ryusui-hiro/document-svg/plugins/document-svg/skills/document-svg/SKILL.md

---
name: document-svg
description: Convert supported PDF, Office/OpenDocument, web/text, diagram, CAD/CAM/3D, CAE, raster, chart, table, and math inputs into per-page SVG, transform SVG pages (minify, format, scale, remove metadata), or package SVG pages into supported Office, CAD/CAM/3D, diagram, data, HTML viewer, and UI-code outputs with docsvg. Use for document previews and batch conversions; disclose known limits and warnings, and do not claim reverse Office packaging reconstructs document semantics.
---

# Document SVG

Use this skill when the requested output is a directory of self-contained SVG pages. The converter selects the parser from the input file and writes `page-NNNN.svg` plus `conversion.json`.

## Convert

DICOM Part 10 images (`.dcm`, `.dicom`) render one PNG-backed SVG page per frame. DICOM Structured Reports (`.sr.dcm`, `.dicom-sr` or SR SOP Class) render bounded Content Sequence tables. Supported compressed transfer syntaxes include JPEG and JPEG 2000 Part 1 lossless/general (`.90`/`.91`) plus RLE Lossless; JPEG 2000 dimensions/components/precision are checked before decoding. DICOMDIR (`DICOMDIR`, `.dicomdir`) follows image-record offsets and resolves File IDs under the DICOMDIR directory. Image previews omit patient/study attributes, but burned-in pixel text remains and is not anonymized; SR previews carry a separate PHI warning.
DICOM Encapsulated PDF Storage is rendered only when its SOP Class and `application/pdf` MIME type agree. The embedded PDF is limited to 64 MiB and uses the bounded PDF engine; DICOM attributes are omitted, but information already inside the PDF remains.

1. Resolve the input to a local supported file. Common families include PDF/FDF/XFDF form data (`.fdf`, `.xfdf`), legacy Word Binary (`.doc`, CFB `.dot` templates), text-only legacy PowerPoint Binary (`.ppt`), Excel workbooks (`.xls`, `.xlsb`), OOXML Transitional/Strict Office (including Visio `.vsdx`/`.vsdm`/`.vstx`/`.vstm` and legacy Visio XML `.vdx`), Microsoft Project XML schedules, iCalendar (`.ics`) and legacy vCalendar (`.vcs`), vCard contacts (`.vcf`, `.vcard`), MIME e-mail (`.eml`), Apple Mail messages (`.emlx`), Outlook message (`.msg`), MBOX mailbox archives (`.mbox`), MHTML web archives (`.mht`, `.mhtml`), FictionBook 2 XML e-books (`.fb2`, `.fb2.zip`), DocBook 4/5 XML (`.dbk`, `.docbook`), TEI P5 scholarly XML (`.tei`, `.tei.xml`), ALTO OCR/layout XML (`.alto`, `.alto.xml`), METS archive XML (`.mets`, `.mets.xml`), MARCXML (`.marcxml`, `.marc.xml`), MARC21 ISO 2709 (`.marc`, `.iso2709`), PREMIS XML (`.premis`, `.premis.xml`), IIIF Presentation JSON (`.iiif.json`, `.manifest.json`), EAD finding-aid XML (`.ead`, `.ead.xml`), EAC-CPF authority XML (`.eac-cpf`, `.eac`), Dublin Core XML (`.dc.xml`, `.dublin.xml`), ISO 19115/19139 XML metadata (`.iso19115`, `.iso19139`, `.gmd.xml`), OASIS UBL 2.x business XML (`.ubl`, `.ubl.xml`), S1000D Data Module XML (`.s1000d`, `.dmodule`), MODS XML (`.mods`, `.mods.xml`), DITA topics/maps (`.dita`, `.ditamap`), PDB coordinate models (`.pdb`, `.ent`), HWPX (`.hwpx`), COLLADA (`.dae`), X3D (`.x3d`), XMind (`.xmind`), NIfTI (`.nii`, `.nii.gz`), FITS (`.fits`, `.fit`, `.fts`, `.fits.gz`), MRC (`.mrc`, `.map`, `.mrc.gz`), PalmDOC/MOBI e-books (`.mobi`, `.prc`, `.azw`), RTF, XPS/OpenXPS (`.xps`, `.oxps`), standalone JPEG 2000 (`.jp2`, `.j2k`, `.j2c`, `.jpc`, `.jpx`), multi-page TIFF/BigTIFF (`.tif`, `.tiff`), CBZ comic archives (`.cbz`), SubRip/WebVTT subtitles (`.srt`, `.vtt`), TTML/DFXP subtitles (`.ttml`, `.dfxp`), XLIFF localization files (`.xlf`, `.xliff`), Jupyter notebooks (`.ipynb`), Quarto/R Markdown (`.qmd`, `.Rmd`, `.rmarkdown`), V2000/core V3000 MOL/SDF chemical structures (`.mol`, `.sdf`, `.sd`) and V2000 RXN reactions (`.rxn`), Abaqus (`.inp`), LS-DYNA Keyword (`.k`, `.key`), MEDIT ASCII/binary meshes (`.mesh`, `.medit`, `.meshb`), OFF polygon meshes (`.off`), IFC4 BIM (`.ifc`, `.ifcxml`, `.ifczip`), Nastran Bulk Data (`.bdf`, `.nas`, `.nastran`), KiCad PCB boards (`.kicad_pcb`), and UNV/UFF (`.unv`) mesh decks, SU2 CFD meshes (`.su2`), OpenFOAM polyMesh cases (`.foam`), EnSight Gold ASCII cases (`.case`, `.geo`), PLOT3D ASCII grids (`.p3d`, `.plot3d`, `.p3`), VRML97 text meshes (`.wrl`, `.vrml`), ASCII XYZ point rows (`.xyz`), PCL point clouds (`.pcd`), ASTM E57 (`.e57`), Leica PTS unstructured (`.pts`) and PTX structured (`.ptx`) point clouds, ASPRS LAS/LAZ (`.las`, `.laz`), and legacy Excel workbooks (`.xls`, `.xlt`, `.xla`), SYLK spreadsheets (`.slk`), DIF tables (`.dif`), FASTA/FASTQ sequences (`.fa`, `.fasta`, `.fq`, `.fastq`), GFF3/GTF annotations (`.gff`, `.gff3`, `.gtf`), BED/BEDGraph intervals (`.bed`, `.bedgraph`, `.bg`), VCF variants (`.vcf`), SAM alignments (`.sam`), WIG/Wiggle signals (`.wig`, `.wiggle`), MAF multiple alignments (`.maf`), Newick phylogenetic trees (`.nwk`, `.newick`, `.tree`), Stockholm alignments (`.sto`, `.stockholm`), CLUSTAL alignments (`.aln`, `.clustal`, `.clustalw`), NEXUS trees (`.nex`, `.nexus`), GenBank flat files (`.gb`, `.gbk`, `.genbank`), EMBL-Bank flat files (`.embl`, `.emb`), UniProtKB/Swiss-Prot protein flat files (`.dat`, `.uniprot`, `.swissprot`), RIS bibliography (`.ris`), SPICE/ngspice netlists (`.cir`, `.sp`, `.spice`, `.ckt`, `.net`), KiCad legacy Eeschema schematics (`.sch`), KiCad 6+ S-expression schematics (`.kicad_sch`), LTspice schematics (`.asc` Version signature), Autodesk EAGLE XML schematics (`.sch` eagle signature), plus Excel Binary Workbook (`.xlsb`); OpenDocument Text/spreadsheets/presentations/drawings (`.odt`, `.ott`, `.fodt`, `.ods`, `.ots`, `.fods`, `.odp`, `.otp`, `.fodp`, `.odg`, `.otg`, `.fodg`); HTML/EPUB/Markdown/plain text/AsciiDoc (including bounded local `image::target[attrs]` PNG/JPEG block macros)/reStructuredText (`.rst`, `.rest`)/Org-mode (`.org`)/GNU gettext catalogs (`.po`, `.pot`)/BibTeX (`.bib`, `.bibtex`); draw.io, BPMN 2.0 (`.bpmn`, `.bpmn2`), CMMN 1.1 (`.cmmn`), DMN 1.1–1.5 (`.dmn`), ReqIF (`.reqif`), XMI (`.xmi`), DOT, Mermaid, PlantUML, D2, Excalidraw; ARFF (`.arff`), JSON-LD 1.1 (`.jsonld`, `.json-ld`), NetCDF classic (`.nc`, `.nc3`, `.cdf`), GraphML (`.graphml`), GEXF (`.gexf`), XGMML (`.xgmml`), Graph Modeling Language (`.gml`), CSV/TSV, TOML (`.toml`), YAML 1.2 (`.yaml`, `.yml`), Java Properties (`.properties`), generic XML (`.xml` fallback), and JSON (`.json`), RFC 7464 JSON Text Sequences (`.jsons`, `.jsonseq`, `.jsonl`), dBASE III/III+ tables (`.dbf`), GeoPackage (`.gpkg`), RFC 8142 GeoJSON Text Sequences (`.geojsons`, `.geojsonseq`) and newline-delimited `.geojsonl`, TopoJSON (`.topojson`), GeoJSON/GeoRSS/GML/GPX/KML/KMZ, ESRI Shapefile (`.shp`) and WKT/EWKT map geometries (`.gpkg`, `.geojsons`, `.geojsonl`, `.topojson`, `.geojson`, `.rss`, `.atom`, `.georss`, `.gml`, `.gpx`, `.kml`, `.kmz`, `.shp`, `.wkt`, `.ewkt`), charts, LaTeX formulas and bounded complete-document previews (including local PNG/JPEG \includegraphics), QR, raster/SVG/SVGZ; and CAD/CAM/CAE such as ASAM OpenDRIVE `.xodr`, ASAM OpenSCENARIO `.xosc`, ASCII/Binary DXF, Gerber, HP-GL, G-code, Excellon, STL/3MF/glTF/GLB/STEP/IGES/OBJ/PLY, Gmsh, and VTK (`.vtk`, `.vtu`, `.vtp`, `.vti`, `.vtr`, `.vts`). Read `docs/SUPPORT.md` for exact format coverage and limitations.
2. Choose a dedicated output directory. If the user did not name one, use `<input-stem>-svg` beside the input. Never reuse a non-empty directory unless the user explicitly asks to mix or replace its contents.
3. Run the bundled wrapper using its absolute path from this skill directory:

   ```bash
   scripts/convert-document.sh <input> <output> [docsvg options]
   ```

   Use `--jobs N` only to parallelize PDF pages. Keep the default limits unless the user explicitly needs different bounds.
   Use `--outline-embedded-pdf-text` only when the user explicitly prioritizes PDF visual fidelity over editable SVG text. Report every resulting font-rights warning and do not describe outlined text as editable.
4. Read `<output>/conversion.json`. Report the page count, source format, output directory, and every top-level or page warning. Treat a non-empty `warnings` array or a positive page `warning_count` as requiring review; do not describe that result as a perfect reproduction.
5. When visual fidelity matters, render or inspect representative SVG pages with the available image/browser tooling.
   For Codex/app previews, prefer a deterministic PNG companion because Markdown, Quick Look,
   and embedded browser SVG support can differ. Run:

   ```bash
   scripts/render-preview.sh <svg-file-or-directory> <new-preview-directory> [width]
   ```

   Display the generated absolute `.png` path in Codex and link the original `.svg` separately.
   Read `preview.json` for page ordering. The preview runner rejects active SVG content and refuses
   non-empty output directories.

## Transform SVG

1. Resolve the input to an `.svg` file.
2. Choose an output file path (e.g. `<input-stem>.transformed.svg`).
3. Run:

   ```bash
   scripts/transform-document.sh <input.svg> <output.svg> [options]
   ```

   Supported transform options:
   - `--minify`: Strip unnecessary whitespace, comments, and redundant tokens to reduce file size.
   - `--responsive`: Remove fixed width/height and ensure viewBox is set for responsive web scaling.
   - `--monochrome <color>`: Unify all fill and stroke colors to a single monochrome color (e.g. `#000000`).
   - `--precision <digits>`: Clamp coordinate precision to N decimal digits.
   - `--remove-metadata`: Strip `<metadata>`, `<desc>`, and `data-*` attributes.

## Reverse to OOXML, PDF, CAD, CAM, or draw.io

1. Resolve the input to one `.svg` file or a directory containing SVG pages. Directory pages are ordered lexicographically, so prefer `page-NNNN.svg` names.
2. Choose a new output file ending in a supported extension, such as `.pptx`, `.docx`, `.xlsx`, `.pdf`, `.drawio`, CAD/CAM/3D (`.dxf`, `.gcode`, `.gbr`, `.plt`, `.drl`, `.stl`, `.3mf`, `.obj`, `.ply`, `.step`, `.iges`), simulation (`.msh`, `.vtk`), diagrams (`.dot`, `.mmd`), data/math (`.md`, `.csv`, `.tex`), PNG, WebP, standalone HTML viewer (`.html`), React/Vue/Svelte code, SVG path data, or `.datauri`.
3. Run:

   ```bash
   scripts/reverse-document.sh <input.svg-or-directory> <output>
   ```

4. Report the output format and page count, and always disclose that Office outputs embed SVGs as vector images with PNG compatibility fallbacks (PPTX uses one SVG per slide, DOCX one SVG per page, and XLSX one SVG per sheet). CAD/CAM/CAE outputs (`.dxf`, `.gcode`, `.gbr`, `.plt`, `.drl`, `.stl`, `.obj`, `.step`, `.msh`, `.vtk`) generate native vector geometry, 3D meshes, boundary curves, toolpaths, or simulation grids.
5. Do not describe reverse conversion as a lossless restoration of the original Office document. Paragraphs, tables, spreadsheet cells and formulas, charts, comments, masters, and other semantics are not reconstructed.
6. A `.drawio` output is the exception: an SVG that still carries its diagram source is restored as editable shapes. That applies to draw.io's own exports made with "Include a copy of my diagram" and to SVGs this converter wrote with `--embed-drawio-source`. The report says how many pages were restored that way; report that number instead of assuming, because the rest are pictures inside a diagram.

## CLI availability

The repository installer normally places `docsvg` on `PATH`. If it is unavailable, the wrapper can run the checked-out Rust repository when either the current directory is that repository or `DOCUMENT_SVG_REPO` points to it. Otherwise, ask the user to run `./scripts/install-codex-plugin.sh` from the repository root.

## Constraints

- The converter intentionally rejects encrypted PDFs and does not bypass access controls.
- Legacy PowerPoint Binary `.ppt` presentations follow the live `CurrentUserAtom`/`UserEditAtom`/persist-directory chain, then extract UTF-16 or low-byte Unicode text from slide OfficeArt textboxes and outline references into A4 flow pages. Slide geometry, visual styles, images, charts, tables, media, notes, and embedded objects are omitted; encrypted decks are rejected. See `docs/SUPPORT.md` for limits.
- Legacy Word Binary `.doc` documents and CFB `.dot` templates (`.dot` is content-sniffed to preserve Graphviz) extract the main-story text from the bounded FIB/CLX piece table or simple text range. UTF-16 and common compressed code pages are supported. Text is flowed to A4 pages; tables are flattened, and original formatting, pagination, images, headers/footnotes and embedded objects are omitted. Encrypted files are rejected; macros are never executed. See `docs/SUPPORT.md` for limits.
- KiCad PCB `.kicad_pcb` files are parsed as bounded S-expressions. The 2D preview renders common tracks, vias, pads, Edge.Cuts, board/footprint artwork, and cached zone fills; it never evaluates DRC, refills zones, opens 3D/image paths, or loads external libraries. Unsupported custom pads/curves and non-unit affine-scaled footprints are warned and omitted.
- PDF JPXDecode grayscale/RGB/CalGray/CalRGB images with 1–16-bit unsigned, full-resolution components are dimension-checked and decoded to PNG within fixed limits. One embedded alpha channel is preserved when `SMaskInData=1`; DeviceGray/DeviceRGB/CalGray/CalRGB preblended mode 2 is unblended using a valid `/Matte`, and bounded DeviceGray external `/SMask` images are applied when no matte or nested mask is present. Default/0 ignores embedded alpha. Explicit `/Mask`, unsupported matte or soft-mask color spaces, unsupported JPX color spaces, and subsampling remain as JPEG 2000 data with a warning; PDF-level masks may be lost from the SVG fallback. `BitsPerComponent` is taken from the codestream as required by PDF.
- OpenDocument Text previews preserve headings, paragraphs, lists, and tables, and embed bounded package-linked PNG/JPEG images as centered flow blocks. Legacy OpenOffice XML packages (`.sxw`, `.stw`, `.sxg`) are routed through the same bounded ODT engine after validating their `application/vnd.sun.xml.*` mimetype. Styles and exact pagination are not reconstructed; image anchors and wrapping are approximated, and external or inline-binary images are reported and omitted.
- EPUB previews follow the OPF spine and embed bounded package-linked PNG/JPEG XHTML `img` resources. Remote references, CSS backgrounds, SVG and other image sources are not fetched or reconstructed.
- DocBook 4/5 `.dbk`/`.docbook` previews render bounded titles, sections, paragraphs, lists, source blocks, simple tables, and validated local PNG/JPEG `imagedata`/`graphic` resources. DTDs, XInclude, external links, MathML, scripts, and publisher extensions remain inert.
- Standalone HTML previews embed bounded relative PNG/JPEG `img src` files only when canonical paths remain inside the input directory tree. Image placement, CSS sizing and wrapping are approximated; external and escaping paths are not fetched.
- Markdown previews embed bounded local PNG/JPEG resources from standalone or paragraph `![alt](path)` references when resolved paths remain inside the input directory tree; images render as flow blocks, while heading/list/quote/table/code images stay as alt text.
- OpenDocument Spreadsheet previews preserve cached cell values and embed bounded package-linked PNG/JPEG images after each sheet table; legacy OpenOffice XML packages (`.sxc`, `.stc`) use the same safe package checks. Cell anchoring, chart/vector drawings, styles, and formula recalculation are not reproduced.
- OpenDocument Presentation/Drawing previews preserve page order, size, common vector shapes, editable text, and bounded PNG/JPEG images linked from the ODF package. Legacy OpenOffice XML presentations/drawings (`.sxi`, `.sti`, `.sxd`, `.std`) are accepted through the same engines. External and inline binary images plus charts, tables, OLE, and advanced effects are omitted or approximated with warnings; see `docs/SUPPORT.md` for limits.
- Visio Open XML (`.vsdx`/`.vsdm`/`.vstx`/`.vstm`) and legacy VDX XML use bounded page/ShapeSheet rendering; legacy Visio CFB (`.vsd`/`.vss`/`.vst`/`.vsw`) is summarized as inert stream metadata without decoding opaque drawing payloads.
- ZIP-backed Apple iWork Pages/Numbers/Keynote packages (`.pages`/`.numbers`/`.key`) expose bounded package marker metadata only; IWA protobuf, formulas, media, previews, scripts and external links remain inert. `.key` is distinguished from LS-DYNA by ZIP signature.
- Autodesk DWG (`.dwg`) reads only the six-byte AC10xx version header and file size; compressed sections, entities, macros, embedded objects and external references remain inert.
- Nastran Output2 (`.op2`) performs bounded record-framing and table-label preflight only; model/result payloads, external paths and solver operations remain inert.
- IPC-2581 (`.ipc2581`/`.ipc-2581`/`.cvg`) summarizes PCB Content/BOM/ECAD/AVL structure and manufacturing counts without rendering coordinates, toolpaths, attachments or executing operations.
- Siemens JT (`.jt`) reads only the fixed Version header and byte-order marker; TOC/LSG, tessellation, Parasolid geometry, PMI and external resources remain inert.
- Rhino/OpenNURBS 3DM (`.3dm`) reads only the stable start marker and bounded header bytes; NURBS/mesh chunks, plug-ins, textures and external resources remain inert.
- Microsoft Access ACE/Jet (`.accdb`/`.accde`/`.mdb`/`.mde` and related extensions) reads only the first-page engine marker and bounded metadata; database objects, VBA/data macros, attachments, encryption and linked paths remain inert.
- Dassault 3DXML (`.3dxml`) validates the local Manifest→Root relationship and bounded product-structure XML; binary 3DRep tessellation, external files, textures and viewer automation remain inert.
- HDF5 scientific containers (`.h5`/`.hdf5`/`.hdf`/`.h5part`) and CGNS/HDF5 CFD files (`.cgns`) are preflighted from their signature and superblock without loading datasets, links, filters, or solver payloads.
- RTF previews preserve supported ANSI codepages, Unicode escapes, paragraphs, explicit `\page` breaks, bounded embedded PNG/JPEG pictures, and declared picture goal dimensions. Anchors/cropping/wrapping are approximated; EMF/WMF pictures, objects, and unsupported media are omitted with warnings.
- XPS/OpenXPS (`.xps`/`.oxps`) and Autodesk DWFx (`.dwfx`) follow internal fixed-document relationships and render basic Path/Glyphs content plus embedded PNG/JPEG ImageBrushes clipped to Path bounds. Embedded fonts, exact glyph advances, gradients/cropping and resource dictionaries are warned or approximated; classic DWF payloads and external resources are never fetched.
- TIFF/BigTIFF (`.tif`/`.tiff`) emits one SVG per image directory and embeds a decoded PNG. Unsigned-integer grayscale (including packed 1/2/4-bit samples), RGB/RGBA, and CMYK are supported; WhiteIsZero/BlackIsZero is honored and channels above 8-bit are reduced to 8-bit. Palette, signed/floating-point samples, and ICC profiles are not interpreted. Per-page and total pixel/data limits and `max_pages` apply.
- DICOM Part 10 (`.dcm`, `.dicom`) emits one SVG per image frame and applies available Modality/VOI transformations. Patient/study metadata is omitted, but burned-in annotations remain; the preview is not de-identification. Only grayscale/RGB 8/16-bit pixels and supported transfer syntaxes are decoded; JPEG 2000 Part 1 `.90`/`.91` frame dimensions, component count, precision, signedness and subsampling are checked against DICOM attributes before decode. JPEG-LS, JPEG 2000 YBR_RCT/YBR_ICT color conversion, Part 2, HTJ2K, orientation and physical pixel spacing are not handled.
- DICOMDIR (`DICOMDIR`, `.dicomdir`) follows root/next/lower-level Directory Record offsets and renders referenced `IMAGE` records in hierarchy order. File IDs are validated and canonicalized inside the DICOMDIR folder, and duplicate/missing/unsupported references are skipped with warnings.
- DICOM Encapsulated PDF Storage (`1.2.840.10008.5.1.4.1.1.104.1`) accepts only `application/pdf`, checks the optional declared length and padding, and renders the bounded embedded stream with the PDF engine. DICOM attributes are not copied, but PDF content can still identify a patient, so the preview is not de-identification.
- FDF form data (`.fdf`; content sniffing) uses the PDF object/xref grammar to render fully-qualified field hierarchy, types, safe values, password masking, choice options and action/attachment counts. JavaScript, submit/launch actions, file specifications, embedded files and external URLs remain inert or redacted; no form submission or PDF page rendering runs. Limits are 64 MiB input, 500,000 objects, depth 64, 100,000 fields, 2 MiB/value and 32 MiB total values. Source: [Adobe FDF reference](https://opensource.adobe.com/dc-acrobat-sdk-docs/pdfstandards/pdfreference1.2.pdf).
- XFDF XML form data (`.xfdf`, `.xfdf.xml`; content sniffing) renders bounded fully-qualified field/value hierarchy, sensitive-field masking, rich-text and annotation counts, and PDF target/ID counts. PDF references, actions, JavaScript, rich-text payloads, appearance data and external URLs remain inert or redacted; no form submission, annotation import or PDF rendering runs. Limits are 64 MiB input, 1,000,000 XML events, 500,000 nodes, depth 96, 100,000 fields and 100,000 rows. Source: [ISO 19444-1 XFDF](https://www.iso.org/standard/74272.html).
- DICOM Structured Reports (SR) render Basic Text, Enhanced, Comprehensive, Comprehensive 3D, Extensible, CAD, dose, agent and related SOP Classes as bounded Content Sequence rows for TEXT/NUM/CODE/CONTAINER items, concepts, units and relationships. Referenced images/audio/waveforms, UIDs and patient/study attributes are omitted; SR content may contain PHI and is not de-identification. Limits are 128 MiB input, 1,000,000 structural tokens, 100,000 elements, depth 64 and 200,000 rows. Source: [DICOM PS3.3 Structured Report IODs](https://dicom.nema.org/medical/dicom/current/output/chtml/part03/sect_A.35.html).
- Microsoft Project XML (`.xml` with the Microsoft Project namespace, or `.mspdi`) renders bounded task Gantt pages with supplied dates, progress, milestones, and simple predecessor arrows. It rejects DTDs, does not fetch links or external entities, and does not recalculate work calendars or schedules; see `docs/SUPPORT.md` for limits.
- PCL PCD (`.pcd`) accepts ASCII, little-endian binary, and LZF-compressed point clouds. Bounded XYZ point marks preserve packed or separate RGB colors, quantized only above 512 color groups. Other fields and non-default VIEWPOINT poses are not applied.
- XYZ ASCII (`.xyz`) accepts common named coordinate/intensity/RGB/normal columns or homogeneous 3/4/6/7/9/10-field layouts with whitespace/comma separators. Intensity is scaled across the observed range; units, CRS and sensor pose are not inferred. Black RGB is retained and normals are omitted.
- ASTM E57 (`.e57`) reads CRC-protected XML and point-data pages, applies per-scan poses, converts spherical coordinates, and preserves normalized RGB or intensity. It caps decoding at 20 million points and previews at 200,000 points. Scan images, CRS reprojection, and non-coordinate attributes are omitted.
- Leica PTS (`.pts`) reads bounded unstructured XYZ/intensity or XYZ/intensity/RGB records; legacy signed integer and normalized decimal intensity are mapped to grayscale, and Leica's reserved no-color RGB uses a blue fallback. The origin is valid; one deterministically sampled page is capped at 200,000 points.
- Leica PTX (`.ptx`) reads structured multi-scan grids, applies the per-scan registration transform and preserves RGB, or displays intensity-only scans in grayscale. Missing XYZ cells and sensor/grid metadata are omitted; deterministic sampling is capped at 200,000 points total.
- Legacy Excel (`.xls`, `.xlt`, `.xla`) renders cached cell values in bounded worksheet pages after validating BIFF dimensions, cell coordinates, and shared-string expansion. Hidden sheets are included with a warning. Formula recalculation, styling, merged-cell geometry, charts, and drawings are omitted; macros are never executed.
- SYLK `.slk` parses bounded `ID`/`B`/`C`/`F`/`E` records into paginated inert tables. Cell coordinates and cached values are retained; formulas, formatting, and other metadata are never evaluated.
- DIF `.dif` parses bounded TABLE/VECTORS/TUPLES/DATA headers and BOT/EOD tuples into inert paginated tables. Numeric, string, boolean, NA and ERROR values are displayed without formula evaluation.
- FASTA/FASTQ sequence files render bounded identifier, length, GC/ambiguity and sequence/quality summaries. FASTQ sequence and quality lengths are checked; no alignment or Phred conversion is performed.
- GFF3/GTF `.gff`/`.gff3`/`.gtf` renders validated nine-column feature annotations and attributes. Directives and embedded FASTA tails are omitted; no hierarchy or sequence analysis executes.
- BED `.bed` and bedGraph `.bedgraph`/`.bg` validate zero-based half-open intervals, optional BED12 blocks and finite signal values as inert tables. Track/browser directives and remote lookups are never loaded.
- VCF `.vcf` renders validated fixed variant columns plus inert FORMAT/sample fields. Metadata/reference URLs and embedded FASTA are omitted; vCard `.vcf` is selected when the VCF signature is absent.
- SAM `.sam` renders validated 11-field alignments and optional tags as inert tables. Header metadata and reference URLs are ignored; no CIGAR projection, genotype analysis, or external resource access occurs.
- WIG/Wiggle `.wig`/`.wiggle` expands fixedStep and variableStep signal declarations into bounded one-based closed interval tables. Track/browser and remote references are ignored.
- MAF `.maf` renders bounded `a`/`s` multiple-alignment blocks with coordinate and ungapped-size validation. Optional metadata, reference lookup and coordinate liftover remain inert.
- Newick `.nwk`/`.newick`/`.tree` renders the first bounded semicolon-terminated phylogenetic tree as a directed graph. Quoted labels, finite branch lengths and nested comments are validated; extra trees, taxonomy/sequence lookup, rooting and distance calculations remain inert.
- Stockholm `.sto`/`.stockholm` renders bounded Stockholm 1.0 alignment blocks, including split sequence rows. `#=GF`/`#=GS`/`#=GC`/`#=GR` annotations remain inert and external profile/sequence lookups are never performed.
- CLUSTAL `.aln`/`.clustal`/`.clustalw` renders bounded block alignments; sequence fragments are concatenated, residue counts and consensus rows remain inert, and external lookup or alignment execution is never performed.
- NEXUS `.nex`/`.nexus` extracts the first bounded `TREE`/`UTREE` statement from `BEGIN TREES` and renders it through the Newick graph path. TAXA/TRANSLATE metadata and additional blocks remain inert.
- GenBank `.gb`/`.gbk`/`.genbank` renders bounded LOCUS metadata, feature counts, and ORIGIN sequence previews as inert tables. Accessions, feature locations, and external sequence resources are never resolved.
- EMBL-Bank `.embl`/`.emb` renders bounded ID/AC/DE/FT/SQ records and sequence previews as inert tables. Database cross-references, feature locations, and external sequence resources are never resolved.
- UniProtKB/Swiss-Prot `.dat`/`.uniprot`/`.swissprot` renders bounded ID/AC/DE/GN/OS/FT/SQ protein records. Reviewed status, accessions, metadata, feature counts and sequence previews are inert; REST, taxonomy and cross-reference lookups never run.
- RIS `.ris` renders bounded `TY`/`ER` citation records with authors, title, date, journal, pages, DOI, URL, keywords and abstract previews. Six-space continuations are supported; DOI/URL and external citation lookups remain inert.
- SPICE/ngspice `.cir`/`.sp`/`.spice`/`.ckt`/`.net` renders bounded element cards, nodes and values as inert tables. Dot commands, `.include`/`.lib` paths, models and simulation controls are never executed or opened.
- KiCad legacy Eeschema `.sch` renders bounded `$Comp`, wires, labels, notes, and junctions as a deterministic mil-coordinate approximation. Cache libraries, external symbols, images, models, and DRC/ERC are never loaded.
- KiCad 6+ `.kicad_sch` renders bounded S-expression symbol instances, wire/bus segments, labels, text, and junctions. Embedded library definitions, pin connectivity, hierarchy, images, models, and ERC/DRC remain inert.
- LTspice `.asc` with a `Version` header renders bounded WIRE/FLAG/SYMBOL/SYMATTR/TEXT and basic graphics, including BOM-marked UTF-16. `.asy` libraries, external models, includes, and simulation commands are never opened or executed; ESRI ASCII Grid signatures remain separate.
- Autodesk EAGLE XML `.sch` with an `<eagle>` root renders bounded parts, instances, wires, labels, and text. Library package geometry, scripts, external files, pin connectivity, and DRC/ERC remain inert; KiCad legacy `.sch` is selected by its own signature.
- Excel Binary Workbook (`.xlsb`) streams cached worksheet values into bounded pages after checking ZIP entries, BIFF12 record lengths, used ranges, and shared-string expansion. Hidden worksheets are included with a warning. Formulas are not recalculated, styles and charts are omitted, macros are never executed, and macro-sheet workbooks are unsupported.
- ASPRS LAS/LAZ (`.las`, `.laz`) supports LAS 1.0–1.4 with optional RGB and deterministic point samples capped at 200,000. Uncompressed LAS uses seeks; LAZ decoding is capped at 20 million source points. CRS transforms and other point attributes are omitted.
- V2000/core V3000 MOL/SDF (`.mol`, `.sdf`, `.sd`) draws bounded atom/bond connection tables one molecule per page. Supplied coordinates, common bond orders, formal charges/isotopes, and up/down single-bond wedges and hash marks are shown; SDF data fields are omitted and never evaluated. Core V3000 atom/bond tables are supported; Sgroups, advanced stereochemistry, query chemistry and chemical calculations are unsupported.
- V2000 RXN (`.rxn`) renders a single reaction page with up to two reactants and two products. It reuses the MOL depiction in separate panels with plus signs and a reaction arrow; V3000 RXN containers, conditions, agents, and chemical validation are omitted.
- ESRI Shapefile (`.shp`) renders point, line, polygon and multipoint records, validates an optional SHX index, and accepts recognized degree-based WGS 84 geographic PRJ metadata. Missing PRJ is explicitly treated as an assumption; projected, non-degree or unknown CRS is rejected because reprojection is not applied. DBF fields and Z/M values are omitted; MultiPatch is unsupported.
- ESRI ASCII Grid (`.asc`) reads NCOLS/NROWS, a matching lower-left corner or center origin, CELLSIZE, optional NODATA_VALUE (default -9999), and row-major cell values. It produces a PNG-backed SVG heatmap with transparent NoData cells and a value legend; an all-NoData grid stays transparent without a numeric scale. CRS reprojection and thematic class breaks are not applied. Input, dimensions, cell count, line length, and encoded PNG size are bounded.
- dBASE III/III+ (`.dbf`) reads bounded classic 32-byte-descriptor tables and paginates 100 rows × 32 columns. Character, numeric, float, logical and date fields render; deleted rows are skipped; memo/unsupported fields are placeholders. Common `.cpg` aliases are decoded; unsupported versions/code pages fail clearly. `docs/SUPPORT.md` lists file, row, cell and record-width limits.
- TOML (`.toml`) renders nested configuration values as inert key paths. Input, line length/count, recursion, values, strings, paths and rendered text are bounded; values are never evaluated. Float spellings may be normalized.
- YAML 1.2 (`.yaml`, `.yml`) renders multi-document configuration as inert key paths. Aliases are not expanded, tags are not applied, complex mapping keys are rejected, and parser events, nesting, document count, scalars, paths and rendered text are bounded.
- OpenAPI/Swagger (`.openapi.json`, `.swagger.json`, `.openapi.yaml`, `.swagger.yaml`) renders title/version, servers, component counts, and endpoint/operation/summary/response rows. `$ref`, externalDocs, server URLs, callbacks, links, examples, and security schemes remain inert; no reference resolution, network access, or API execution occurs.
- WSDL 1.1/2.0 (`.wsdl`, `.wsdl.xml`; content sniffing) renders bounded service, port, binding, portType/interface, operation, message, import/include and embedded-schema metadata. Endpoint addresses, schema/import URLs, documentation, credentials and payloads remain inert; no SOAP/HTTP request or code generation runs. Limits are 64 MiB input, 1,000,000 XML events, 500,000 nodes, depth 96 and 200,000 rows. Source: [W3C WSDL](https://www.w3.org/TR/wsdl.html).
- OPML 1.0/2.0 (`.opml`, `.opml.xml`; content sniffing) renders version/title/date metadata and bounded hierarchical outline rows with type, depth and feed-outline counts. Feed URLs, HTML links, owner email, descriptions and extension values remain inert; linked feeds, enclosures, images and scripts are never fetched or executed. Limits are 32 MiB input, 500,000 XML events, 300,000 nodes, depth 96 and 200,000 rows. Source: [OPML 2.0 specification](https://opml.org/spec2.opml).
- RSS 2.0 / Atom 1.0 (`.rss`, `.atom`, `.georss`; no GeoRSS geometry or content sniffing) renders channel/feed and item/entry title/date plus bounded link/author/content/enclosure counts. Links, descriptions, summaries, content payloads, author addresses, enclosures and external resources remain inert; no feed refresh, script or network operation runs. Limits are 32 MiB input, 500,000 XML events, 300,000 nodes, depth 96 and 100,000 rows. Sources: [RSS 2.0 Specification](https://www.rssboard.org/rss-specification), [RFC 4287 Atom](https://www.rfc-editor.org/info/rfc4287/).
- Apple Property List (`.plist`, `.plist.xml`; content sniffing) renders XML key paths, dictionary/array structure, scalar types and data-byte counts, while binary `bplist00` renders validated trailer/offset/object-marker metadata. URL and secret-like values, data payloads and external resources remain inert or redacted; no application data is executed. Limits are 64 MiB input, 1,000,000 XML events, 500,000 XML nodes/objects, depth 96 and 200,000 rows. Source: [Apple PropertyListSerialization](https://developer.apple.com/documentation/foundation/propertylistserialization).
- TEI P5 scholarly XML (`.tei`, `.tei.xml`; content sniffing) renders bounded `teiHeader` title/author/date metadata and `text/body` divisions, headings, paragraphs, notes, lists, figures and table-cell counts. Targets, URLs, facsimiles, identifiers, external images, scripts and entities remain inert; no linked resource or document code runs. Limits are 64 MiB input, 1,000,000 XML events, 500,000 nodes, depth 128 and 200,000 rows. Source: [TEI P5 Guidelines](https://www.tei-c.org/release/doc/tei-p5-doc/en/html/).
- ALTO OCR/layout XML (`.alto`, `.alto.xml`; content sniffing) renders bounded `Layout/Page/TextLine/String` rows with OCR `WC` confidence values. Source-image filenames, URLs, styles, alternatives and processing details remain inert; images, scripts and external resources are never opened. Limits are 64 MiB input, 1,000,000 XML events, 500,000 nodes, depth 96 and 200,000 rows. Source: [Library of Congress ALTO](https://www.loc.gov/standards/alto/).
- METS archive XML (`.mets`, `.mets.xml`; content sniffing) renders bounded `fileSec`/`fileGrp`/`file` MIME and size metadata plus `structMap` division hierarchies and `fptr`/`mptr` counts. FLocat/MDRef URLs, embedded payloads, ALTO/image files, scripts and external resources remain inert; no linked file is opened. Limits are 64 MiB input, 1,000,000 XML events, 500,000 nodes, depth 96 and 200,000 rows. Source: [Library of Congress METS](https://www.loc.gov/standards/mets/).
- MARCXML (`.marcxml`, `.marc.xml`; content sniffing) renders bounded MARC 21 record/leader/controlfield/datafield/subfield rows with field counts. 856 and other URL values, identifiers and extension payloads remain inert; no catalog, schema or network operation runs. Limits are 64 MiB input, 1,000,000 XML events, 500,000 nodes, depth 96 and 200,000 rows. Source: [Library of Congress MARCXML](https://www.loc.gov/marc/marcxml.html).
- MODS 3.x XML (`.mods`, `.mods.xml`; content sniffing) renders bounded title/subtitle, personal/corporate name, publisher/date, genre, subject, identifier and location metadata. Authority/value/location URLs, notes, arbitrary extension values and external resources remain inert or redacted; no catalog, schema or network operation runs. Limits are 64 MiB input, 1,000,000 XML events, 500,000 nodes, depth 96 and 200,000 rows. Source: [Library of Congress MODS](https://www.loc.gov/standards/mods/).
- MARC21 ISO 2709 (`.marc`, `.iso2709`; content sniffing) validates leader, directory, field boundaries and terminators, then renders bounded control/data/subfield rows. 856/URL values and unrecognized payloads remain inert or redacted; `.mrc` remains reserved for MRC/CCP4 volumes. Limits are 64 MiB input, 100,000 records, 500,000 fields, 1,000,000 subfields and 200,000 rows. Source: [MARC 21 record structure](https://www.loc.gov/marc/specifications/specrecstruc.html).
- PREMIS 2.x/3.0 preservation XML (`.premis`, `.premis.xml`; content sniffing) renders bounded Object, Event, Agent and Rights entity types, safe dates/names and relationship counts. Checksums, URIs, rights text, detailed payloads and preservation actions remain inert or redacted; no application or network operation runs. Limits are 64 MiB input, 1,000,000 XML events, 500,000 nodes, depth 96 and 200,000 rows. Source: [Library of Congress PREMIS](https://www.loc.gov/standards/premis/).
- IIIF Presentation 2.1/3.0 JSON (`.iiif.json`, `.iiif-manifest.json`, `.manifest.json`; content sniffing) renders bounded Manifest/Collection labels, Canvas order/labels/dimensions, painted image counts, annotation counts, ranges and metadata-entry counts. Manifest IDs, image/service URLs, thumbnails and annotation bodies remain inert; no manifest or image service is fetched. Limits are 64 MiB input, depth 100, 300,000 JSON values, 100,000 Canvases, 300,000 annotations and 200,000 rows. Source: [IIIF Presentation API 3.0](https://iiif.io/api/presentation/3.0/).
- EAD2/EAD3 finding-aid XML (`.ead`, `.ead.xml`; content sniffing) renders bounded repository/title metadata and nested archival component (`c`/`c01`–`c12`) levels, titles, dates and counts. Digital-object URLs, identifiers, scope text, external images, scripts and entities remain inert; no archival resource is opened. Limits are 64 MiB input, 1,000,000 XML events, 500,000 nodes, depth 128 and 200,000 rows. Source: [Library of Congress EAD](https://www.loc.gov/ead/).
- EAC-CPF authority XML (`.eac-cpf`, `.eac-cpf.xml`, `.eac`; content sniffing) renders bounded entity type, identity name entries, existence-date/description counts and CPF/resource/function relation counts. Authority IDs, URIs, biographies, relation targets and external resources remain inert or redacted; no authority lookup or network operation runs. Limits are 64 MiB input, 1,000,000 XML events, 500,000 nodes, depth 96 and 200,000 rows. Source: [EAC-CPF Tag Library](https://eac.staatsbibliothek-berlin.de/schema/v3/EAC-CPF3-TL-eng.html).
- Dublin Core XML (`.dc.xml`, `.dublin.xml`, `.dublin-core.xml`; content sniffing) renders bounded DCMI title, creator, subject, publisher, date, type, format and language values with field counts. Identifier/relation/rights/description payloads and URLs remain inert or redacted; no OAI-PMH, catalog, schema or network operation runs. Limits are 32 MiB input, 500,000 XML events, 300,000 nodes, depth 80 and 100,000 rows. Sources: [DCMI XML guidelines](https://www.dublincore.org/specifications/dublin-core/dc-xml-guidelines/), [DCMES 1.1](https://www.dublincore.org/specifications/dublin-core/dces/2003-06-02/).
- ISO 19115/19139 geographic metadata XML (`.iso19115`, `.iso19115.xml`, `.iso19139`, `.gmd.xml`; content sniffing) renders bounded identification title/date/topic, hierarchy/language, CRS codes, geographic bounding boxes and quality/distribution/link/contact counts. Abstract/lineage text, identifiers, contact payloads and online-resource URLs remain inert or redacted; no network retrieval or CRS transformation runs. Limits are 64 MiB input, 1,000,000 XML events, 500,000 nodes, depth 96 and 200,000 rows. Sources: [ISO 19115-1](https://www.iso.org/standard/53798.html), [ISO 19115-3 XML implementation](https://www.iso.org/standard/80874.html).
- S1000D Data Module XML (`.s1000d`, `.dmodule`, `.dmodule.xml`; content sniffing) renders bounded DMC code attributes, title, issue/security metadata and description/procedure/step/note/list/table text. DM/ICN references, URLs, graphics, XInclude, scripts and external resources remain inert; no publication assembly runs. Limits are 64 MiB input, 1,000,000 XML events, 500,000 nodes, depth 128 and 200,000 rows. Source: [S1000D](https://s1000d.org/).
- AsyncAPI (`.asyncapi.json`, `.asyncapi.yaml`, `.asyncapi.yml`) renders title/version, servers, component counts, and channel/action/operation/summary/message rows. `$ref`, externalDocs, server URLs, examples, protocol bindings, and security schemes remain inert; no reference resolution, network access, or message/API execution occurs.
- JSON Schema (`.schema.json`, `.jsonschema`, `.schema.yaml`, `.schema.yml`) renders dialect/ID metadata and bounded schema-path/type/detail/constraint rows. `$ref`, URI values, patterns, examples, and format annotations remain inert; no reference resolution, network access, regex evaluation, or validation occurs.
- HAR (`.har`) renders bounded HTTP request/response method, URL, status, MIME, byte-size and timing rows. Secret-like query values are masked; headers, cookies, request/response bodies are omitted, and URLs are never fetched or replayed.
- WARC (`.warc`, `.warc.gz`) renders bounded record type, target URI, embedded HTTP status/MIME, date and Content-Length rows. It validates record framing, skips payload bytes, bounds gzip expansion, masks secret-like query values, and never opens archived URLs or resources.
- WACZ (`.wacz`) reads only the bounded ZIP manifest and `pages/pages.jsonl` metadata. It lists page IDs, URLs, titles, status/MIME and timestamps, masks secret-like URL queries, and never opens archive WARC payloads, CDXJ indexes or replay resources.
- Postman Collection v2.1 (`.postman_collection.json`) renders folder/request method, URL, response and auth/script metadata. Secret-like URL query values are masked; credentials, variables, headers, cookies, bodies and scripts are omitted, and no request or collection runner executes.
- GraphQL SDL (`.graphql`, `.graphqls`, `.gql`) renders bounded type/interface/input/enum/scalar/union field and signature rows. Descriptions, directives, defaults and URLs remain inert; no resolver, introspection, query, mutation or subscription executes.
- Protocol Buffers (`.proto`) renders bounded proto2/proto3 syntax/package, message field, enum value, oneof and service RPC rows. Imports, options, annotations, code generation, external files and RPC execution remain inert.
- Kubernetes manifests (`.k8s.yaml`, `.k8s.yml`, `.kubernetes.yaml`, `.kube.yaml`) render bounded resource identity and spec/status shape rows across YAML documents and JSON Lists. Secret values, templates, kubectl, Helm, cluster calls and external references remain inert.
- Docker Compose (`compose.yaml`, `compose.yml`, `docker-compose.yaml`, `docker-compose.yml`, `.compose.yaml`, `.compose.yml`) renders a bounded service inventory with image/build, ports, dependencies, volume/network/secret counts and command presence. Docker daemon access, image pull/build, command/healthcheck execution, interpolation/include/merge resolution, environment values and secret values remain inert; JSON/YAML content sniffing is supported.
- GitHub Actions workflows (`.github/workflows/*.yaml`, `.github/workflows/*.yml`) render a bounded job plan with runner, needs, step, action/run and matrix metadata. `run`/`uses` commands, expressions, environment/secret values, permissions, reusable workflows, artifacts, triggers and runner/network operations remain inert.
- JUnit-compatible XML (`junit.xml`, `test-results.xml`, `test-report.xml`, `TEST-*.xml`, `.junit.xml`, `.junit-report.xml`, `.test-results.xml`) renders bounded suite totals and pass/fail/error/skip/time counts. Failure/error logs, stdout/stderr, properties and attachments are omitted; tests, external DTDs and resources remain inert.
- SARIF 2.1.0 (`.sarif`, `.sarif.json`) renders bounded tool/rule severity groups and result counts. Messages, source locations, artifact URIs, snippets, fingerprints, fixes and invocation details remain omitted; uploads, URL fetches and code execution are never performed.
- Terraform JSON plans (`tfplan.json`, `.tfplan.json`, `terraform-plan.json`, `.terraform-plan.json`) render bounded resource address/type/action/reason rows and aggregate change counts. Before/after values, sensitive values, state, configuration and provider data remain omitted; plan/apply/refresh and provider/network operations are never performed.
- CycloneDX BOM JSON/XML (`bom.json`, `bom.xml`, `*.cdx.json`, `*.cdx.xml`) render bounded component type/name/version/scope rows and vulnerability/dependency/service counts. Serial numbers, refs, hashes, licenses, PURLs, properties, vulnerability details and external references remain omitted; no registry or URL is contacted.
- SPDX 2.x JSON/tag:value (`spdx.json`, `sbom.spdx.json`, `*.spdx.json`, `.spdx`, `.spdx.txt`) renders bounded package/file identity rows and relationship/annotation/snippet/external-document counts. Checksums, licenses, suppliers, PURLs, download locations, comments and external URIs remain omitted.
- JaCoCo/Cobertura coverage XML (`jacoco.xml`, `cobertura.xml`, `coverage.xml`, `.jacoco.xml`, `.cobertura.xml`, `.coverage.xml`) renders bounded package class and line/branch/method covered/missed summaries. Source paths, internals, sessions, logs, attachments and quality-gate evaluation remain omitted.
- LCOV tracefiles (`.info`, `lcov.info`, `coverage.info`, `.lcov.info`) render bounded file basenames and line/function/branch covered/missed summaries. Absolute paths, function names, execution records and source content remain omitted.
- ASAM OpenDRIVE (`.xodr`, `.opendrive`, `.opendrive.xml`, `.open-drive.xml`; content sniffing) renders bounded road reference-line `<line>` and constant-curvature `<arc>` plan-view geometry as a planar map. Local metre coordinates are normalized; spiral/poly3/paramPoly3, lanes, profiles, signals, objects, links and simulator behavior remain inert. Limits are 64 MiB input, 1,000,000 XML events, 500,000 nodes, depth 96, 100,000 roads, 200,000 geometries and 500,000 positions. Source: [ASAM OpenDRIVE](https://www.asam.net/standards/detail/opendrive/).
- ASAM OpenCRG (`.crg`, `.opencrg`; content sniffing) renders bounded clear-text section names and line counts. ASCII/binary road-surface payloads and `$ROAD_CRG_FILE` references are omitted; no tire, vehicle or surface evaluation runs. Limits are 64 MiB input, 1,000,000 lines, 1 MiB/line and 100,000 sections. Source: [ASAM OpenCRG](https://www.asam.net/standards/detail/opencrg/).
- ASAM OpenSCENARIO XML (`.xosc`, `.openscenario`, `.openscenario.xml`, `.open-scenario.xml`; content sniffing) renders bounded FileHeader, ScenarioObject, Story/Act/Maneuver/Event/Action, parameter/catalog-reference and RoadNetwork metadata. Catalogs, road files, controllers, expressions, triggers and simulator behavior remain inert. Limits are 64 MiB input, 1,000,000 XML events, 500,000 nodes, depth 96 and 200,000 rows. Source: [ASAM OpenSCENARIO XML](https://www.asam.net/standards/detail/openscenario-xml/).
- ASAM OpenLABEL 1.0 JSON (`.openlabel.json`, `.openlabel`, `.open-label.json`; content sniffing) renders bounded collection counts for objects, actions, events, contexts, relations, frames, streams, tags, ontologies, resources and coordinate systems, plus schema and nested object-data counts. Sensor payloads, coordinates, annotation values, ontology URLs and external resources remain inert. Limits are 64 MiB input, depth 100, 300,000 JSON values, 100,000 entries and 2 MiB strings. Source: [ASAM OpenLABEL](https://www.asam.net/standards/detail/openlabel/).
- OGC CityGML 2.0/3.0 (`.citygml`, `.citygml.xml`, `.citygml.gml`; content sniffing) renders bounded thematic object and LoD counts with Envelope, CRS and XLink metadata. Geometry, textures, attributes and external resources remain inert. Limits are 64 MiB input, 1,000,000 XML events, 500,000 nodes, depth 96 and 200,000 rows. Source: [OGC CityGML](https://www.ogc.org/standards/citygml/).
- OGC CityJSON 1.x/2.0 (`.cityjson`, `.city.json`, `.cityjson.json`; content sniffing) renders bounded CityObject type/geometry/LoD, vertex and boundary-index counts plus transform/metadata presence. Coordinates, semantics, materials, textures, attributes, extensions and external resources remain inert. Limits are 64 MiB input, depth 100, 300,000 JSON values, 100,000 objects, 500,000 vertices, 200,000 geometries/rows and 2 MiB strings. Source: [OGC CityJSON](https://www.ogc.org/standards/cityjson/).
- OASIS STIX 2.1 JSON (`.stix.json`, `.stix-json`, `.stix`; content sniffing) renders bounded object type/id, created/modified timestamps, label counts and relationship/reference counts. Descriptions, indicator patterns, hashes, URLs, marking content and custom properties are omitted; no TAXII/API/network operation runs. Limits are 64 MiB input, depth 100, 300,000 JSON values, 100,000 objects, 200,000 rows and 2 MiB strings. Source: [OASIS STIX 2.1](https://docs.oasis-open.org/cti/stix/v2.1/os/stix-v2.1-os.html).
- OASIS TAXII 2.1 JSON (`.taxii.json`, `.taxii-json`, `.taxii`; content sniffing) renders bounded envelope, manifest, collection, discovery, status and error IDs/counts. STIX payloads, URLs, descriptions, authorization data and TAXII endpoints are omitted; no HTTP/TAXII client runs. Limits are 64 MiB input, depth 100, 300,000 JSON values, 100,000 entries, 200,000 rows and 2 MiB strings. Source: [OASIS TAXII 2.1](https://docs.oasis-open.org/cti/taxii/v2.1/os/taxii-v2.1-os.html).
- OpenFOAM field files (`.foamfield`, `.foam-field`, or content-sniffed) render bounded class/object/location, uniform/nonuniform count, scalar/vector-magnitude min/max and boundary patch metadata. Value lists, dimensions, patch dictionaries, paths and solver operations remain inert.
- RFC 6902 JSON Patch (`.jsonpatch`, `.json-patch`, `.patch.json`) renders ordered add/remove/replace/move/copy/test operation rows with paths, from paths and value types. Values are omitted and patches are never applied.
- RFC 7396 JSON Merge Patch (`.mergepatch`, `.json-merge-patch`, `.merge-patch.json`) renders set/delete/merge path rows with value types and depth. Values are omitted and merge patches are never applied.
- CloudEvents JSON 1.0 (`.cloudevent.json`, `.cloud-event.json`, `.cloudevents.json`, `.ce.json`, `.cloudevent`, `.cloudevents`; content sniffing) renders single events and JSON batches as bounded type, id, source-host, time, subject and data type/size metadata. URI query values are masked; data/data_base64 payloads, dataschema and extension values are omitted, and no URI, broker, handler or network resource is resolved. Limits are 64 MiB input, depth 100, 300,000 JSON values, 100,000 events and 2 MiB strings. Source: [CloudEvents JSON Event Format](https://github.com/cloudevents/spec/blob/main/cloudevents/formats/json-format.md).
- HL7 FHIR R4 JSON (`.fhir.json`, `.fhirjson`, `.fhir`, `.bundle.fhir.json`, `.fhir-bundle.json`; content sniffing) renders resource objects and Bundle entries as bounded resourceType, id, status/type, profile and structural metadata. Clinical values, Narrative XHTML, names, identifiers, coded displays, extension values and references remain omitted; no terminology lookup, validation, URL fetch or clinical operation runs. Limits are 64 MiB input, depth 100, 300,000 JSON values, 100,000 resources and 2 MiB strings. Source: [FHIR R4 JSON representation](https://hl7.org/fhir/R4/json.html).
- Apache Avro JSON schema/protocol (`.avsc`, `.avpr`, `.avro.json`, `.avro-schema.json`; content sniffing) renders bounded record, field, union, enum, fixed, array, map and protocol message paths with type summaries. Defaults, docs, aliases, logical types, imports, field values, code generation and RPC execution remain inert; named references are not resolved. Limits are 64 MiB input, depth 100, 300,000 JSON values, 200,000 rows and 2 MiB strings. Source: [Apache Avro Specification](https://avro.apache.org/docs/1.12.0/specification/).
- OpenTelemetry OTLP JSON (`.otlp.json`, `.otlp-json`, `.otel.json`, `.otlp.trace.json`, `.otlp.metrics.json`, `.otlp.logs.json`; content sniffing) renders bounded trace, metric, log and profile signal/resource/scope counts, service names and event/link/data-point summaries. Attribute values, log bodies, IDs, exemplars, links, schema URLs and endpoints are omitted; no collector, exporter or network operation runs. Limits are 64 MiB input, depth 100, 300,000 JSON values, 200,000 rows and 2 MiB strings. Source: [OpenTelemetry OTLP specification](https://opentelemetry.io/docs/specs/otlp/).
- OCEL 2.0 JSON (`.jsonocel`, `.ocel.json`, `.ocel-json`; content sniffing) renders bounded event/object type definitions, event and object IDs/types/times, attribute counts and event/object relationship counts. Attribute values, qualifiers, URLs and external resources are omitted; no process discovery or filtering runs. Limits are 64 MiB input, depth 100, 300,000 JSON values, 100,000 nodes, 200,000 rows and 2 MiB strings. Source: [OCEL 2.0 JSON format](https://www.ocel-standard.org/specification/formats/json/).
- JSON:API 1.1 (`.jsonapi`, `.json-api.json`, `.jsonapi.json`; content sniffing) renders bounded primary/included resource type/id, status metadata, attribute-key counts and relationship counts. Attribute values, linkage payloads, meta/error details and link URLs are omitted; no endpoint or API operation runs. Limits are 64 MiB input, depth 100, 300,000 JSON values, 100,000 resources, 200,000 rows and 2 MiB strings. Source: [JSON:API 1.1 specification](https://jsonapi.org/format/).
- Generic XML (`.xml` fallback) displays namespace-qualified elements, attributes and text as inert rows. DTDs are rejected; external entities/resources are never loaded. Input, line, event, node, depth, path and rendered-text limits apply.
- Java Properties (`.properties`) uses ISO-8859-1 bytes, Java escapes and line continuations. Duplicate keys use the last value; variables and values are not evaluated.
- BPMN 2.0 (`.bpmn`, `.bpmn2`) draws supported process shapes and sequence flows from explicit Diagram Interchange geometry; models without DI geometry are rejected and process logic is never executed.
- DMN (`.dmn`) displays supported decision tables and local input/decision requirements; FEEL, hit-policy semantics and decision execution are not evaluated.
- CMMN 1.1 (`.cmmn`) draws case-plan items and CMMNDI connectors from explicit geometry; sentries, lifecycle rules and case execution are not evaluated.
- ReqIF (`.reqif`) renders bounded requirements, hierarchy and relations as inert tables; XHTML is flattened and external/tool-specific content is not processed.
- XMI (`.xmi`) renders bounded nested model-element tables with xmi:id/type and inert attributes; external links and model execution are not processed.
- CSV/TSV (`.csv`, `.tsv`) validates field quotes and escaped quotes, supports quoted newlines, and renders bounded 100-row × 32-column pages. Malformed quote placement fails; ragged rows, blank records, and overlong preview cells are reported. The raw source is embedded only for a single-page CSV of at most 8 MiB.
- GeoPackage (`.gpkg`) reads regular feature tables through a read-only SQLite connection and writes one map page per layer. EPSG:3857 PNG/JPEG tile layers are decoded and re-encoded as PNG images; bounded tiles from the highest usable zoom are displayed. Vector geometry supports core WKB types and EPSG:4326/4979/3857; other vector CRSs are rejected without reprojection. Attributes, feature/tile views, unsupported tile CRSs, and vector Z/M values are omitted. `docs/SUPPORT.md` lists SQLite, layer, row, tile and image safety limits.
- GeoJSON Text Sequences (`.geojsons`, `.geojsonseq`) follow RFC 8142 RS/LF framing and may contain heterogeneous GeoJSON records. `.geojsonl` is accepted as newline-delimited compatibility input. Records and coordinate totals are bounded; feature attributes and identifiers are omitted.
- JSON Text Sequences (`.jsons`, `.jsonseq`) follow RFC 7464 RS framing and render one heading per inert JSON value. `.jsonl` is accepted as newline-delimited compatibility input. Empty/malformed RS records are skipped with counted warnings, with record, input and rendered-block limits.
- TopoJSON (`.topojson`) reconstructs shared arcs, quantized/delta coordinates, and reversed arc references. It assumes WGS 84 longitude/latitude because no CRS metadata is present; other coordinate systems are not transformed. Feature properties and IDs are omitted.
- PNG/JPEG/BMP/GIF/WebP raster inputs are vectorized through grayscale thresholding and contour tracing, with limits of 20 million pixels, 100,000 pixels per side, and 500,000 vector spans. Animated GIF/WebP uses the first frame and reports a warning; partial first GIF frames are composited over transparency. CMYK JPEG is approximated without color profiles, and 16-bit lossless JPEG is reduced to 8-bit with a warning.
- CBZ (`.cbz`) emits one SVG per PNG/JPEG page image in natural filename order. ComicInfo metadata, non-PNG/JPEG image types, EXIF orientation, and color profiles are not applied; archive entry, image, total byte, and page limits apply.
- Abaqus `.inp` renders supported mesh-only decks, including meshed part/instance assemblies. It applies instance translation before axis-angle rotation, omits midside nodes, projects 3D meshes onto XY, and does not render analysis loads, materials or results. Unsupported element types and external includes are reported; see `docs/SUPPORT.md` for the supported element subset.
- Nastran `.bdf`/`.nas` renders supported GRID and structural element cards from free/small/large-field Bulk Data. Continuation rows must be adjacent to their parent. It omits midside nodes, projects 3D coordinates onto XY, rejects nonzero GRID coordinate systems, and reports external includes or recognized unsupported elements; it does not render analysis loads, materials or results.
- ANSYS Mechanical APDL `.cdb` renders blocked `NBLOCK`/`EBLOCK` mesh sections and basic unblocked `N`/`EN` cards as a bounded XY-projected wireframe. It validates fixed-width fields, IDs, connectivity and `-1` terminators; APDL commands, includes, loads, materials and solver settings remain inert.
- LS-DYNA `.k`/`.key` renders standard or comma-separated Keyword mesh cards for `*NODE`, shell, solid and beam elements. It rejects long-format `+` rows, omits midside/orientation nodes, projects 3D coordinates onto XY, and reports external includes or unsupported element keywords; it does not render analysis loads, materials or results.
- Jupyter `.ipynb` displays nbformat 4 Markdown, code, stored text/HTML/JSON/errors, and PNG/JPEG output cells. It never runs code, skips active/interactive/SVG MIME outputs and attachment images, and applies strict cell/text/image limits.
- OFF `.off` renders ASCII polygon meshes with the shaded 3D renderer; optional colors/normals are ignored with a warning, and binary/4D variants are unsupported.
- SU2 `.su2` renders bounded ASCII/UTF-8 2D and 3D unstructured meshes, including common linear volume types and named boundary connectivity. 3D volume cells become XY-projected wireframe edges; marker edges are highlighted orange, while marker names and solver settings are reported but not rendered. High-order cells are omitted and no solver runs.
- OpenFOAM `.foam` reads ASCII `constant/polyMesh` files and bounded gzip-compressed ASCII `.gz` sidecars next to a case marker, confines canonicalized sidecars to the case root, and renders mesh face edges as an isometric wireframe while highlighting boundary patch edges. Binary mesh payloads, time folders, fields and solver settings are omitted; directives are not evaluated.
- Tecplot ASCII `.dat`/`.tec`/`.tecplot`/`.tp` renders bounded POINT/BLOCK finite-element zones (triangle, quad, tetrahedron, brick) and ordered I/J grids using the shared CAE mesh view. X/Y coordinates are required; an optional numeric variable is color-mapped inertly. Zone metadata and advanced features are omitted with warnings; no solver or macro is executed.
- EnSight Gold ASCII `.case`/`.geo` follows one case-local geometry sidecar after canonical path validation and renders bounded parts with coordinates and common linear element blocks. Binary cases, variable files, external paths, and unsupported `nsided`/`nfaced` blocks are rejected or warned; no solver runs.
- PLOT3D formatted ASCII `.p3d`/`.plot3d`/`.p3` renders bounded single- and multi-block structured X/Y(/Z) grids as quadrilateral cells. 3D emits boundary surfaces; unformatted Fortran records, IBLANK masks, solution `.q`, and solver metadata are omitted or warned.
- Netpbm `.pbm`/`.pgm`/`.ppm`/`.pnm`/`.pam` supports bounded ASCII/raw PBM/PGM/PPM and PAM grayscale/RGB/alpha samples through the raster contour path; dimensions and payloads are validated before allocation.
- VRML97 `.wrl`/`.vrml` extracts only Coordinate point arrays and IndexedFaceSet/IndexedLineSet indices into the shaded 3D renderer. Texture coordinates, transforms, appearances, scripts, routes, and external URLs are ignored; no active content executes.
- IFC-SPF `.ifc`, buildingSMART IFCXML `.ifcxml` and single-root-model IFCZIP `.ifczip` archives render supported IFC4 triangulated and planar polygon face sets plus extruded rectangle, circle and closed-2D-polyline area profiles. They apply product/local placements and reuse geometry through nested `IfcMappedItem`/`IfcRepresentationMap` references. Mapped geometry supports 3D Cartesian transforms with uniform positive scale, rotation, mirroring and translation; nonuniform/2D operators warn and are omitted. Circles use a 64-segment mesh approximation; concave profiles up to 256 vertices use bounded triangulation. IFCXML internal IDs/references are resolved inside the document; DTDs and external URIs are never loaded. B-rep/CSG, tapered/hollow/rounded and other unsupported swept profiles, grid placements, self-intersecting/non-planar faces, polygon holes, materials, properties, units and georeferencing remain omitted; unsupported geometry is reported. IFCZIP sidecar files are not extracted or loaded.
- Flat OPC `.flatopc`/`.fopc`/`.flatopc.xml` validates the Office XML package namespace and part names, reconstructs XML/base64 parts into an in-memory package, and delegates to the existing DOCX/XLSX/PPTX renderers. Macros, external relationships, URLs, active content and filesystem extraction remain inert. Bounds are 128 MiB input, 128 MiB cumulative expanded parts, 100,000 parts, 16 MiB/part and 500,000 XML events.
- AASX `.aasx` follows the bounded OPC root/origin relationship chain to AAS XML/JSON specification parts, then renders shell/submodel/concept/element and supplementary-file/thumbnail counts. CAD/manual payloads, identifiers, values, URLs, signatures and encryption material remain inert. Bounds are 128 MiB input and cumulative expanded metadata, 100,000 entries, 16 MiB/part, 500,000 XML events, 300,000 XML nodes and JSON depth/value limits.
- OpenSCAD `.scad` is scanned as inert CAD source. Module/function definitions, primitive solids, transforms, booleans, assignments and import/use/include/surface references are counted; geometry, expressions, loops, libraries and external paths never execute. Bounds are 128 MiB input, 2,000,000 lines, 1 MiB/line and 100,000 rows.
- AMF `.amf` parses bounded ISO/ASTM 52915 object/mesh vertices and volume triangles into the existing shaded OBJ renderer. Units remain metadata; materials, textures, color, lattice, slices, metadata payloads and external references remain inert. Bounds are 128 MiB input, 500,000 XML events, 300,000 nodes, 2,000,000 vertices and 200,000 triangles.
- PLMXML `.plmxml`/`.plm.xml` summarizes bounded Siemens product definitions, parts, assembly structures, instances, representations, construction geometry and external-reference counts. Referenced XT/Parasolid geometry, IDs, URLs and external files remain inert. Bounds are 128 MiB input, 1,000,000 XML events, 500,000 nodes, depth 128 and 200,000 rows.
- STEP-XML `.stepxml`/`.stpx`/`.step.xml` recognizes ISO 10303-28/AP242 XML roots and summarizes product, assembly, representation, geometry and property counts. EXPRESS/schema evaluation, external CAD geometry, IDs and URLs remain inert. Bounds are 128 MiB input, 1,000,000 XML events, 500,000 nodes, depth 128 and 200,000 rows.
- QIF `.qif`/`.qif.xml` summarizes bounded Quality Information Framework product, inspection-plan/result, feature, characteristic, datum, traceability and external-file-reference counts. Measured values, tolerances, IDs, URLs and external CAD/inspection files remain inert; no schema or resource is fetched. Bounds are 128 MiB input, 1,000,000 XML events, 500,000 nodes, depth 128 and 200,000 rows.
- B2MML `.b2mml`/`.b2mml.xml` summarizes ISA-95 manufacturing schedule/performance/request/response, product/material/equipment/personnel/process/capability/maintenance/transaction and external-reference counts. Operations, values, credentials, URLs and external resources remain inert; no production action runs. Bounds are 128 MiB input, 1,000,000 XML events, 500,000 nodes, depth 128 and 200,000 rows.
- JDF/JMF/XJDF `.jdf`/`.jdf.xml`/`.jmf`/`.xjdf` summarizes CIP4 job nodes, resources, processes, products, devices, media, layouts, run lists, audits and file/URL links. Device commands, workflow execution, credentials, URLs and linked files remain inert. Bounds are 128 MiB input, 1,000,000 XML events, 500,000 nodes, depth 128 and 200,000 rows.
- TMX `.tmx`/`.tmx.xml` summarizes Translation Memory eXchange version, translation units, variants, segments, notes, properties and language tags. Segment text, IDs, DTDs, skeleton files, URLs and external resources remain inert. Bounds are 128 MiB input, 1,000,000 XML events, 500,000 nodes, depth 128, 10,000 languages and 200,000 rows.
- TBX/MARTIF `.tbx`/`.tbx.xml` summarizes ISO 30042 terminology entries, terms, language sets, descriptions, administrative/transaction metadata, notes and references. Terms, definitions, IDs, URLs, DTD/XCS/Schematron resources and proprietary values remain inert. Bounds are 128 MiB input, 1,000,000 XML events, 500,000 nodes, depth 128, 10,000 languages and 200,000 rows.
- gbXML `.gbxml`/`.gbxml.xml` summarizes bounded Campus, Building, Space, Zone, Surface, Opening, Construction, Material, Schedule, system and occupant structure for BIM/energy-model review. Coordinates, geometry, schedules, formulas, IDs, URLs and weather/material resources remain inert. Bounds are 128 MiB input, 1,000,000 XML events, 500,000 nodes, depth 128 and 200,000 rows.
- FHIR XML `.fhir.xml`/`.fhirxml` summarizes HL7 resource types and Bundle entries, contained/narrative/extension counts. Clinical values, identifiers, narrative XHTML, references, profiles and terminology services remain inert. Bounds are 64 MiB input, 1,000,000 XML events, 500,000 nodes, depth 128, 100,000 resources and 100,000 rows.
- IDML `.idml` follows `designmap.xml` and bounded Stories, Spreads, MasterSpreads and Resources XML parts in memory, rendering package/layout/story/resource counts. IDs, story text, image/font payloads, hyperlinks and external resources remain inert. Bounds are 256 MiB input/expanded XML, 100,000 entries, 32 MiB/entry, 20,000 XML parts, 500,000 XML events, 300,000 nodes, depth 128 and 200,000 rows.
- XPDL `.xpdl`/`.xpdl.xml` summarizes workflow processes, activities, transitions, participants, applications, data fields, pools/lanes and external references. IDs, expressions, scripts, application parameters, URLs and external packages remain inert. Bounds are 128 MiB input, 1,000,000 XML events, 500,000 nodes, depth 128 and 200,000 rows.
- ONIX `.onix`/`.onix.xml`/`.onix3` summarizes ONIX for Books release, products, identifiers, descriptive/collateral detail, publishing status, supply, contributors, languages, subjects, measures, prices, text and resources. ISBNs, titles, prices, descriptions, URLs, codelists and commercial values remain inert. Bounds are 128 MiB input, 1,000,000 XML events, 500,000 nodes, depth 128 and 200,000 rows.
- OAI-PMH `.oaipmh`/`.oai-pmh`/`.oai.xml` summarizes response verbs, records, headers, metadata, sets, metadata formats, errors and resumption tokens. Identifiers, URLs, metadata values and token contents remain inert; HTTP harvesting and paging never run. Bounds are 128 MiB input, 1,000,000 XML events, 500,000 nodes, depth 128 and 200,000 rows.
- CDA `.cda`/`.cda.xml`/`.ccd.xml` summarizes HL7 ClinicalDocument sections, entries, observations, acts, encounters, procedures, organizers, authors, participants, narrative and template nodes. PHI, identifiers, narrative XHTML, coded values, references and external documents remain inert; this is not de-identification. Bounds are 128 MiB input, 1,000,000 XML events, 500,000 nodes, depth 128 and 200,000 rows.
- ISO 20022 `.iso20022.xml`/`.pain.xml`/`.pacs.xml`/`.camt.xml` summarizes financial message, payment, transaction, party, account, amount, date and remittance structure. Account numbers, amounts, names, identifiers, URLs and payment operations remain inert. Bounds are 128 MiB input, 1,000,000 XML events, 500,000 nodes, depth 128 and 200,000 rows.
- SBML `.sbml`/`.sbml.xml` summarizes level/version, model, compartment, species, reaction, parameter, rule, event, unit, function and annotation counts. Values, IDs, MathML equations, package resources and simulations remain inert. Bounds are 128 MiB input, 1,000,000 XML events, 500,000 nodes, depth 128 and 200,000 rows.
- CellML `.cellml`/`.cellml.xml` summarizes components, variables, units, connections/maps, imports, encapsulation, resets, MathML and annotations. Values, equations, IDs, imported models and simulations remain inert. Bounds are 128 MiB input, 1,000,000 XML events, 500,000 nodes, depth 128 and 200,000 rows.
- OCEL XML `.xmlocel`/`.ocel.xml` summarizes event-types, events, object-types, objects, attributes, relationships and attribute types. IDs, timestamps, values and process-mining operations remain inert. Bounds are 128 MiB input, 1,000,000 XML events, 500,000 nodes, depth 128 and 200,000 rows.
- EnergyPlus IDF `.idf`/`.energyplus.idf` parses bounded object records and renders object-type/object/field counts. Field values, schedules, formulas, paths, IDD lookups, macros, weather references and simulations remain inert. Bounds are 128 MiB input, 2,000,000 lines, 1 MiB/line, 200,000 objects, 2,000,000 fields and 200,000 rows.
- EnergyPlus EPW `.epw`/`.energyplus.epw` summarizes the eight header rows and hourly-column structure. Location, timestamps, temperatures, radiation, wind, station data, weather conversion and simulation remain inert. Bounds are 128 MiB input, 2,000,000 lines, 1 MiB/line, 100 columns, 2,000,000 hourly rows and 200,000 rows.
- RINEX `.rnx`/`.rinex`/`.obs`/`.nav`/`.gnav` validates bounded GNSS headers and counts observation types, epochs, satellite rows and navigation records. Station names, coordinates, timestamps, measurements and geodetic processing remain inert. Bounds are 256 MiB input, 5,000,000 lines, 1 MiB/line, 2,000,000 epochs, 20,000,000 satellite rows and 200,000 rows.
- ACIS SAT `.sat` counts bounded ASCII body/solid/lump/shell/face/loop/coedge/edge/vertex/surface/transform entities. NURBS geometry, topology, attributes, binary SAB, tessellation and Boolean operations remain inert. Bounds are 256 MiB input, 2,000,000 lines, 1 MiB/line, 500,000 entities and 200,000 rows.
- SED-ML `.sedml`/`.sedml.xml`/`.sed-ml.xml` summarizes models, simulations, tasks, data generators, outputs, changes, ranges, variables and algorithms. Model paths, algorithm URIs, MathML, XPath changes and output data remain inert; no simulation engine runs. Bounds are 128 MiB input, 1,000,000 XML events, 500,000 nodes, depth 128 and 200,000 rows.
- SBGN-ML `.sbgn`/`.sbgnml`/`.sbgn.xml` summarizes biological map glyphs, arcs, labels, ports, boxes, clone markers, states, terminals, callouts and submaps. Coordinates, IDs, semantics, layout engines and external resources remain inert. Bounds are 128 MiB input, 1,000,000 XML events, 500,000 nodes, depth 128 and 200,000 rows.
- COMBINE/OMEX `.omex`/`.omex.zip`/`.combine` requires a bounded manifest and summarizes archive contents and SBML/CellML/SED-ML/metadata formats. Members, URLs and model payloads remain inert; no extraction or simulation runs. Bounds are 256 MiB input/expanded metadata, 100,000 entries, 32 MiB/entry, 500,000 XML events, 300,000 nodes and 200,000 rows.
- XDMF `.xdmf`/`.xmf` summarizes XML domain/grid/topology/geometry/attribute/DataItem/time/reference/function structure. HDF5/Binary arrays, coordinates, expressions and external paths remain inert. Bounds are 128 MiB input, 1,000,000 XML events, 500,000 nodes, depth 128 and 200,000 rows.
- VTK PVD `.pvd` summarizes Collection/DataSet timestep/group/part/file structure. Referenced VTK sidecars and URLs remain inert. Bounds are 128 MiB input, 1,000,000 XML events, 500,000 nodes, depth 128 and 200,000 rows.
- FDS `.fds` scans Fire Dynamics Simulator namelist block types as inert text. CHID, paths, coordinates, devices, meshes, solver settings and CFD execution remain inert. Bounds are 128 MiB input, 2,000,000 lines, 1 MiB/line, 500,000 blocks and 200,000 rows.
- AbiWord AWML `.abw` summarizes bounded section/paragraph/character/table/image/bookmark/hyperlink/field/equation structure. Paragraph text, styles, links, fields, embedded objects and external resources remain inert. Bounds are 128 MiB input, 1,000,000 XML events, 500,000 nodes, depth 128 and 200,000 rows.
- NeuroML `.nml`/`.neuroml` summarizes neuroscience cells, morphologies, segments, networks, populations, projections, connections, synapses, inputs, channels and includes. Parameters, coordinates, equations, LEMS definitions and imported models remain inert. Bounds are 128 MiB input, 1,000,000 XML events, 500,000 nodes, depth 128 and 200,000 rows.
- BioPAX `.biopax`/`.biopax.xml` validates BioPAX RDF/XML and summarizes pathway, interaction, physical-entity, protein, small-molecule, complex, reaction, control, cross-reference and ontology-import counts. RDF IDs, links, OWL imports and inference remain inert. Bounds are 128 MiB input, 1,000,000 XML events, 500,000 nodes, depth 128 and 200,000 rows.
- XSD `.xsd`/`.xsd.xml`/`.schema.xsd` summarizes W3C XML Schema declarations, types, groups, compositors, derivations and include/import/redefine/override dependencies. Values, locations, dependencies and instance validation remain inert. Bounds are 128 MiB input, 1,000,000 XML events, 500,000 nodes, depth 128 and 200,000 rows.
- XSLT `.xsl`/`.xslt`/`.xsl.xml` summarizes stylesheet templates, apply/call-template, variables/params, loops, conditions, keys, imports/includes, outputs, scripts and functions. XPath, document access, extension functions and transformations remain inert. Bounds are 128 MiB input, 1,000,000 XML events, 500,000 nodes, depth 128 and 200,000 rows.
- XSL-FO `.fo`/`.xslfo`/`.fo.xml` summarizes layout masters, page sequences, flows, regions, blocks/inlines, tables, graphics, links, bookmarks, page numbers, lists and footnotes. Properties, coordinates, external graphics, links and FO/PDF formatting remain inert. Bounds are 128 MiB input, 1,000,000 XML events, 500,000 nodes, depth 128 and 200,000 rows.
- XProc `.xpl`/`.xproc`/`.xproc.xml` summarizes XML pipeline declarations, steps, ports, options, variables, pipes, control groups and file/HTTP operations. Pipeline execution, XPath, network calls and external imports remain inert. Bounds are 128 MiB input, 1,000,000 XML events, 500,000 nodes, depth 128 and 200,000 rows.
- WADL `.wadl`/`.wadl.xml` summarizes REST resources, methods, requests, responses, representations, parameters, grammars and links. Endpoint URLs, schemas, credentials and HTTP calls remain inert. Bounds are 128 MiB input, 1,000,000 XML events, 500,000 nodes, depth 128 and 200,000 rows.
- OpenSearch `.osdd`/`.opensearch` summarizes descriptor URLs, queries, languages, encodings, images and rights. URL templates, search requests and network resources remain inert. Bounds are 64 MiB input, 500,000 XML events, 300,000 nodes, depth 96 and 100,000 rows.
- SAML `.saml`/`.saml.xml` summarizes IdP/SP descriptors, endpoints, keys, certificates, attributes, organizations, contacts and signatures. Entity IDs, URLs, certificates and authentication remain inert. Bounds are 128 MiB input, 1,000,000 XML events, 500,000 nodes, depth 128 and 200,000 rows.
- XACML `.xacml`/`.xacml.xml` summarizes Policy/PolicySet rules, targets, conditions, matches, attributes, obligations, advice, references and functions. Decision evaluation, policy combining and external references remain inert. Bounds are 128 MiB input, 1,000,000 XML events, 500,000 nodes, depth 128 and 200,000 rows.
- BCFZIP `.bcfzip` renders buildingSMART BIM Collaboration Format package metadata from `bcf.version`, project information and `markup.bcf` topic title/status/priority plus comment, viewpoint, document-reference and component counts. Snapshot images, IFC/model payloads, document URLs, GUID payloads, extensions and collaboration actions remain inert; no ZIP extraction, URI dereference, network operation or issue mutation runs. The archive and markup XML reader is bounded (128 MiB compressed input, 128 MiB cumulative expanded metadata, 100,000 entries, 16 MiB/entry, 500,000 XML events, 300,000 nodes, depth 96, 100,000 rows).
- 3MF `.3mf` follows build-item selection and expands bounded component hierarchies with their transforms, applying build transforms and converting declared units to millimeters. Unsupported required extensions are rejected and recommended extensions are reported. It previews triangle surfaces without material colors or boolean union of overlapping solids; packages without a build section use a warned top-level-object compatibility fallback.
- Visio `.vsdx`/`.vsdm`/`.vstx`/`.vstm` and legacy XML `.vdx` render page order, direct shape geometry/styles, text, and straight connector endpoints. Master inheritance, groups, arrowheads, curved connector routing, and embedded foreign objects are omitted or approximated with warnings; external relationships are not fetched and macros are never run.
- EML `.eml` displays decoded common headers and the first safe HTML or plain-text body. Bounded PNG/JPEG Content-ID parts are embedded; exact Content-Location matches are accepted within the same or an enclosing `multipart/related` tree. CSS/layout is approximated, other attachments are omitted, and external resources are not fetched.
- Outlook `.msg` reads common subject, sender/recipient, and safe HTML or plain-text body properties from the bounded CFB container. Scripts, remote images, transport headers, and attachment payloads are omitted; attachments are not extracted.
- MBOX `.mbox` previews each RFC 4155 From_ separated message as sequential SVG pages, with the same text, attachment, and external-resource limits as EML.
- MHTML `.mht`/`.mhtml` honors the `multipart/related` `start` root (or its first part if omitted) and displays its HTML in the safe subset. Bounded PNG/JPEG parts referenced by Content-ID or URI-resolved Content-Location within the same or an enclosing related tree can be embedded. Relative URIs use HTML `<base href>`, MIME Content-Base/Content-Location, then the `thismessage:/` fallback; unmatched resources, CSS, scripts, and other attachments are omitted without external fetches.
- iCalendar `.ics` displays events, tasks, journal, and free/busy components sequentially. Recurrence rules are shown without expansion, time-zone rules are not applied, alarms and attachments are omitted, and URLs are never fetched.
- vCalendar `.vcs` reads version 1.0 VEVENT/VTODO records through the bounded calendar renderer. Legacy reminders and unknown properties are warned and omitted; alarms are not executed or external resources fetched.
- vCard `.vcf`/`.vcard` displays version 2.1/3.0/4.0 contact cards one per page; vCard 2.1 CHARSET and quoted-printable values are decoded. Photos, keys, sound, and other media are omitted, and URI resources are never fetched.
- Quarto `.qmd` and R Markdown `.Rmd`/`.rmarkdown` show Markdown and fenced code chunks as source without executing them. Only simple title/author/date front matter is shown; output generation, filters, cross-references, and includes are not processed.
- MEDIT `.mesh`/`.medit` renders ASCII versions 1–5; `.meshb` renders binary versions 1–4 in either byte order, with bounded versioned keyword offsets and record widths. Linear geometry is drawn, while high-order and solution sections are skipped with a warning; 3D is projected onto XY.
- VTK Legacy `.vtk` accepts ASCII and fixed-width big-endian binary UnstructuredGrid/PolyData. VTK XML `.vtu`/`.vtp`/`.vti`/`.vtr`/`.vts` accepts inline ASCII, base64 inline binary, base64 appended arrays, and raw appended binary arrays, including `vtkZLibDataCompressor`; structured extents, ImageData Origin/Spacing/Direction, rectilinear coordinates, and explicit StructuredGrid points are honored. Raw appended payloads are capped at 192 MiB. Other compressors and parallel `.pvtu`/`.pvtp`/`.pvti`/`.pvtr`/`.pvts` packages are rejected explicitly. Gmsh supports ASCII MSH 2.x/4.0/4.1 and both byte orders of binary MSH 2.2/4.0/4.1; 4.0's mixed node records and mandatory Entities section are parsed, while partitioned sections remain unsupported.
- Preserve source files. The runner refuses non-empty output directories to avoid mixing stale and new pages.
- Reverse conversion refuses to overwrite an existing output file.
- Do not expose internal PDF/OOXML parser modules for ordinary use; the `docsvg` CLI is the supported entrypoint.
