ryusui-hiro/document-svg/docs/FORMATS.ja.md

# 対応形式の詳細

`document-svg` が読み書きできる形式の、技術的な完全リストです。形式ごとの再現度の注意も載せています。
検索できて、ふつうの言葉で書いた一覧は、[プロジェクトサイトの対応形式ページ](https://ryusui-hiro.github.io/document-svg/ja/formats.html)を見てください。
同じ内容は [formats.json](https://ryusui-hiro.github.io/document-svg/assets/data/formats.json) としても公開しています。

## 変換特性マップ

本リポジトリでは、SVG を中心ハブとした変換を以下の 3 つの変換特性（再現性・忠実度モデル）に分類しています。

- **A. 決定論的に変換できる**: フォーマット仕様や数式に基づく 1:1 の幾何・構文変換、または埋め込みメタデータからの完全可逆復元。
- **B. 画像解析・ベクトレースが必要**: ラスター画像のピクセルから輪郭追跡（Marching Squares）によりベクターパスを抽出。
- **C. 意味を推定・再構成する必要がある**: メタデータを含まない生の幾何情報（線分・テキスト座標群）から、表の行・列やグラフの接続関係を空間配置ヒューリスティクスで逆再構成。

| 分類 | 拡張子 | 順方向 (To SVG) | 逆方向 (From SVG) | 動作仕様・再現性の補足 |
|---|---|:---:|:---:|---|
| **Office / 文書** | `.pdf` | **A** | **A** | PDFベクター描画とannotation appearanceを描画。appearanceの無いFreeText/Text/Choice Widgetはbounded text fallbackを生成し、checkbox/radio Widgetは簡易state markerを描画、password valueはmaskします。単純なgrayscale/RGB/CalGray/CalRGBのJPX imageはdimension/precisionを事前検査してPNGへdecodeし、`SMaskInData=1`のembedded alpha、`SMaskInData=2`のDeviceGray/DeviceRGB/CalGray/CalRGB対応Matte unblending、制限内の単純な外部grayscale soft maskを保持します。explicit mask、未対応のMatte/color spaceやJPX機能はwarning付きでJPEG 2000 dataを残すため、PDF mask effectが失われる場合があります（layoutは近似）。`--outline-embedded-pdf-text`で文字アウトライン化可能。<br>逆変換: SVGページを正確なMediaBox寸法の複数ページPDF文書としてパッケージング。 |
| | `.pptx`, `.docx`, `.xlsx` | **A** | **A** / **C** | Word/Excel/PowerPointのOffice Open XML TransitionalとISO/IEC 29500 Strict namespaceを読み込みます。順: スライド・ページ・シートの組版描画。<br>逆: SVGベクター画像（PNGフォールバック付）としてOOXML埋め込み(**A**)。編集可能図形への逆分解は**C**。 |
| | `.flatopc`, `.fopc`, `.flatopc.xml` または内容判定されたFlat OPC | **A** | - | Microsoft Flat OPCの単一XML Office packageを検証し、boundedなDOCX/XLSX/PPTX partへメモリ内で再構成して既存Office engineで描画します。XML/base64 partはmemory package内に閉じ、macro、外部relationship、URL、active content、filesystem extractionは不活性です。上限: 入力128 MiB、展開part合計128 MiB、part 100,000、part 16 MiB、XML event 500,000。出典: [Microsoft Flat OPC API](https://learn.microsoft.com/en-us/dotnet/api/documentformat.openxml.packaging.wordprocessingdocument.fromflatopcdocument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)。 |
| | `.aasx` または内容判定されたAASX | **A** | - | Asset Administration ShellのOPC package。boundedなroot/origin relationshipからAAS XML/JSON specification partを探し、shell/submodel/concept/element countとsupplementary file/thumbnail countを表示します。identifier、value、URL、CAD/manual payload、signature、encryption materialは不活性です。上限: 入力・展開metadata合計128 MiB、entry 100,000、part 16 MiB、XML event 500,000、node 300,000。出典: [IDTA AASX Part 5](https://industrialdigitaltwin.io/aas-specifications/IDTA-01005/v3.1/index.html)。 |
| | `.xml`（Microsoft Project namespace）、`.mspdi` | **A** | - | Microsoft Project XML interchangeから、task hierarchy、指定されたStart/Finish、進捗bar、milestone、簡易predecessor arrowをboundedなGantt previewへ変換。root namespaceが一致するXMLだけを自動判定し、`.mspdi`はalias。calendar/work time、dependency type/lag、resource、schedule再計算は未対応。上限: 64 MiB、1,000,000 XML event、100,000 task、500,000 predecessor link、1 pageあたり25 task。 |
| | `.doc`, `.dot` | **C** | - | Legacy Word Binary（Word 97–2007 subset）のmain story textをbounded A4 pageへflow組版。piece tableとsimple contiguous textを読み、UTF-16/common code pageをdecodeします。tableはcell separator付きtextへflatten。page layout、style、image、header、footnote、comment、OLE objectは復元せず、暗号化文書は拒否、macroは実行しません。`.dot`はCFB Word templateの場合だけWord扱いし、Graphviz text `.dot`との衝突を避けます。 |
| | `.ppt` | **C** | - | Legacy PowerPoint Binary（97–2003）のlive edit/persist directoryをたどり、スライド順にOfficeArt textboxとplaceholder textを抽出してA4へ組版します。スライドgeometry、style、image、背景、chart、table、mediaは省略。暗号化presentationは拒否し、macroや外部contentは開きません。 |
| | `.xls` | **A** | - | 旧形式BIFF Excel workbookのcached cell valueを上限付きsheet pageとして描画します。hidden/very-hidden sheetを含みます。式の再計算、cell style、結合geometry、chart、drawingは再現せず、macroは実行しません。 |
| | `.xlsb` | **A** | - | Excel Binary Workbookの値をZIP partとBIFF12 recordの検証後に上限付きworksheet pageとして描画します。hidden worksheetを含みます。cached valueを使い、式の再計算、macro実行、style・chart・drawingの再現はせず、macro sheet形式は未対応です。 |
| | `.slk` | **A** | - | SYLK（Symbolic Link）spreadsheet。cell座標とcached valueを上限付き表ページとして表示し、formulaは不活性annotationとして表示します。format/metadata recordは無視し、macroや式の評価はしません。 |
| | `.dif` | **A** | - | DIF（Data Interchange Format）spreadsheet。TABLE/VECTORS/TUPLES/DATA headerとBOT/EOD tuple、numeric/string/status cellを上限付き表として表示します。formula・metadata・外部実行は不活性で、宣言された行列数だけで無制限にallocationしません。 |
| | `.fa`, `.fasta`, `.fna`, `.faa` | **A** | - | FASTA sequence record。definition line、sequence長、GC比率、曖昧base数、上限付きsequence previewを不活性表として表示します。IDをpathとして解決せず、alignmentは実行しません。 |
| | `.fq`, `.fastq` | **A** | - | FASTQ sequenceとper-base quality。sequence/quality長とprintable quality byteを検証し、Phred encodingを推定せず品質ASCII範囲と上限付きpreviewを表示します。解析は実行しません。 |
| | `.gff`, `.gff3` | **A** | - | GFF3の9列genome feature annotation。seqid、source/type、1-based座標、score/strand/phase、attributeを不活性表で表示し、directiveと埋め込み`##FASTA`は省略します。 |
| | `.gtf` | **A** | - | GTFの9列gene/transcript annotationとquoted attribute。座標とattributeを不活性表で表示し、hierarchy、sequence解析、外部link、実行は行いません。 |
| | `.bed` | **A** | - | UCSC BED3–BED12 genomic interval。0-based half-open座標、score/strand/thick/itemRgb、BED12 block listを不活性表で表示し、track/browser directiveとreference genome lookupは省略します。 |
| | `.bedgraph`, `.bg` | **A** | - | UCSC bedGraphの4列continuous value。0-based half-open intervalとfinite data valueを上限付き表で表示し、track directiveとremote trackは読みません。 |
| | `.vcf` | **A** | - | Variant Call Format v4.x。8つの固定variant列、任意のFORMAT/sample列、metadata、symbolic alleleを不活性表で表示します。`##reference` URL、genotype解釈、phasing、埋め込みFASTAは解決・実行せず、vCard `.vcf`とは内容判定で区別します。 |
| | `.sam` | **A** | - | SAM text alignment。header、11 mandatory alignment column、CIGAR、SEQ/QUAL length、optional tagを不活性表で表示します。reference genome、CIGAR projection、genotype解釈、外部resourceは読みません。 |
| | `.wig`, `.wiggle` | **A** | - | UCSC Wiggle continuous signal。fixedStep/variableStep declarationを1-based fully-closed区間へ展開し、finite valueを上限付き表で表示します。track/browser directiveとremote trackは読みません。 |
| | `.maf` | **A** | - | UCSC Multiple Alignment Format。`a` blockと`s` sequence rowを座標、strand、size、score、上限付きsequence preview付きで表示し、`i/e/q`等のoptional metadataは不活性です。 |
| | `.nwk`, `.newick`, `.tree` | **A** | - | Newick系統樹。括弧/カンマのtopology、quoted label、branch length、bounded commentを有向graphとして表示します。最初のtreeだけをpreviewし、taxonomyやsequence lookupは行いません。 |
| | `.sto`, `.stockholm` | **A** | - | Stockholm 1.0 multiple-sequence alignment。分割されたsequence rowと`#=GF`/`#=GS`/`#=GC`/`#=GR` annotationを上限付き不活性表で表示し、profile/sequence databaseは読みません。 |
| | `.aln`, `.clustal`, `.clustalw` | **A** | - | CLUSTAL block alignment。sequence fragment、任意のresidue count、consensus rowを検証して不活性表で表示し、alignment計算や外部lookupは行いません。 |
| | `.nex`, `.nexus` | **A** | - | NEXUS系統樹block。最初の`TREE`/`UTREE`をbounded Newick graph parserで表示し、TAXAとTRANSLATE metadataは不活性です。 |
| | `.gb`, `.gbk`, `.genbank` | **A** | - | GenBank flat-file record。LOCUS、DEFINITION、ACCESSION、feature件数、上限付きORIGIN sequence previewを不活性表で表示し、accessionやfeature locationは解決しません。 |
| | `.embl`, `.emb` | **A** | - | EMBL-Bank flat-file record。ID、AC、DE、FT feature件数、SQ sequence previewを不活性表で表示し、cross-referenceやfeature locationは解決しません。 |
| | `.dat`, `.uniprot`, `.swissprot` | **A** | - | UniProtKB/Swiss-Prot protein flat file。entry/review status、accession、protein/gene/organism metadata、feature件数、SQ sequence previewを不活性表で表示し、cross-reference linkは追跡しません。 |
| | `.ris` | **A** | - | RIS citation record。`TY`/`ER`、title、author、date、journal、page、DOI、URL、keyword、abstractを不活性bibliography rowで表示し、DOI/URL linkは取得しません。 |
| | `.csl.json`, `.csl-json`, `.cite.json` または内容判定されたCSL-JSON | **A** | - | Citation Style Language JSONのbibliography itemをID、type、title、author/editor、出版年、DOI/URL有無として表示。style/locale、abstract、DOI/URL解決、外部resourceは不活性で、値は実行しません。出典: [CSL-JSON schema](https://github.com/citation-style-language/schema)。 |
| | `.cir`, `.sp`, `.spice`, `.ckt`, `.net` | **A** | - | SPICE/ngspice circuit netlist。element card、node name、value、source lineを不活性表で表示し、dot command、`.include` path、simulation controlは実行しません。 |
| | `.xlsm`, `.xltx`, `.xltm`<br>`.docm`, `.dotx`, `.dotm`<br>`.pptm`, `.potx`, `.potm`, `.ppsx` | **A** | **A** / **C** | マクロ有効・テンプレート・スライドショー等の拡張Office形式（それぞれのOOXMLエンジンへマッピング）。 |
| | `.rtf` | **A** | - | RTF Unicode escape・ANSI文字・段落・明示的ページ区切りと、上限付きの埋め込みPNG/JPEG画像に対応。指定されたgoal寸法は反映し、画像アンカー・crop・回り込みは近似。他形式・objectはwarning付きで省略。 |
| | `.eml` | **A** | - | RFC 5322/MIMEメール。代表headerと最初のsafe HTMLまたはplain-text本文を表示し、RFC 3676 `format=flowed`本文は段落へ結合します。Content-ID参照のPNG/JPEGを上限内で埋め込み、同じまたは外側の`multipart/related`内ではContent-Locationのexact matchも扱います。CSS/layoutは近似し、ほかのattachmentは省略、外部resourceは取得しません。 |
| | `.emlx` | **A** | - | Apple Mailの単独message wrapper。先頭のdecimal byte countでRFC 5322/MIME本文を限定して表示し、後置plist metadataは解析せずwarning付きで省略。 |
| | `.msg` | **A** | - | Outlook CFB message。Subject・sender/recipientとsafe HTMLまたはplain-text bodyを表示。script・remote image URL・transport header・attachment payloadは省略し、attachmentを展開しません。 |
| | `.mbox` | **A** | - | RFC 4155 mailbox。`From_` separatorで区切られたメールを順番にSVG pageへ変換し、`.eml`と同じheader/body処理・attachment制限を適用します。 |
| | `.ics` | **A** | - | RFC 5545 iCalendar。VEVENT/VTODO/VJOURNAL/VFREEBUSYごとにページを作成し、folded lineとtext escapeを復号。recurrence/timezone ruleは展開・変換しません。 |
| | `.vcs` | **A** | - | 旧vCalendar 1.0のVEVENT/VTODOをページ化。共通calendar rendererを再利用し、未対応alarm/propertyはwarningして省略。 |
| | `.vcf`, `.vcard` | **A** | - | vCard 2.1/3.0/4.0 contact card。名前・会社・電話・email・住所・note・URLをカードごとに組版。2.1のquoted-printableとCHARSET parameterをdecode。画像/鍵などのmediaは省略して外部resourceは取得しません。 |
| | `.mht`, `.mhtml` | **A** | - | `multipart/related`の`start` root（省略時は先頭part）のHTMLをsafe HTML subsetで組版。同じまたは外側のrelated構造内でContent-IDまたはURI解決したContent-Locationに一致する上限付きPNG/JPEGを埋め込みます。`src`がないimgは`srcset`の最初の候補を使います。HTMLの`<base href>`、MIME Content-Base/Content-Location、および`thismessage:/` fallbackで相対URIを解決します。CSS・script・未一致resource・その他attachmentは省略し、外部取得はしません。 |
| | `.xps`, `.oxps`, `.dwfx` | **A** | - | OPC固定ページ文書とAutodesk DWFx（XPS互換）package。文書/ページ順、単色ベクターパス、Canvas変換・透明度、Unicode Glyphs、PNG/JPEG ImageBrushをPathでclipして読込。埋め込みfont・厳密なglyph配置・gradient・tile/crop mapping・resource dictionary・classic DWF payloadは警告付きの近似/省略。 |
| | `.html`, `.htm` | **A** | **A** | セマンティックHTMLマルチページ組版（見出し・段落・リスト・コードブロック・表・日本語CJK禁則処理）。同じディレクトリ内のPNG/JPEG `img`をフロー画像として埋め込み、`src`がないimgは`srcset`の最初の候補を使います。CSSの寸法・回り込み・responsive選択は近似。外部・範囲外・未対応画像はwarning付きで省略。<br>逆: SVGをダークモード対応・中央配置のスタンドアロンなレスポンシブHTML5ビューアとして出力。 |
| | `.epub` | **A** | - | 電子書籍EPUBパッケージ（container.xml、OPFマニフェスト、Spine順XHTML連続組版）。パッケージ内PNG/JPEGの`img`参照を埋め込み、`src`がないimgは`srcset`の最初の候補を使います。外部・CSS・SVGなどの画像は警告して省略。 |
| | `.fb2`, `.fb2.zip` | **A** | - | FictionBook 2 XML電子書籍（単一bookをZIPで配布する形式を含む）。最初のmain `body`/`section`、title/author、段落・見出し・表、`xlink:href`で参照されるbase64 PNG/JPEG `<binary>`を描画。notes body、外部リンク、未対応binary、macro実行、厳密なreader layoutは省略またはwarning。 |
| | `.mobi`, `.prc`, `.azw` | **A** | - | PalmDOC/MOBI電子書籍と非DRM AZW互換record。Palm Database record offset/件数、PalmDOC header、UTF-8/Windows-1252 text encoding、無圧縮/PalmDOC LZ77 text recordを検証・bounded decodeし、safe HTML-like textを組版。Huff/CDIC、DRM/暗号化、画像record、script、link、KF8固有構造、厳密なreader layoutは未対応。 |
| | `.dbk`, `.docbook` | **A** | - | DocBook 4/5 article/book XML。title、section、paragraph、list、source block、simple tableと、入力ディレクトリ内で検証したPNG/JPEG `imagedata`/`graphic`をboundedに描画。DTD、XInclude、外部link、MathML、script、publisher extension、厳密な印刷組版は省略またはwarning。 |
| | `.dita`, `.ditamap` | **A** | - | DITA 1.3 topic/map XML。title、shortdesc、section、paragraph、list、code block、simple tableと、検証済みローカルPNG/JPEG `image`をboundedに描画。mapは同一入力ディレクトリ内の`topicref`だけを解決し、key解決、DTD、XInclude、外部link、foreign content、厳密な出版組版は省略またはwarning。 |
| | `.hwpx` | **A** | - | Hancom HWPX/HWPML package。section paragraph、simple table、package内PNG/JPEG BinData imageをboundedに描画。外部resource、control、OLE、script、未対応image、厳密なHancom layoutは省略またはwarning。
| | `.cbz` | **A** | - | ZIP型コミックarchive。内包PNG/JPEGをファイル名の自然順に1ページずつSVGへ埋め込みます。ほかの画像形式は警告して省略し、ComicInfo・EXIF向き・カラープロファイルは適用しません。 |
| | `.odt`, `.ott`, `.fodt`, `.sxw`, `.stw`, `.sxg` | **A** | - | OpenDocument Textと旧OpenOffice Writer XML（`application/vnd.sun.xml.writer*`）を処理。見出し・段落・リスト・表・bounded styleと検証済み画像を表示し、外部resourceは不活性です。 |
| | `.ods`, `.ots`, `.fods`, `.sxc`, `.stc` | **A** | - | OpenDocument表計算と旧OpenOffice Calc XML（`application/vnd.sun.xml.calc*`）を処理。シート表・キャッシュ済み値・bounded画像を表示し、anchor・graph・formulaは近似/不活性です。 |
| | `.odp`, `.otp`, `.fodp`, `.sxi`, `.sti` | **A** | - | OpenDocumentプレゼンテーションと旧OpenOffice Impress XML（`application/vnd.sun.xml.impress*`）を処理。スライド順・寸法・基本図形・text・bounded画像を表示し、外部mediaは不活性です。 |
| | `.odg`, `.otg`, `.fodg`, `.sxd`, `.std` | **A** | - | OpenDocument図面と旧OpenOffice Draw XML（`application/vnd.sun.xml.draw*`）を処理。ページ・基本図形・text・bounded画像を表示し、外部resourceは不活性です。 |
| | `.vsdx`, `.vsdm`, `.vstx`, `.vstm`, `.vdx` | **A** | - | Visio Open XML図面/テンプレートと旧Visio XML図面。ページ順、ShapeSheetに直接あるstyle、基本path、1次元コネクタの端点、テキストを描画します。master継承、group、foreign object、arrowhead、曲線routingは警告付きで省略または近似。外部relationshipは取得せず、macroは実行しません。 |
| | `.vsd`, `.vss`, `.vst`, `.vsw` | **A** | - | 旧Visio Compound File Binaryのdrawing/stencil/template/workspaceを検証し、stream/storage metadataをbounded表示。ShapeSheet geometry、text、style、macro、OLE payload、外部linkは不活性です。 |
| | `.pages`, `.numbers`, `.key` | **A** | - | ZIP型Apple iWork Pages/Numbers/Keynote packageを検証し、packageと既知markerのmetadataをbounded表示。IWA protobuf、文書text/formula/slide geometry、preview、embedded media、script、外部linkは不活性です。`.key`はZIP signatureでLS-DYNAと区別します。 |
| | `.dwg` | **A** | - | Autodesk DWG binary drawingを6-byte AC10xx version headerとfile sizeだけで事前検証し、compressed section、entity、block、layer、proxy graphic、macro、外部referenceはデコードしません。 |
| | `.3dm` | **A** | - | Rhino/OpenNURBS 3DMを安定した`3D Geometry File Format` markerとbounded file metadataから事前検証。NURBS/mesh chunk、layer、material、texture、plugin、外部resourceは不活性です。 |
| | `.accdb`, `.accde`, `.accdr`, `.mdb`, `.mde`, `.mda`, `.mdt`, `.accdt`, `.ade` | **A** | - | Microsoft Access ACE/Jet databaseのengine markerとpage-size metadataだけを検証。table、row、query、form、report、attachment、VBA/macro、linked database、暗号化payloadは不活性です。 |
| | `.3dxml` | **A** | - | Dassault 3DXML ZIP packageのlocal Manifest→Root relationshipを検証し、ProductStructure/Reference3D/Instance3D/Representation countをbounded表示。binary 3DRep tessellation、exact geometry、texture、外部resourceは不活性です。 |
| | `.op2` | **A** | - | Nastran Output2 result databaseをboundedなrecord framingとGEOM1/OUGV1/OES1等のtable labelだけで事前検証。model geometry、element connectivity、result vector、subcase semantics、外部path、solver operationは不活性です。 |
| | `.ipc2581`, `.ipc-2581`, `.cvg` | **A** | - | IPC-2581 PCB design/manufacturing/assembly/inspection XMLのContent、BOM、ECAD、AVL、board、layer、component、net、route、padstack、feature countを表示。座標、material、tool path、inspection payload、外部reference、manufacturing operationは不活性です。 |
| | `.jt` | **A** | - | Siemens JTを固定80文字Version headerとbyte-order markerだけで事前検証。TOC/LSG segment、tessellation、Parasolid XT B-Rep、PMI、attribute、外部resourceは不活性です。 |
| | `.md`, `.markdown`, `.txt`, `.text` | **A** | **A** / **C** | マルチページMarkdown・プレーンテキスト文書組版（見出し・リスト・コード・引用・表）または単独表。単独行と段落内の`![alt](path)`PNG/JPEGを入力ディレクトリ内から上限付きで読みフロー画像として埋め込み、inline配置は近似。他の文脈では代替テキストを表示。<br>逆: メタデータ復元(**A**)または表構造再構成(**C**)。 |
| | `.adoc`, `.asciidoc` | **A** | - | AsciiDoc技術文書（セクション見出し・リスト・コードブロック・表・段落・ブロック画像マクロ `image::target[attrs]`）。入力ディレクトリ内の相対 `imagesdir` PNG/JPEG は中央寄せのフローブロックとして埋め込み、外部・脱出・未対応画像は警告付きで省略。画像サイズ・配置・キャプション・リンク・inline画像などのレイアウトは近似。 |
| | `.rst`, `.rest` | **A** | - | reStructuredText文書（装飾線の見出し、リスト、表、リテラル/コードブロック、admonition、入力フォルダ内のPNG/JPEG画像）。ファイル挿入/raw directiveは実行しません。 |
| | `.org` | **A** | - | Org-mode outline、TODO見出し、リスト、表、source/example block、quote block、入力フォルダ内のPNG/JPEG file link（`#+ATTR_ORG :width N`は最大4096 px）。Babel code、`#+INCLUDE`、table formula、raw exportは実行しません。 |
| | `.po`, `.pot` | **A** | - | GNU gettext翻訳カタログ。context、source/translation、plural form、note、fuzzy状態を表示。format-string directiveは文字列として扱い、obsolete entryは省略。 |
| | `.bib`, `.bibtex` | **A** | - | BibTeX bibliography entry。type/key、author/title/year/DOIなどのfieldを表示し、nested brace、引用field、commentを処理。`@string` macro展開、style適用、crossref解決、TeX実行は行いません。 |
| **化学構造** | `.mol`, `.sdf`, `.sd` | **A** | - | V2000およびcore V3000のMOL/SDF atom/bond tableを分子ごとにSVG pageへ描画。V3000のcontinuation line、非連番atom ID、`CHG`/`MASS`、単純なbond `CFG`に対応。座標、implicit carbon vertex、元素label、formal charge/isotope、基本bond order、上下wedge/hash markを表示。SDF data field、Sgroup、拡張stereo、query chemistry、atom mapping、化学計算は省略または未対応。input/record/atom/bond/page/node上限があります。 |
| | `.rxn` | **A** | - | V2000 RXNのreactant/productを反応矢印付きの1枚の図として描画。各側最大2 componentで、MOL/SDFの座標・bond表示を再利用します。V3000 RXN container、reaction condition/agent、化学反応の計算・validationは行いません。 |
| | `.pdb`, `.ent` | **A** | - | Protein Data Bankの固定幅ATOM/HETATM座標。MODELごとに1ページを生成し、CONECTを簡易bondとして描画、element labelを表示。3D座標はXYへ投影し、blank/A以外のalternate location、結晶学metadata、symmetry、CONECTにないbond、生物学的assembly semanticsは省略またはwarning。 |
| | `.srt`, `.vtt` | **A** | - | SubRip/WebVTT字幕のcue順と開始・終了時刻を表示。WebVTTのNOTE・STYLE/REGIONは省略し、cue位置・装飾はwarning付きで平文化。WebVTTはUTF-8、SRTはUTF-8/ BOM付きUTF-16/Windows-1252 fallbackに対応。外部resourceやactive contentは読み込みません。 |
| | `.ttml`, `.dfxp` | **A** | - | TTML/DFXPのtext-profile cueを組版し、`begin`/`end`/`dur`とparallel containerの開始offsetを処理。parent containerの終了境界は適用せずwarning。style、region、animation、image-profile内容、正確なlayoutはwarning付きで省略。sequential containerとmedia以外のtime baseは拒否。 |
| | `.xlf`, `.xliff` | **A** | - | XLIFF 1.2/2.xのsource/target、language、segment state、note、contextを組版。inline codeはplaceholder labelで保持し、alternative translationとbinary dataは省略、外部resourceは読み込みません。 |
| **ダイアグラム** | `.drawio`, `.dio`, `.xml` | **A** | **A** / **C** | mxGraphモデル & ステンシル描画。<br>逆: `--embed-drawio-source`保持時は完全可逆復元(**A**)。未保持時は画像埋め込み(**A**)または図形再構成(**C**)。 |
| | `.cmmn` | **A** | - | CMMN 1.1 case planをCMMNDIのcase boundary、plan-item task/milestone、dotted connectorのBounds/waypointから描画。case-file reference、sentry、criterion、lifecycle rule、expressionは不活性に保持し、case executionはしません。上限: 32 MiB input、500,000 XML event、200,000 XML element/rendered node、深さ80、100 diagram/page、座標±10,000,000。出典: [OMG CMMN 1.1](https://www.omg.org/spec/CMMN/1.1/PDF)。 |
| | `.graphml` | **A** | - | GraphML 1.0のnode/edge、directed/undirected、label、yFilesの基本shapeをboundedなlayered diagramとして描画。nested/compound node、hyperedge、custom keyの意味、座標保持、外部resourceは省略またはwarning。DTDは拒否。 |
| | `.gexf` | **A** | - | GEXF 1.3 graph exchange。static node/edge、directed/undirected、label、namespace付きlabelをboundedな図として描画。dynamic spell、attribute、layout、plugin、compound構造、外部resourceは省略またはwarning。DTDは拒否。 |
| | `.xgmml` | **A** | - | XGMML/Cytoscape graph XML。graph/node/edge、label、directed flag、`att`/graphicsの診断をbounded layered rendererで描画。attribute column、座標、nested subgraph、外部resourceは省略またはwarning。DTDは拒否。 |
| | `.gml` (Graph Modeling Language) | **A** | - | `graph [ ... ]`形式のGML graph。node/edge、label、comment、directed flagを表示し、地理GML XMLとはcontent sniffで区別。任意attribute、graphics座標、非UTF-8 encodingは省略または拒否。 |
| | `.bpmn`, `.bpmn2` | **A** | - | BPMN 2.0 process diagramをBPMN DIのshape/waypoint geometryから描画。event、task、gateway、pool/lane、sequence flowに対応。DI geometryが必須。message flow、data object、event-definition icon、process実行は省略・warning。上限: 32 MiB input、500,000 XML event、200,000 XML element/rendered node、深さ80、100 diagram/page、座標±10,000,000。出典: [OMG BPMN 2.0.2](https://www.omg.org/spec/BPMN/2.0.2/PDF)。 |
| | `.excalidraw`, `.excalidraw.json` | **A** | - | Excalidraw手描きホワイトボードシーン（四角形・楕円・ダイヤ・矢印・フリーハンド線・テキスト）。 |
| | `.puml`, `.plantuml` | **A** | - | PlantUMLテキストダイアグラム（シーケンス図・参加者・メッセージ・ライフライン・一般グラフ）。 |
| | `.d2` | **A** | - | D2宣言型アーキテクチャ図（シェイプ宣言・方向付きエッジ・ラベル・グリッド配置）。 |
| | `.dot`, `.gv` | **A** | **A** / **C** | Graphviz階層DAGレイアウト。<br>逆: メタデータ復元(**A**)またはテキスト・矢印からのトポロジー推定(**C**)。 |
| | `.mmd`, `.mermaid` | **A** | **A** / **C** | フローチャート・シーケンス図。<br>逆: メタデータ復元(**A**)またはヒューリスティック抽出(**C**)。 |
| **CAD / CAM / 3D** | `.dxf` | **A** | **A** | ASCIIおよびBinary DXFの2D/3Dエンティティ。順: 2D/3Dエンティティ。<br>逆: SVGパス・テキストをAutoCAD R12 DXFへ直接マッピング。 |
| | `.gbr`, `.gerber`, `.gtl`, `.gbl`, `.gts`, `.gbs`, `.gto`, `.gbo`, `.gko`, `.gm1`, `.gm2` | **A** | **A** | プリント基板RS-274Xアパーチャ・フラッシュ（全標準レイヤー拡張子に対応）。<br>逆: CAMフォトプロッターコマンド生成。 |
| | `.kicad_pcb` | **A** | - | KiCad board S-expressionをミリメートル座標の2D previewへ変換します。trace/arc/via、common pad、Edge.Cuts、board/footprint graphicと保存済みfilled zoneを描画。image、3D model、custom pad、複雑なcurve、non-unit scale footprint、DRC、zone再計算は行わず、回転textは水平表示します。 |
| | `.scad` または内容判定されたOpenSCAD source | **A** | - | OpenSCAD CAD sourceを不活性codeとしてscanし、module/function、primitive、transform、boolean、assignment、import/use/include参照を集計します。geometry、expression、loop、library、外部fileは実行・読込しません。上限: 入力128 MiB、2,000,000 line、1 MiB/line、表示row 100,000。出典: [OpenSCAD Language Reference](https://files.openscad.org/documentation/manual/The_OpenSCAD_Language.html)。 |
| | `.amf` または内容判定されたAMF 1.2 | **A** | - | ISO/ASTM 52915 Additive Manufacturing File Format XML。objectごとのvertexとvolume triangleを既存のshaded OBJ rendererで描画し、unitはmetadataとして保持。material、texture、color、lattice、slice、外部referenceは不活性です。上限: 入力128 MiB、XML event 500,000、node 300,000、vertex 2,000,000、triangle 200,000。出典: [ISO/ASTM 52915](https://www.iso.org/standard/74640.html)。 |
| | `.plmxml`, `.plm.xml` または内容判定されたPLMXML | **A** | - | Siemens PLM XMLのproduct/assembly文書。ProductDef、Part、Structure、Instance、Representation、ConstructionGeometry、Attribute、ExternalReference countを不活性metadataとして表示。XT/Parasolid geometry、ID、attribute value、URL、外部fileは開きません。上限: 入力128 MiB、XML event 1,000,000、node 500,000、深さ128、row 200,000。出典: [Siemens PLMXML schema](https://media.plm.automation.siemens.com/open/plm-xml/docs/v7.0.2/documentation/plmxml_PLMXML.html)。 |
| | `.stepxml`, `.stpx`, `.step.xml` または内容判定されたSTEP-XML | **A** | - | ISO 10303-28 STEP-XML/AP242 product dataを読み、product、product_definition、assembly occurrence、representation、geometric item、point、direction、property、external reference countを不活性metadataとして表示。EXPRESS rule、外部schema、ID、URL、参照CAD geometryは評価・読込しません。上限: 入力128 MiB、XML event 1,000,000、node 500,000、深さ128、row 200,000。出典: [ISO 10303-28](https://www.iso.org/standard/40646.html)。 |
| | `.qif`, `.qif.xml` または内容判定されたQIF | **A** | - | Digital Metrology Standards Consortium Quality Information Framework XML。product、product definition、measurement plan/result、feature、characteristic、datum、traceability、external file reference countを不活性metadataとして表示。測定値、tolerance、ID、URL、外部CAD/inspection fileは開きません。上限: 入力128 MiB、XML event 1,000,000、node 500,000、深さ128、row 200,000。出典: [QIF overview](https://qifstandards.org/overview/)。 |
| | `.b2mml`, `.b2mml.xml` または内容判定されたB2MML | **A** | - | ISA-95/MESA B2MML manufacturing XML。production schedule/performance/request/response、product、material、equipment、personnel、process segment、capability、maintenance、transaction、external reference countを不活性metadataとして表示。operation、value、credential、URL、外部resourceは実行・取得しません。上限: 入力128 MiB、XML event 1,000,000、node 500,000、深さ128、row 200,000。出典: [B2MML validation schema](https://github.com/werdnav/b2mml-validation)。 |
| | `.jdf`, `.jdf.xml`, `.jmf`, `.xjdf` または内容判定されたJDF/JMF/XJDF | **A** | - | CIP4 Job Definition/Messaging Format XML。job node、resource/pool/link、process、product、device、media、layout、run list、audit、file/URL link countを不活性metadataとして表示。device command、production operation、URL、credential、link fileは実行・取得しません。上限: 入力128 MiB、XML event 1,000,000、node 500,000、深さ128、row 200,000。出典: [CIP4 JDF/XJDF](https://www.cip4.org/print-automation/jdf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)。 |
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
