ryusui-hiro/document-svg/tests/fixtures/legacy_ppt.provenance.md

# Synthetic PowerPoint Binary fixture

`sample_legacy.ppt` is the synthetic `sample_strict.pptx` converted by LibreOffice 26.2.2.2 using the PowerPoint 97-2003 export filter. It contains two slides of authored conversion-guide text and has no personal or third-party content. Source and output hashes are recorded in `legacy_ppt.provenance.json`.
