ryusui-hiro/document-svg/tests/fixtures/sample_ltspice.asc

C1: cap; 1u
R1: res; 1k
Named nets: IN, OUT
.tran 1u 10m
