ryusui-hiro/document-svg/tests/fixtures/sample_legacy.sch

## KiCad design tests/fixtures/sample_legacy.sch (2026-09-20, an earlier design)

Schematic: sample_legacy.sch

Parts:
C1: 1u
R1: 1k

Notes on the sheet:
Legacy Eeschema preview
