ryusui-hiro/document-svg/src/pdf.rs

use std::cell::Cell;
use std::collections::{HashMap, HashSet};
use std::path::Path;
use std::rc::Rc;
use std::sync::Arc;

use base64::Engine;
#[cfg(not(target_arch = "wasm32"))]
use jpeg2k::{ColorSpace as Jpeg2000ColorSpace, Image as Jpeg2000Image};
use lopdf::content::{Content, Operation};
use lopdf::{Dictionary, Document, Object, ObjectId, Stream};
#[cfg(not(target_arch = "wasm32"))]
use rayon::prelude::*;
use skrifa::instance::{LocationRef, Size};
use skrifa::outline::DrawSettings;
use skrifa::raw::TableProvider;
use skrifa::{FontRef, MetadataProvider, Tag};

use crate::convert::{ConvertOptions, PageConsumer, read_limited_file};
use crate::error::{Error, Result};
use crate::ir::{
    GradientStop, IDENTITY, LineCap, LineJoin, LinearGradient, Matrix, Node, Page, Paint,
    RadialGradient, SourceMeta, Stroke, TextAnchor, TextRun, TilingPatternDefinition, compose,
    transform_point,
};
use crate::jpeg2000::{jpx_media_type, parse_jpx_header};
use crate::pdf_base14::standard_metrics;

const MAX_GRAPHICS_STACK: usize = 256;
const MAX_FORM_DEPTH: usize = 32;
const MAX_PAGE_MESH_TRIANGLES: usize = 50_000;
const MAX_PDF_ANNOTATIONS_PER_PAGE: usize = 10_000;
const MAX_PDF_PAGE_NODES: usize = 250_000;
const MAX_PDF_CHOICE_OPTIONS: usize = 10_000;
const MAX_PDF_CHOICE_TEXT_BYTES: usize = 2 * 1024 * 1024;
const MAX_PDF_FORM_VALUE_BYTES: usize = 2 * 1024 * 1024;
const MAX_PDF_DEFAULT_APPEARANCE_BYTES: usize = 64 * 1024;
const MAX_PDF_JPX_PIXELS: usize = 20_000_000;
const MAX_PDF_JPX_DECODED_SAMPLE_BYTES: usize = 128 * 1024 * 1024;
const MAX_PDF_JPX_PNG_BYTES: usize = 64 * 1024 * 1024;

#[derive(Clone, Debug)]
struct PdfChoiceOption {
    export_value: Vec<u8>,
    display_value: Vec<u8>,
}

#[derive(Clone, Copy, Debug)]
struct JpxSampleLayout {
    row_bytes: usize,
    width: usize,
    height: usize,
    components: usize,
    bits: usize,
}

/// Image compression filters without a decoder in this crate.
/// `JPXDecode` is handled separately by the bounded JPEG 2000 path below.
const UNDECODABLE_IMAGE_FILTERS: &[&[u8]] = &[b"JBIG2Decode"];

pub(crate) fn convert(
    path: &Path,
    options: &ConvertOptions,
    sink: &mut dyn PageConsumer,
) -> Result<Vec<String>> {
    let bytes = read_limited_file(path, options.max_input_bytes, "PDF input")?;
    convert_bytes(&bytes, options, sink)
}

/// Convert a bounded PDF byte buffer without routing it through a temporary
/// file. Container formats such as DICOM can safely reuse the PDF renderer
/// after validating and extracting an embedded PDF stream.
pub(crate) fn convert_bytes(
    bytes: &[u8],
    options: &ConvertOptions,
    sink: &mut dyn PageConsumer,
) -> Result<Vec<String>> {
    if bytes.len() as u64 > options.max_input_bytes {
        return Err(Error::LimitExceeded(format!(
            "PDF input exceeds maximum limit of {} bytes",
            options.max_input_bytes
        )));
    }
    let (document, recovery_warning) =
        load_document_bytes(bytes, options.max_zip_entry_bytes, options.max_input_bytes)?;
    if document.is_encrypted() {
        return Err(Error::Unsupported(
            "encrypted PDFs are rejected; access controls are not bypassed".into(),
        ));
    }
    // A document that declared /Encrypt but no longer carries it was unlocked
    // with the empty user password while loading. lopdf discards per-object
    // decryption failures, so streams can survive that pass still encrypted;
    // `render_page` uses this to explain a page that decodes to nothing.
    let decrypted_in_place = document.was_encrypted();
    let pages = document.get_pages().into_iter().collect::<Vec<_>>();
    if pages.len() > options.max_pages {
        return Err(Error::LimitExceeded(format!(
            "PDF contains {} pages; maximum is {}",
            pages.len(),
            options.max_pages
        )));
    }
    let page_content_limit = usize::try_from(options.max_zip_entry_bytes)
        .unwrap_or(usize::MAX)
        .min(usize::MAX / 2);
    let mut warnings = Vec::new();
    warnings.extend(recovery_warning);
    #[cfg(not(target_arch = "wasm32"))]
    if options.jobs > 1 && pages.len() > 1 {
        let pool = rayon::ThreadPoolBuilder::new()
            .num_threads(options.jobs)
            .build()
            .map_err(|error| {
                Error::InvalidInput(format!("cannot create PDF worker pool: {error}"))
            })?;
        for batch in pages.chunks(options.jobs.max(1)) {
            let rendered = pool.install(|| {
                batch
                    .par_iter()
                    .map(|(page_number, page_id)| {
                        render_page(
                            &document,
                            *page_number as usize,
                            *page_id,
                            page_content_limit,
                            options.outline_embedded_pdf_text,
                            decrypted_in_place,
                        )
                    })
                    .collect::<Vec<_>>()
            });
            for page in rendered {
                let page = page?;
                warnings.extend(page.warnings.iter().cloned());
                sink.consume(page)?;
            }
        }
        return Ok(deduplicate(warnings));
    }
    for (page_number, page_id) in pages {
        let page = render_page(
            &document,
            page_number as usize,
            page_id,
            page_content_limit,
            options.outline_embedded_pdf_text,
            decrypted_in_place,
        )?;
        warnings.extend(page.warnings.iter().cloned());
        sink.consume(page)?;
    }
    Ok(deduplicate(warnings))
}

/// Decodes an `ASCIIHexDecode`-filtered byte stream (PDF32000 §7.4.2): pairs
/// of ASCII hex digits, with any other whitespace/formatting bytes ignored,
/// terminated by an `>` (a missing terminator just means "read to the end");
/// a trailing unpaired digit is padded with an implicit trailing zero.
fn decode_ascii_hex(input: &[u8]) -> Vec<u8> {
    let mut nibbles = Vec::with_capacity(input.len());
    for &byte in input {
        if byte == b'>' {
            break;
        }
        if let Some(value) = (byte as char).to_digit(16) {
            nibbles.push(value as u8);
        }
    }
    if nibbles.len() % 2 == 1 {
        nibbles.push(0);
    }
    nibbles
        .chunks_exact(2)
        .map(|pair| (pair[0] << 4) | pair[1])
        .collect()
}

/// Decodes a stream the same way `Document::get_page_content_with_limit`
/// does: on any decode error other than exceeding `remaining`, fall back to
/// the stream's raw (still-encoded) bytes -- still bounded by `remaining` --
/// rather than propagating the error. lopdf itself relies on this leniency
/// for content streams using a filter it has no decoder for at all (some
/// real-world files declare a filter like `JBIG2Decode` on what is, in
/// effect, throwaway/junk page content); losing that leniency here would
/// turn an already-tolerated oddity into a hard conversion failure.
fn decode_stream_leniently(
    stream: &Stream,
    remaining: usize,
    content_limit: usize,
) -> Result<Vec<u8>> {
    match stream.decompressed_content_with_limit(remaining) {
        Ok(data) => Ok(data),
        Err(lopdf::Error::Decompress(lopdf::DecompressError::MemoryLimitExceeded { .. })) => {
            Err(Error::LimitExceeded(format!(
                "PDF page content stream exceeds {content_limit} bytes"
            )))
        }
        Err(_) => {
            if stream.content.len() > remaining {
                return Err(Error::LimitExceeded(format!(
                    "PDF page content stream exceeds {content_limit} bytes"
                )));
            }
            Ok(stream.content.clone())
        }
    }
}

/// Like `Document::get_page_content_with_limit`, but also decodes an
/// `ASCIIHexDecode`-filtered content stream ourselves. lopdf's own stream
/// decoder only implements `FlateDecode`/`LZWDecode`/`ASCII85Decode`, and on
/// any other filter it silently falls back to the RAW, still-encoded stream
/// bytes rather than propagating an error -- so an ASCIIHexDecode content
/// stream's literal hex-digit text would otherwise be fed straight into the
/// content-operator tokenizer as garbage. We peel a leading ASCIIHexDecode
/// layer off ourselves and let lopdf decode whatever filters remain.
fn page_content_with_limit(
    document: &Document,
    page_id: ObjectId,
    content_limit: usize,
) -> Result<Vec<u8>> {
    let mut content = Vec::new();
    for object_id in document.get_page_contents(page_id) {
        let Ok(stream) = document.get_object(object_id).and_then(Object::as_stream) else {
            continue;
        };
        let remaining = content_limit.saturating_sub(content.len());
        let filters = stream.filters().unwrap_or_default();
        let data = if filters.first() == Some(&b"ASCIIHexDecode".as_slice()) {
            let decoded = decode_ascii_hex(&stream.content);
            if filters.len() == 1 {
                if decoded.len() > remaining {
                    return Err(Error::LimitExceeded(format!(
                        "PDF page content stream exceeds {content_limit} bytes"
                    )));
                }
                decoded
            } else {
                let mut rest = stream.clone();
                rest.dict.set(
                    "Filter",
                    Object::Array(
                        filters[1..]
                            .iter()
                            .map(|filter| Object::Name(filter.to_vec()))
                            .collect(),
                    ),
                );
                rest.content = decoded;
                decode_stream_leniently(&rest, remaining, content_limit)?
            }
        } else {
            decode_stream_leniently(stream, remaining, content_limit)?
        };
        content.extend_from_slice(&data);
        content.push(b'\n');
    }
    Ok(content)
}

fn render_page(
    document: &Document,
    page_number: usize,
    page_id: ObjectId,
    content_limit: usize,
    outline_embedded_pdf_text: bool,
    decrypted_in_place: bool,
) -> Result<Page> {
    let box_values = inherited_page_array(document, page_id, b"CropBox")
        .or_else(|| inherited_page_array(document, page_id, b"MediaBox"))
        .unwrap_or([0.0, 0.0, 612.0, 792.0]);
    let rotation = inherited_page_number(document, page_id, b"Rotate")
        .unwrap_or(0.0)
        .round() as i32;
    let rotation = rotation.rem_euclid(360);
    let user_unit = page_user_unit(document, page_id)?;
    let source_width = (box_values[2] - box_values[0]).abs().max(1.0) * user_unit;
    let source_height = (box_values[3] - box_values[1]).abs().max(1.0) * user_unit;
    let (width, height) = if matches!(rotation, 90 | 270) {
        (source_height, source_width)
    } else {
        (source_width, source_height)
    };
    let page_matrix = compose(
        [user_unit, 0.0, 0.0, user_unit, 0.0, 0.0],
        page_matrix(box_values, rotation),
    );
    let mut page = Page::new(page_number, width, height, "pdf");
    page.description = format!("PDF page {page_number} converted from content operators");
    let content_bytes = page_content_with_limit(document, page_id, content_limit)?;
    let operations = decode_content_operations(&content_bytes, content_limit, &mut page)?;
    let fonts = build_font_decoders(document, page_id, content_limit, &mut page)?;
    let mut interpreter = Interpreter {
        document,
        page: &mut page,
        page_matrix,
        page_id,
        fonts,
        resources: Vec::new(),
        state: GraphicsState::default(),
        content_base_ctm: IDENTITY,
        stack: Vec::new(),
        path: PathBuilder::default(),
        pending_clip_rule: None,
        text: TextState::default(),
        node_counter: 0,
        clip_counter: 0,
        mask_counter: 0,
        compatibility_depth: 0,
        visited_forms: HashSet::new(),
        visited_patterns: HashSet::new(),
        mesh_output_count: Rc::new(Cell::new(0)),
        hidden_ocgs: hidden_optional_content_groups(document),
        marked_content_hidden: false,
        marked_content_stack: Vec::new(),
        content_limit,
        outline_embedded_pdf_text,
    };
    interpreter.interpret(&operations, 0)?;
    if !interpreter.stack.is_empty() {
        interpreter
            .page
            .warn("PDF graphics-state stack was not balanced at end of page");
    }
    interpreter.render_annotations()?;
    // A page that consumed a content stream yet drew nothing is indistinguishable
    // from a genuinely empty page in the SVG, so say which one it was. The most
    // common cause is a stream that survived loading still encrypted: lopdf
    // ignores per-object decryption failures, and the resulting bytes decode as
    // a few meaningless operators rather than as an error.
    let content_is_blank = content_bytes
        .iter()
        .all(|byte| byte.is_ascii_whitespace() || *byte == 0);
    if page.nodes.is_empty() && !content_is_blank {
        if decrypted_in_place {
            page.warn(format!(
                "PDF page {page_number} drew nothing from {} byte(s) of content; the document was encrypted and this stream was probably not decrypted",
                content_bytes.len()
            ));
        } else {
            page.warn(format!(
                "PDF page {page_number} drew nothing from {} byte(s) of content",
                content_bytes.len()
            ));
        }
    }
    Ok(page)
}

fn decode_content_operations(
    data: &[u8],
    content_limit: usize,
    page: &mut Page,
) -> Result<Vec<Operation>> {
    let mut operations = Vec::new();
    let mut position = 0usize;
    while let Some(inline_start) = find_pdf_syntax_token(data, position, b"BI") {
        if inline_start > position {
            operations.extend(decode_pdf_content(&data[position..inline_start])?.operations);
        }
        let dictionary_start = inline_start + 2;
        let Some(id_position) = find_pdf_syntax_token(data, dictionary_start, b"ID") else {
            return Err(Error::InvalidInput(
                "PDF inline image has no ID delimiter".into(),
            ));
        };
        let spec = InlineImageSpec::parse(&data[dictionary_start..id_position]);
        let data_start = skip_inline_separator(data, id_position + 2);
        let mut decoded = None::<(Stream, usize)>;
        // An unfiltered inline image's byte length is fully determined by
        // its own dictionary (row-padded, like any other raster image), so
        // this checks that exact position before falling back to a generic
        // scan for "EI". The PDF spec recommends, but does not require, a
        // white-space byte between the last data byte and EI; real-world
        // encoders sometimes omit it, which defeats the scan below whenever
        // that last data byte does not itself happen to be a PDF delimiter
        // (pdf.js's own bug1513120_reduced.pdf and issue10388_reduced.pdf
        // both ship 1-bit image masks built exactly this way).
        if spec.filter.is_none()
            && let Some(length) = spec.unfiltered_byte_length()
        {
            let candidate_end = data_start.saturating_add(length);
            if candidate_end <= data.len() {
                let after_data = skip_inline_separator(data, candidate_end);
                if data.get(after_data..after_data + 2) == Some(b"EI")
                    && data
                        .get(after_data + 2)
                        .is_none_or(|byte| is_pdf_delimiter(*byte))
                {
                    decoded = spec
                        .decode(&data[data_start..candidate_end], content_limit)
                        .map(|stream| (stream, after_data + 2));
                }
            }
        }
        if decoded.is_none() {
            let mut search_position = data_start;
            while let Some(ei_position) = find_pdf_token(data, search_position, b"EI") {
                let raw_end = trim_inline_data_end(data, data_start, ei_position);
                if let Some(stream) = spec.decode(&data[data_start..raw_end], content_limit) {
                    decoded = Some((stream, ei_position + 2));
                    break;
                }
                search_position = ei_position + 2;
            }
        }
        if let Some((stream, next_position)) = decoded {
            operations.push(Operation::new("BI", vec![Object::Stream(stream)]));
            position = next_position;
        } else if let Some(ei_position) = find_pdf_token(data, data_start, b"EI") {
            page.warn(format!(
                "PDF inline image filter {} could not be recovered",
                spec.filter.as_deref().unwrap_or("unfiltered")
            ));
            position = ei_position + 2;
        } else {
            return Err(Error::InvalidInput(
                "PDF inline image has no EI delimiter".into(),
            ));
        }
    }
    if position < data.len() {
        operations.extend(decode_pdf_content(&data[position..])?.operations);
    }
    Ok(operations)
}

/// Decodes a PDF content stream, first stripping `%` comments ourselves.
///
/// A `%` comment that trails a real operator on the same line -- rather
/// than sitting alone on its own line -- made `lopdf::content::Content`'s
/// own parser drop every operation in the stream silently, turning an
/// otherwise ordinary page into a blank one with no warning anywhere: the
/// content is well past "malformed" by any reasonable definition, it is
/// just formatted with a trailing `%` per line for visual column
/// alignment, which the PDF grammar allows (a comment runs to the next
/// end of line; an empty one is legal). This is `Content::decode`'s only
/// caller, so every caller of *this* function gets the same robustness.
fn decode_pdf_content(data: &[u8]) -> Result<Content> {
    Ok(Content::decode(&strip_pdf_content_comments(data))?)
}

/// Removes `%...` PDF comments (up to but excluding the next CR or LF)
/// from a content stream, leaving literal strings `(...)` and hex strings
/// `<...>` untouched even if a `%` happens to appear inside one -- there
/// it is just a character, not a comment marker. `<<`, a dictionary
/// delimiter rather than a hex string's `<`, is recognized and copied
/// through without entering hex-string state.
fn strip_pdf_content_comments(data: &[u8]) -> Vec<u8> {
    let mut output = Vec::with_capacity(data.len());
    let mut position = 0;
    let mut literal_depth = 0usize;
    let mut in_hex_string = false;
    while position < data.len() {
        let byte = data[position];
        if in_hex_string {
            output.push(byte);
            in_hex_string = byte != b'>';
            position += 1;
            continue;
        }
        if literal_depth > 0 {
            if byte == b'\\' && position + 1 < data.len() {
                output.push(byte);
                output.push(data[position + 1]);
                position += 2;
                continue;
            }
            output.push(byte);
            match byte {
                b'(' => literal_depth += 1,
                b')' => literal_depth -= 1,
                _ => {}
            }
            position += 1;
            continue;
        }
        match byte {
            b'(' => {
                literal_depth = 1;
                output.push(byte);
                position += 1;
            }
            b'<' if data.get(position + 1) == Some(&b'<') => {
                output.push(byte);
                output.push(data[position + 1]);
                position += 2;
            }
            b'<' => {
                in_hex_string = true;
                output.push(byte);
                position += 1;
            }
            b'%' => {
                while position < data.len() && !matches!(data[position], b'\r' | b'\n') {
                    position += 1;
                }
            }
            _ => {
                output.push(byte);
                position += 1;
            }
        }
    }
    output
}

fn find_pdf_syntax_token(data: &[u8], start: usize, token: &[u8]) -> Option<usize> {
    let mut position = start;
    let mut literal_depth = 0usize;
    let mut escaped = false;
    let mut hex_string = false;
    let mut comment = false;
    while position < data.len() {
        let byte = data[position];
        if comment {
            if matches!(byte, b'\r' | b'\n') {
                comment = false;
            }
            position += 1;
            continue;
        }
        if literal_depth > 0 {
            if escaped {
                escaped = false;
            } else if byte == b'\\' {
                escaped = true;
            } else if byte == b'(' {
                literal_depth += 1;
            } else if byte == b')' {
                literal_depth -= 1;
            }
            position += 1;
            continue;
        }
        if hex_string {
            if byte == b'>' {
                hex_string = false;
            }
            position += 1;
            continue;
        }
        match byte {
            b'%' => {
                comment = true;
                position += 1;
                continue;
            }
            b'(' => {
                literal_depth = 1;
                position += 1;
                continue;
            }
            b'<' if data.get(position + 1) != Some(&b'<') => {
                hex_string = true;
                position += 1;
                continue;
            }
            _ => {}
        }
        if data.get(position..position + token.len()) == Some(token) {
            let before = position
                .checked_sub(1)
                .and_then(|index| data.get(index))
                .is_none_or(|byte| is_pdf_delimiter(*byte));
            let after = data
                .get(position + token.len())
                .is_none_or(|byte| is_pdf_delimiter(*byte));
            if before && after {
                return Some(position);
            }
        }
        position += 1;
    }
    None
}

fn find_pdf_token(data: &[u8], start: usize, token: &[u8]) -> Option<usize> {
    let mut search = start;
    while search + token.len() <= data.len() {
        let offset = data
            .get(search..)?
            .windows(token.len())
            .position(|window| window == token)?;
        let position = search + offset;
        let delimited = {
            let before = position
                .checked_sub(1)
                .and_then(|index| data.get(index))
                .is_none_or(|byte| is_pdf_delimiter(*byte));
            let after = data
                .get(position + token.len())
                .is_none_or(|byte| is_pdf_delimiter(*byte));
            before && after
        };
        if delimited {
            return Some(position);
        }
        search = position + 1;
    }
    None
}

fn is_pdf_delimiter(byte: u8) -> bool {
    byte.is_ascii_whitespace() || matches!(byte, b'[' | b']' | b'<' | b'>' | b'(' | b')' | b'/')
}

fn skip_inline_separator(data: &[u8], mut position: usize) -> usize {
    if data.get(position..position + 2) == Some(b"\r\n") {
        return position + 2;
    }
    if data
        .get(position)
        .is_some_and(|byte| byte.is_ascii_whitespace())
    {
        position += 1;
    }
    position
}

fn trim_inline_data_end(data: &[u8], start: usize, mut end: usize) -> usize {
    if end > start && data[end - 1] == b'\n' {
        end -= 1;
        if end > start && data[end - 1] == b'\r' {
            end -= 1;
        }
    } else if end > start && data[end - 1].is_ascii_whitespace() {
        end -= 1;
    }
    end
}

#[derive(Default)]
struct InlineImageSpec {
    width: usize,
    height: usize,
    bits: usize,
    color_space: String,
    filter: Option<String>,
    k: i64,
    columns: usize,
    rows: usize,
    end_of_block: bool,
    end_of_line: bool,
    byte_aligned: bool,
    black_is_one: bool,
    damaged_rows_before_error: usize,
    interpolate: bool,
    image_mask: bool,
}

impl InlineImageSpec {
    fn parse(data: &[u8]) -> Self {
        let tokens = inline_dictionary_tokens(data);
        let value = |names: &[&str]| {
            tokens.iter().enumerate().find_map(|(index, token)| {
                names
                    .contains(&token.as_str())
                    .then(|| tokens.get(index + 1).cloned())
                    .flatten()
            })
        };
        let integer = |names: &[&str], default: i64| {
            value(names)
                .and_then(|value| value.parse().ok())
                .unwrap_or(default)
        };
        let boolean =
            |names: &[&str], default: bool| value(names).map_or(default, |value| value == "true");
        let width = integer(&["/W", "/Width"], 0).max(0) as usize;
        let height = integer(&["/H", "/Height"], 0).max(0) as usize;
        Self {
            width,
            height,
            bits: integer(&["/BPC", "/BitsPerComponent"], 8).max(1) as usize,
            color_space: value(&["/CS", "/ColorSpace"]).unwrap_or_else(|| "/G".into()),
            filter: value(&["/F", "/Filter"]),
            k: integer(&["/K"], 0),
            columns: integer(&["/Columns"], width as i64).max(0) as usize,
            rows: integer(&["/Rows"], height as i64).max(0) as usize,
            end_of_block: boolean(&["/EndOfBlock"], true),
            end_of_line: boolean(&["/EndOfLine"], false),
            byte_aligned: boolean(&["/EncodedByteAlign"], false),
            black_is_one: boolean(&["/BlackIs1"], false),
            damaged_rows_before_error: integer(&["/DamagedRowsBeforeError"], 0).max(0) as usize,
            interpolate: boolean(&["/I", "/Interpolate"], false),
            image_mask: boolean(&["/IM", "/ImageMask"], false),
        }
    }

    fn components(&self) -> usize {
        match self.color_space.as_str() {
            "/RGB" | "/DeviceRGB" => 3,
            "/CMYK" | "/DeviceCMYK" => 4,
            _ => 1,
        }
    }

    /// The exact byte length of an *unfiltered* inline image's own raw data,
    /// row-padded like any other raster image, or `None` if the width or
    /// height is not yet known. Filtered data has no such fixed length here
    /// (its compressed size does not follow from the pixel dimensions).
    fn unfiltered_byte_length(&self) -> Option<usize> {
        if self.width == 0 || self.height == 0 {
            return None;
        }
        let row_bytes = self
            .width
            .saturating_mul(self.components())
            .saturating_mul(self.bits)
            .div_ceil(8);
        Some(row_bytes.saturating_mul(self.height))
    }

    fn decode(&self, raw: &[u8], content_limit: usize) -> Option<Stream> {
        if self.width == 0 || self.height == 0 {
            return None;
        }
        let filter = self.filter.as_deref().unwrap_or("");
        let pixels = if matches!(filter, "/CCF" | "/CCITTFaxDecode") {
            self.decode_ccitt(raw)?
        } else if filter.is_empty() {
            raw.to_vec()
        } else {
            let filter_name = match filter {
                "/LZW" | "/LZWDecode" => b"LZWDecode".to_vec(),
                "/Fl" | "/FlateDecode" => b"FlateDecode".to_vec(),
                "/RL" | "/RunLengthDecode" => b"RunLengthDecode".to_vec(),
                "/A85" | "/ASCII85Decode" => b"ASCII85Decode".to_vec(),
                "/AHx" | "/ASCIIHexDecode" => b"ASCIIHexDecode".to_vec(),
                _ => return None,
            };
            let mut dictionary = Dictionary::new();
            dictionary.set("Filter", Object::Name(filter_name));
            Stream::new(dictionary, raw.to_vec())
                .decompressed_content_with_limit(content_limit)
                .ok()?
        };
        let components = self.components();
        let expected = self
            .width
            .saturating_mul(self.height)
            .saturating_mul(components)
            .saturating_mul(self.bits)
            .div_ceil(8);
        if self.bits == 8 && pixels.len() < expected {
            return None;
        }
        let mut dictionary = Dictionary::new();
        dictionary.set("Subtype", Object::Name(b"Image".to_vec()));
        dictionary.set("Width", self.width as i64);
        dictionary.set("Height", self.height as i64);
        dictionary.set(
            "BitsPerComponent",
            if filter.contains("CCF") {
                8
            } else {
                self.bits as i64
            },
        );
        dictionary.set(
            "ColorSpace",
            Object::Name(match self.color_space.as_str() {
                "/RGB" | "/DeviceRGB" => b"DeviceRGB".to_vec(),
                "/CMYK" | "/DeviceCMYK" => b"DeviceCMYK".to_vec(),
                _ => b"DeviceGray".to_vec(),
            }),
        );
        dictionary.set("Interpolate", self.interpolate);
        if self.image_mask {
            dictionary.set("ImageMask", true);
        }
        Some(Stream::new(dictionary, pixels))
    }

    fn decode_ccitt(&self, raw: &[u8]) -> Option<Vec<u8>> {
        let mode = if self.k < 0 {
            hayro_ccitt::EncodingMode::Group4
        } else if self.k == 0 {
            hayro_ccitt::EncodingMode::Group3_1D
        } else {
            hayro_ccitt::EncodingMode::Group3_2D { k: self.k as u32 }
        };
        let settings = hayro_ccitt::DecodeSettings {
            columns: self.columns.max(self.width) as u32,
            rows: self.rows.max(self.height) as u32,
            end_of_block: self.end_of_block,
            end_of_line: self.end_of_line,
            rows_are_byte_aligned: self.byte_aligned,
            encoding: mode,
            invert_black: self.black_is_one,
        };
        let mut decoder = GrayCcittDecoder::default();
        let mut context = hayro_ccitt::DecoderContext::new(settings);
        let required = self.width.saturating_mul(self.height);
        if hayro_ccitt::decode(raw, &mut decoder, &mut context).is_ok()
            && decoder.pixels.len() >= required
        {
            decoder.pixels.truncate(required);
            return Some(decoder.pixels);
        }
        if self.damaged_rows_before_error == 0
            || !self.end_of_line
            || self.k <= 0
            || self.byte_aligned
        {
            return None;
        }
        let reference_row = decoder
            .rows
            .checked_sub(1)
            .and_then(|row| {
                let start = row.checked_mul(self.width)?;
                decoder.pixels.get(start..start.checked_add(self.width)?)
            })
            .map(<[u8]>::to_vec);
        repair_group3_2d_damaged_row(
            raw,
            settings,
            required,
            decoder.rows,
            reference_row.as_deref(),
        )
    }
}

fn ccitt_spec_from_stream(stream: &Stream, width: usize, height: usize) -> InlineImageSpec {
    let parameters = stream
        .dict
        .get(b"DecodeParms")
        .or_else(|_| stream.dict.get(b"DP"))
        .ok()
        .and_then(|value| match value {
            Object::Dictionary(dictionary) => Some(dictionary),
            Object::Array(values) => values.first().and_then(|value| value.as_dict().ok()),
            _ => None,
        });
    let integer = |name: &[u8], default: i64| {
        parameters
            .and_then(|dictionary| dictionary.get(name).and_then(Object::as_i64).ok())
            .unwrap_or(default)
    };
    let boolean = |name: &[u8], default: bool| {
        parameters
            .and_then(|dictionary| dictionary.get(name).and_then(Object::as_bool).ok())
            .unwrap_or(default)
    };
    InlineImageSpec {
        width,
        height,
        bits: 8,
        color_space: "/G".into(),
        filter: Some("/CCITTFaxDecode".into()),
        k: integer(b"K", 0),
        columns: integer(b"Columns", width as i64).max(1) as usize,
        rows: integer(b"Rows", height as i64).max(1) as usize,
        end_of_block: boolean(b"EndOfBlock", true),
        end_of_line: boolean(b"EndOfLine", false),
        byte_aligned: boolean(b"EncodedByteAlign", false),
        black_is_one: boolean(b"BlackIs1", false),
        damaged_rows_before_error: integer(b"DamagedRowsBeforeError", 0).max(0) as usize,
        interpolate: stream
            .dict
            .get(b"Interpolate")
            .and_then(Object::as_bool)
            .unwrap_or(false),
        image_mask: false,
    }
}

fn repair_group3_2d_damaged_row(
    raw: &[u8],
    settings: hayro_ccitt::DecodeSettings,
    required_pixels: usize,
    failing_row: usize,
    reference_row: Option<&[u8]>,
) -> Option<Vec<u8>> {
    let bit_length = raw.len().checked_mul(8)?;
    let mut eol_positions = Vec::new();
    for position in 0..bit_length.saturating_sub(11) {
        if (0..11).all(|offset| packed_bit(raw, position + offset) == 0)
            && packed_bit(raw, position + 11) == 1
        {
            eol_positions.push(position);
            if eol_positions.len() > settings.rows as usize + 6 {
                break;
            }
        }
    }
    let row_count = settings.rows as usize;
    let mut candidates = vec![failing_row];
    if failing_row > 0 {
        candidates.push(failing_row - 1);
    }
    if failing_row + 1 < row_count {
        candidates.push(failing_row + 1);
    }
    for candidate in candidates {
        let Some(&start) = eol_positions.get(candidate) else {
            continue;
        };
        let Some(&end) = eol_positions.get(candidate + 1) else {
            continue;
        };
        if candidate == failing_row
            && let Some(reference_row) = reference_row
        {
            let mut repaired = Vec::with_capacity(raw.len());
            let mut repaired_bits = 0usize;
            append_packed_bits(raw, 0, start, &mut repaired, &mut repaired_bits);
            for _ in 0..11 {
                push_packed_bit(&mut repaired, &mut repaired_bits, 0);
            }
            push_packed_bit(&mut repaired, &mut repaired_bits, 1);
            push_packed_bit(&mut repaired, &mut repaired_bits, 0);
            let black_runs = reference_row
                .iter()
                .enumerate()
                .filter(|(index, pixel)| {
                    **pixel == 0 && (*index == 0 || reference_row[*index - 1] != 0)
                })
                .count();
            if black_runs == 0 {
                push_packed_bit(&mut repaired, &mut repaired_bits, 1);
            } else {
                for _ in 0..black_runs {
                    for bit in [0, 0, 0, 1] {
                        push_packed_bit(&mut repaired, &mut repaired_bits, bit);
                    }
                }
            }
            append_packed_bits(raw, end, bit_length, &mut repaired, &mut repaired_bits);
            if let Some(pixels) = decode_repaired_ccitt(&repaired, settings, required_pixels) {
                return Some(pixels);
            }
        }
        let mut replacements = Vec::new();
        if candidate > 0 {
            replacements.push((eol_positions[candidate - 1], start));
        }
        if let Some(&next_end) = eol_positions.get(candidate + 2) {
            replacements.push((end, next_end));
        }
        for (replacement_start, replacement_end) in replacements {
            let mut repaired = Vec::with_capacity(raw.len());
            let mut repaired_bits = 0usize;
            append_packed_bits(raw, 0, start, &mut repaired, &mut repaired_bits);
            append_packed_bits(
                raw,
                replacement_start,
                replacement_end,
                &mut repaired,
                &mut repaired_bits,
            );
            append_packed_bits(raw, end, bit_length, &mut repaired, &mut repaired_bits);
            if let Some(pixels) = decode_repaired_ccitt(&repaired, settings, required_pixels) {
                return Some(pixels);
            }
        }
        let mut repaired = Vec::with_capacity(raw.len());
        let mut repaired_bits = 0usize;
        append_packed_bits(raw, 0, start, &mut repaired, &mut repaired_bits);
        for _ in 0..11 {
            push_packed_bit(&mut repaired, &mut repaired_bits, 0);
        }
        push_packed_bit(&mut repaired, &mut repaired_bits, 1);
        push_packed_bit(&mut repaired, &mut repaired_bits, 0);
        push_packed_bit(&mut repaired, &mut repaired_bits, 1);
        append_packed_bits(raw, end, bit_length, &mut repaired, &mut repaired_bits);
        if let Some(pixels) = decode_repaired_ccitt(&repaired, settings, required_pixels) {
            return Some(pixels);
        }
    }
    None
}

fn decode_repaired_ccitt(
    data: &[u8],
    settings: hayro_ccitt::DecodeSettings,
    required_pixels: usize,
) -> Option<Vec<u8>> {
    let mut decoder = GrayCcittDecoder::default();
    let mut context = hayro_ccitt::DecoderContext::new(settings);
    hayro_ccitt::decode(data, &mut decoder, &mut context).ok()?;
    if decoder.pixels.len() < required_pixels {
        return None;
    }
    decoder.pixels.truncate(required_pixels);
    Some(decoder.pixels)
}

fn packed_bit(data: &[u8], position: usize) -> u8 {
    (data[position / 8] >> (7 - position % 8)) & 1
}

fn append_packed_bits(
    source: &[u8],
    start: usize,
    end: usize,
    output: &mut Vec<u8>,
    output_bits: &mut usize,
) {
    for position in start..end {
        push_packed_bit(output, output_bits, packed_bit(source, position));
    }
}

fn push_packed_bit(output: &mut Vec<u8>, bit_length: &mut usize, bit: u8) {
    if bit_length.is_multiple_of(8) {
        output.push(0);
    }
    if bit != 0 {
        let index = output.len() - 1;
        output[index] |= 1 << (7 - *bit_length % 8);
    }
    *bit_length += 1;
}

fn inline_dictionary_tokens(data: &[u8]) -> Vec<String> {
    let mut tokens = Vec::new();
    let mut position = 0usize;
    while position < data.len() {
        while data
            .get(position)
            .is_some_and(|byte| byte.is_ascii_whitespace())
        {
            position += 1;
        }
        if position >= data.len() {
            break;
        }
        let start = position;
        if data[position] == b'/' {
            position += 1;
            while position < data.len() && !is_pdf_delimiter(data[position]) {
                position += 1;
            }
            tokens.push(String::from_utf8_lossy(&data[start..position]).into_owned());
        } else if position + 1 < data.len()
            && matches!(&data[position..position + 2], b"<<" | b">>")
        {
            position += 2;
            tokens.push(String::from_utf8_lossy(&data[start..position]).into_owned());
        } else {
            while position < data.len() && !is_pdf_delimiter(data[position]) {
                position += 1;
            }
            if position == start {
                position += 1;
            }
            tokens.push(String::from_utf8_lossy(&data[start..position]).into_owned());
        }
    }
    tokens
}

#[derive(Default)]
struct GrayCcittDecoder {
    pixels: Vec<u8>,
    rows: usize,
}

impl hayro_ccitt::Decoder for GrayCcittDecoder {
    fn push_pixel(&mut self, white: bool) {
        self.pixels.push(if white { 255 } else { 0 });
    }

    fn push_pixel_chunk(&mut self, white: bool, chunk_count: u32) {
        self.pixels.extend(std::iter::repeat_n(
            if white { 255 } else { 0 },
            chunk_count as usize * 8,
        ));
    }

    fn next_line(&mut self) {
        self.rows += 1;
    }
}

#[derive(Clone, Debug)]
struct GraphicsState {
    ctm: Matrix,
    fill: Paint,
    stroke: Paint,
    fill_color_space: Object,
    stroke_color_space: Object,
    fill_pattern_clip: Option<PatternClip>,
    stroke_pattern_clip: Option<PatternClip>,
    line_width: f64,
    line_cap: LineCap,
    line_join: LineJoin,
    miter_limit: f64,
    dash_array: Vec<f64>,
    dash_offset: f64,
    fill_alpha: f64,
    stroke_alpha: f64,
    clip_id: Option<String>,
    blend_mode: String,
    mask_id: Option<String>,
    alpha_is_shape: bool,
}

impl Default for GraphicsState {
    fn default() -> Self {
        Self {
            ctm: IDENTITY,
            fill: Paint::solid("#000000"),
            stroke: Paint::solid("#000000"),
            fill_color_space: Object::Name(b"DeviceGray".to_vec()),
            stroke_color_space: Object::Name(b"DeviceGray".to_vec()),
            fill_pattern_clip: None,
            stroke_pattern_clip: None,
            line_width: 1.0,
            line_cap: LineCap::Butt,
            line_join: LineJoin::Miter,
            miter_limit: 10.0,
            dash_array: Vec::new(),
            dash_offset: 0.0,
            fill_alpha: 1.0,
            stroke_alpha: 1.0,
            clip_id: None,
            blend_mode: "normal".into(),
            mask_id: None,
            alpha_is_shape: false,
        }
    }
}

#[derive(Clone, Debug, PartialEq)]
struct PatternClip {
    bbox: [f64; 4],
    matrix: Matrix,
}

#[derive(Clone, Debug)]
struct TextState {
    font_name: Vec<u8>,
    font_size: f64,
    text_matrix: Matrix,
    line_matrix: Matrix,
    character_spacing: f64,
    word_spacing: f64,
    horizontal_scale: f64,
    leading: f64,
    rise: f64,
    rendering_mode: i64,
    pending_clips: Vec<PendingTextClip>,
}

#[derive(Clone, Debug)]
struct SavedTextParameters {
    font_name: Vec<u8>,
    font_size: f64,
    character_spacing: f64,
    word_spacing: f64,
    horizontal_scale: f64,
    leading: f64,
    rise: f64,
    rendering_mode: i64,
}

#[derive(Clone, Debug)]
struct SavedGraphicsState {
    graphics: GraphicsState,
    text: SavedTextParameters,
}

impl TextState {
    fn saved_parameters(&self) -> SavedTextParameters {
        SavedTextParameters {
            font_name: self.font_name.clone(),
            font_size: self.font_size,
            character_spacing: self.character_spacing,
            word_spacing: self.word_spacing,
            horizontal_scale: self.horizontal_scale,
            leading: self.leading,
            rise: self.rise,
            rendering_mode: self.rendering_mode,
        }
    }

    fn restore_parameters(&mut self, saved: SavedTextParameters) {
        self.font_name = saved.font_name;
        self.font_size = saved.font_size;
        self.character_spacing = saved.character_spacing;
        self.word_spacing = saved.word_spacing;
        self.horizontal_scale = saved.horizontal_scale;
        self.leading = saved.leading;
        self.rise = saved.rise;
        self.rendering_mode = saved.rendering_mode;
    }
}

#[derive(Clone, Debug)]
struct PendingTextClip {
    d: String,
    transform: Matrix,
}

impl Default for TextState {
    fn default() -> Self {
        Self {
            font_name: Vec::new(),
            font_size: 12.0,
            text_matrix: IDENTITY,
            line_matrix: IDENTITY,
            character_spacing: 0.0,
            word_spacing: 0.0,
            horizontal_scale: 1.0,
            leading: 0.0,
            rise: 0.0,
            rendering_mode: 0,
            pending_clips: Vec::new(),
        }
    }
}

#[derive(Clone, Debug, Default)]
struct PathBuilder {
    data: String,
    has_content: bool,
    current_point: Option<(f64, f64)>,
    subpath_start: Option<(f64, f64)>,
    /// `Some([x, y, width, height])` exactly when the path so far consists
    /// of nothing but a single `re` rectangle -- reset to `None` by any
    /// other path-construction call. Lets a fill notice a degenerate
    /// (zero-width or zero-height) rectangle specifically, without
    /// misfiring on a complex path that coincidentally has a zero-area
    /// bounding box for unrelated reasons (an even-odd "hole" fill, say).
    bare_rect: Option<[f64; 4]>,
}

impl PathBuilder {
    fn command(&mut self, operator: &str, values: &[f64]) {
        self.bare_rect = None;
        if self.has_content {
            self.data.push(' ');
        }
        self.data.push_str(operator);
        for value in values {
            self.data.push(' ');
            self.data.push_str(&fmt(*value));
        }
        self.has_content = true;
        match operator {
            "M" if values.len() >= 2 => {
                let point = (values[0], values[1]);
                self.current_point = Some(point);
                self.subpath_start = Some(point);
            }
            "L" if values.len() >= 2 => {
                self.current_point = Some((values[0], values[1]));
            }
            "C" if values.len() >= 6 => {
                self.current_point = Some((values[4], values[5]));
            }
            "Z" => self.current_point = self.subpath_start,
            _ => {}
        }
    }

    /// Adds a `re` rectangle, tracking it as a `bare_rect` when it is the
    /// path's only content so far.
    fn add_rect(&mut self, x: f64, y: f64, width: f64, height: f64) {
        let is_first = !self.has_content;
        self.command("M", &[x, y]);
        self.command("L", &[x + width, y]);
        self.command("L", &[x + width, y + height]);
        self.command("L", &[x, y + height]);
        self.command("Z", &[]);
        if is_first {
            self.bare_rect = Some([x, y, width, height]);
        }
    }

    fn take(&mut self) -> String {
        self.has_content = false;
        self.current_point = None;
        self.subpath_start = None;
        self.bare_rect = None;
        std::mem::take(&mut self.data)
    }

    fn clear(&mut self) {
        self.data.clear();
        self.has_content = false;
        self.current_point = None;
        self.subpath_start = None;
        self.bare_rect = None;
    }
}

/// A Type 1 font program parsed once per decoder.
///
/// `parse_type1` decrypts the eexec section and scans the whole program, so
/// running it for every text-showing operator dominated conversion of
/// Type 1-heavy PDFs. Cloning a decoder starts an empty cache rather than
/// duplicating the parse: clones are made per pattern or soft mask, not per
/// glyph.
#[derive(Default)]
struct Type1Cache(std::cell::OnceCell<Option<Box<stet_fonts::type1_parser::Type1Font>>>);

impl Clone for Type1Cache {
    fn clone(&self) -> Self {
        Self::default()
    }
}

impl std::fmt::Debug for Type1Cache {
    fn fmt(&self, formatter: &mut std::fmt::Formatter<'_>) -> std::fmt::Result {
        formatter
            .debug_struct("Type1Cache")
            .field("parsed", &self.0.get().is_some())
            .finish()
    }
}

#[derive(Clone, Debug)]
struct FontDecoder {
    family: String,
    bold: bool,
    italic: bool,
    requires_outline: bool,
    font_data: Option<Arc<[u8]>>,
    glyph_names: HashMap<u8, String>,
    unicode_map: HashMap<Vec<u8>, String>,
    code_lengths: Vec<usize>,
    fallback_kind: FontFallback,
    widths: HashMap<u32, f64>,
    default_width: f64,
    type3: Option<Arc<Type3Font>>,
    type1: Type1Cache,
    /// `true` for a Type0 font using Identity-H/V encoding, where the raw
    /// character code already *is* the CID (per PDF32000 9.7.5.2) rather
    /// than a value that must go through the font's own cmap to find a
    /// Unicode character first.
    identity_cid: bool,
    /// A CIDFontType2's own `/CIDToGIDMap` stream when present: CID `n`'s
    /// glyph ID is the big-endian `u16` at byte offset `2 * n`. `None`
    /// means the map is `/Identity` (the default, and by far the most
    /// common case): CID and GID are the same value.
    cid_to_gid_map: Option<Arc<[u8]>>,
}

#[derive(Clone, Debug)]
struct Type3Font {
    font_matrix: Matrix,
    resources: Option<Dictionary>,
    glyphs: HashMap<u8, Stream>,
}

#[derive(Clone, Copy, Debug)]
enum FontFallback {
    OneByte,
    Utf16Be,
}

/// Strips PFB (Printer Font Binary) segment framing from a Type1 font
/// program, when present. PDF32000 9.9's own `/FontFile` format is a plain
/// concatenation of the font's cleartext header, its encrypted binary
/// portion, and a zero-padding trailer -- no segment framing at all -- but
/// some producers instead embed the raw PFB container format verbatim. Its
/// interleaved 6-byte `0x80 <type> <u32 length>` segment headers land
/// squarely inside the encrypted portion, corrupting eexec decryption's
/// running cipher state (which carries across the whole ciphertext) from
/// that point on, and every glyph after it decrypts to garbage.
fn strip_pfb_segments(data: &[u8]) -> std::borrow::Cow<'_, [u8]> {
    if data.first() != Some(&0x80) {
        return std::borrow::Cow::Borrowed(data);
    }
    let mut out = Vec::with_capacity(data.len());
    let mut offset = 0;
    while data.get(offset) == Some(&0x80) {
        match data.get(offset + 1) {
            Some(1 | 2) => {
                let Some(length_bytes) = data.get(offset + 2..offset + 6) else {
                    break;
                };
                let length = u32::from_le_bytes(length_bytes.try_into().unwrap()) as usize;
                let start = offset + 6;
                let end = start.saturating_add(length).min(data.len());
                out.extend_from_slice(&data[start..end]);
                offset = end;
            }
            _ => break,
        }
    }
    std::borrow::Cow::Owned(out)
}

impl FontDecoder {
    fn decode(&self, bytes: &[u8]) -> (String, bool) {
        if !self.unicode_map.is_empty() {
            let mut result = String::new();
            let mut position = 0usize;
            let mut replacement = false;
            while position < bytes.len() {
                let mut matched = false;
                for length in &self.code_lengths {
                    if position + length > bytes.len() {
                        continue;
                    }
                    if let Some(value) = self.unicode_map.get(&bytes[position..position + length]) {
                        result.push_str(value);
                        position += length;
                        matched = true;
                        break;
                    }
                }
                if !matched {
                    result.push('\u{fffd}');
                    position += 1;
                    replacement = true;
                }
            }
            return (result, replacement);
        }
        match self.fallback_kind {
            FontFallback::OneByte => (bytes.iter().map(|byte| char::from(*byte)).collect(), false),
            FontFallback::Utf16Be => {
                let units = bytes
                    .chunks_exact(2)
                    .map(|pair| u16::from_be_bytes([pair[0], pair[1]]));
                let mut replacement = !bytes.len().is_multiple_of(2);
                let result = char::decode_utf16(units)
                    .map(|item| match item {
                        Ok(character) => character,
                        Err(_) => {
                            replacement = true;
                            '\u{fffd}'
                        }
                    })
                    .collect();
                (result, replacement)
            }
        }
    }

    fn width(&self, bytes: &[u8]) -> f64 {
        let code_length = if matches!(self.fallback_kind, FontFallback::Utf16Be) {
            self.code_lengths.first().copied().unwrap_or(2).max(1)
        } else {
            1
        };
        bytes
            .chunks(code_length)
            .map(|code| {
                self.widths
                    .get(&bytes_to_u32(code))
                    .copied()
                    .unwrap_or(self.default_width)
            })
            .sum::<f64>()
            / 1_000.0
    }

    fn code_count(&self, bytes: &[u8]) -> usize {
        let code_length = if matches!(self.fallback_kind, FontFallback::Utf16Be) {
            self.code_lengths.first().copied().unwrap_or(2).max(1)
        } else {
            1
        };
        bytes.len().div_ceil(code_length)
    }

    fn glyph_x_offsets(
        &self,
        bytes: &[u8],
        font_size: f64,
        character_spacing: f64,
        word_spacing: f64,
        horizontal_scale: f64,
    ) -> Option<Vec<f64>> {
        let code_length = if matches!(self.fallback_kind, FontFallback::Utf16Be) {
            self.code_lengths.first().copied().unwrap_or(2).max(1)
        } else {
            1
        };
        let inverse_horizontal_scale = 1.0 / horizontal_scale.abs().max(1e-12);
        let mut offsets = Vec::with_capacity(bytes.len().div_ceil(code_length));
        let mut x = 0.0;
        for code in bytes.chunks(code_length) {
            let (decoded, replacement) = self.decode(code);
            let mut characters = decoded.chars();
            let character = characters.next()?;
            if replacement || characters.next().is_some() {
                return None;
            }
            offsets.push(x);
            let width = self
                .widths
                .get(&bytes_to_u32(code))
                .copied()
                .unwrap_or(self.default_width)
                / 1_000.0
                * font_size;
            let spacing = character_spacing + if character == ' ' { word_spacing } else { 0.0 };
            x += width + spacing * inverse_horizontal_scale;
        }
        Some(offsets)
    }

    fn outline_path(
        &self,
        bytes: &[u8],
        character_spacing_em: f64,
        word_spacing_em: f64,
    ) -> std::result::Result<String, &'static str> {
        let data = self
            .font_data
            .as_ref()
            .ok_or("embedded font program is unavailable")?;
        let face = match FontRef::from_index(data, 0) {
            Ok(face) => face,
            Err(_) => {
                return self.outline_type1(data, bytes, character_spacing_em, word_spacing_em);
            }
        };
        let units_per_em = f64::from(
            face.head()
                .map_err(|_| "embedded font has no valid head table")?
                .units_per_em(),
        )
        .max(1.0);
        let charmap = face.charmap();
        let cmap = face.cmap().ok();
        let outlines = face.outline_glyphs();
        // A simple TrueType font with no cmap table at all -- legal, and
        // not even unusual for a subsetted font used only through a PDF
        // /Differences encoding -- leaves every cmap-based lookup above
        // with nothing to search. The font's own `post` table (when it
        // carries real glyph names, version 1.0 or 2.0) is the spec's own
        // fallback (PDF32000 9.6.6.2): look the PDF encoding's glyph name
        // up there directly, the same way CFF/Type1 already resolve a
        // glyph through their own name tables regardless of cmap.
        let post_glyph_ids: Option<HashMap<String, skrifa::GlyphId>> =
            face.post().ok().map(|post| {
                (0..post.num_names() as u16)
                    .filter_map(|gid| {
                        post.glyph_name(skrifa::raw::types::GlyphId16::new(gid))
                            .map(|name| (name.to_string(), skrifa::GlyphId::from(gid)))
                    })
                    .collect()
            });
        let code_length = if matches!(self.fallback_kind, FontFallback::Utf16Be) {
            self.code_lengths.first().copied().unwrap_or(2).max(1)
        } else {
            1
        };
        // A CIDFontType0 (CFF-keyed CID font) can legally be embedded as a
        // full OpenType wrapper (`/FontFile3 /Subtype /OpenType`) rather
        // than a bare CIDFontType0C table -- and unlike CIDFontType2
        // (TrueType-based), its CID is never the same as its internal glyph
        // index: a CID-keyed CFF's own `charset` table is what actually maps
        // GID -> CID, and that mapping is font-specific, not identity, for
        // real-world CJK subsets. Treating the CID as a GID directly (as is
        // correct for CIDFontType2's raw code) resolves to an unrelated --
        // often out-of-range -- glyph. Detect this by the presence of the
        // sfnt's own `CFF ` table and resolve through the same CFF-charset
        // reverse map (`cid_to_gid`) the bare-CFF path below already uses.
        let cff_cid_to_gid = self
            .identity_cid
            .then(|| {
                face.data_for_tag(Tag::new(b"CFF "))
                    .and_then(|table| stet_fonts::cff_parser::parse_cff(table.as_bytes()).ok())
                    .and_then(|fonts| fonts.into_iter().next())
                    .map(|font| font.cid_to_gid)
            })
            .flatten();
        let mut builder = SvgGlyphOutline::new(units_per_em);
        let mut x_offset = 0.0;
        let mut has_visible_character = false;
        for code in bytes.chunks(code_length) {
            let (decoded, replacement) = self.decode(code);
            builder.x_offset = x_offset;
            if self.identity_cid {
                // Identity-H/V means the raw code already is the CID
                // (PDF32000 9.7.5.2), and CIDFontType2's own /CIDToGIDMap
                // (or its Identity default, when absent) is what names the
                // glyph -- not the embedded font's cmap, which a subsetted
                // CID font commonly ships without, or with one that has no
                // usable Unicode coverage at all. A ToUnicode gap
                // (`replacement`) is irrelevant here: it affects only
                // text extraction, never this lookup.
                has_visible_character |=
                    replacement || decoded.chars().any(|character| !character.is_whitespace());
                let cid = bytes_to_u32(code);
                let gid = if let Some(cid_to_gid) = cff_cid_to_gid.as_ref() {
                    cid_to_gid
                        .get(cid as usize)
                        .copied()
                        .map(u32::from)
                        .unwrap_or(0)
                } else {
                    self.cid_to_gid_map.as_ref().map_or(cid, |map| {
                        let offset = (cid as usize) * 2;
                        map.get(offset..offset + 2)
                            .map(|pair| u32::from(u16::from_be_bytes([pair[0], pair[1]])))
                            .unwrap_or(0)
                    })
                };
                let glyph = outlines
                    .get(skrifa::GlyphId::new(gid))
                    .ok_or("embedded font glyph outline is unavailable")?;
                glyph
                    .draw(
                        DrawSettings::unhinted(Size::unscaled(), LocationRef::default()),
                        &mut builder,
                    )
                    .map_err(|_| "embedded font glyph outline could not be decoded")?;
            } else {
                // A ToUnicode gap (`replacement`) or the total absence of a
                // /ToUnicode map only affects text extraction, not glyph
                // selection: a symbolic font (`glyph_names` empty) resolves
                // through its own cmap by raw code in the branch below,
                // trying that before it ever looks at `character`, and a
                // non-symbolic font can still fall back to its own
                // /Differences-named glyph via the font's post table.
                // Bailing out here unconditionally dropped every glyph
                // whose code had no ToUnicode entry, even when the font's
                // own encoding could resolve it directly.
                for character in decoded.chars() {
                    has_visible_character |= !character.is_whitespace();
                    // A font with no /Encoding is symbolic by the PDF spec's
                    // own default (9.6.6.4), and a symbolic simple font
                    // selects glyphs by raw character code through the
                    // font's own cmap, never through Unicode. Subsetters
                    // commonly key that cmap by sequential code (1, 2, 3,
                    // ...) rather than true Unicode, so mapping through the
                    // ToUnicode-decoded character first can land on an
                    // unrelated glyph whose raw code happens to equal that
                    // character's own codepoint.
                    let glyph_id = if self.glyph_names.is_empty() {
                        cmap.as_ref()
                            .and_then(|cmap| map_embedded_cmap(cmap, bytes_to_u32(code)))
                            .or_else(|| charmap.map(character))
                            .or_else(|| {
                                cmap.as_ref()
                                    .and_then(|cmap| map_embedded_cmap(cmap, u32::from(character)))
                            })
                    } else {
                        charmap
                            .map(character)
                            .or_else(|| {
                                cmap.as_ref()
                                    .and_then(|cmap| map_embedded_cmap(cmap, u32::from(character)))
                            })
                            .or_else(|| {
                                cmap.as_ref()
                                    .and_then(|cmap| map_embedded_cmap(cmap, bytes_to_u32(code)))
                            })
                    }
                    .or_else(|| {
                        code.first()
                            .and_then(|code| self.glyph_names.get(code))
                            .and_then(|name| post_glyph_ids.as_ref()?.get(name.as_str()).copied())
                    })
                    .ok_or("Unicode character has no glyph in the embedded font")?;
                    let glyph = outlines
                        .get(glyph_id)
                        .ok_or("embedded font glyph outline is unavailable")?;
                    glyph
                        .draw(
                            DrawSettings::unhinted(Size::unscaled(), LocationRef::default()),
                            &mut builder,
                        )
                        .map_err(|_| "embedded font glyph outline could not be decoded")?;
                }
            }
            let word_spacing = if decoded == " " { word_spacing_em } else { 0.0 };
            x_offset += self
                .widths
                .get(&bytes_to_u32(code))
                .copied()
                .unwrap_or(self.default_width)
                / 1_000.0
                + character_spacing_em
                + word_spacing;
        }
        if builder.path.is_empty() {
            if has_visible_character {
                Err("text contains no visible glyph outlines")
            } else {
                Ok(String::new())
            }
        } else {
            Ok(builder.path)
        }
    }

    fn outline_type1(
        &self,
        data: &[u8],
        bytes: &[u8],
        character_spacing_em: f64,
        word_spacing_em: f64,
    ) -> std::result::Result<String, &'static str> {
        let Some(font) = self
            .type1
            .0
            .get_or_init(|| {
                stet_fonts::type1_parser::parse_type1(&strip_pfb_segments(data))
                    .ok()
                    .map(Box::new)
            })
            .as_deref()
        else {
            return self.outline_cff(data, bytes, character_spacing_em, word_spacing_em);
        };
        let lookup = |name: &str| font.charstrings.get(name).cloned();
        let mut path = String::new();
        let mut x_offset = 0.0;
        let mut has_visible_character = false;
        // A CIDFontType0 descendant is only ever supposed to carry a bare
        // CFF (CIDFontType0C) or OpenType program, never a plain Type1
        // `/FontFile` -- but real-world producers sometimes embed one
        // anyway. Identity-H/V still means the raw code is two bytes per
        // PDF32000 9.7.5.2 regardless of what program type backs it, so
        // this must chunk the same way `outline_cff` already does for the
        // analogous bare-CFF case, or every high zero byte of a CID under
        // 256 shows up as its own spurious one-byte lookup.
        let code_length = if self.identity_cid { 2 } else { 1 };
        for code in bytes.chunks(code_length) {
            // A ToUnicode CMap that has no entry for this code (`replacement`)
            // only means text extraction can't recover its Unicode value --
            // it says nothing about whether the glyph itself exists. Many
            // Type1 fonts (TeX math fonts, ligature glyphs) have codes with
            // a real, drawable glyph but no sensible Unicode equivalent, so
            // glyph selection is attempted via the font's own encoding
            // below regardless, and only reported as unresolvable if that
            // also fails.
            let (decoded, _replacement) = self.decode(code);
            has_visible_character |= decoded.chars().any(|character| !character.is_whitespace());
            let glyph_name = if self.identity_cid {
                // No CID-keyed charset exists in a Type1 program at all;
                // the only workable interpretation of a Type1 font pressed
                // into service this way is that its own built-in Encoding
                // was built to name each CID's glyph directly by that same
                // numeric code, mirroring the non-CID lookup just below.
                font.encoding
                    .get(bytes_to_u32(code) as usize)
                    .map(String::as_str)
            } else {
                self.glyph_names
                    .get(&code[0])
                    .map(String::as_str)
                    .or_else(|| font.encoding.get(usize::from(code[0])).map(String::as_str))
            }
            .filter(|name| !name.is_empty() && *name != ".notdef")
            .or_else(|| (!decoded.is_empty()).then_some(decoded.as_str()))
            .ok_or("Type1 character code has no glyph name")?;
            if let Some(charstring) = font.charstrings.get(glyph_name) {
                let outline = stet_fonts::charstring::execute_charstring_ex(
                    charstring,
                    &font.subrs,
                    font.len_iv,
                    false,
                    Some(&lookup),
                )
                .map_err(|_| "Type1 glyph outline could not be decoded")?;
                append_stet_path(&mut path, &outline.path, font.font_matrix, x_offset);
            } else if !decoded.chars().all(char::is_whitespace) {
                return Err("Type1 glyph name is absent from CharStrings");
            }
            let word_spacing = if decoded == " " { word_spacing_em } else { 0.0 };
            x_offset += self
                .widths
                .get(&bytes_to_u32(code))
                .copied()
                .unwrap_or(self.default_width)
                / 1_000.0
                + character_spacing_em
                + word_spacing;
        }
        if path.is_empty() {
            if has_visible_character {
                Err("Type1 text contains no visible glyph outlines")
            } else {
                Ok(String::new())
            }
        } else {
            Ok(path)
        }
    }

    fn outline_cff(
        &self,
        data: &[u8],
        bytes: &[u8],
        character_spacing_em: f64,
        word_spacing_em: f64,
    ) -> std::result::Result<String, &'static str> {
        let fonts = stet_fonts::cff_parser::parse_cff(data)
            .map_err(|_| "embedded font program is neither OpenType, Type1, nor CFF")?;
        let font = fonts.first().ok_or("CFF font set is empty")?;
        let mut path = String::new();
        let mut x_offset = 0.0;
        let mut has_visible_character = false;
        let code_length = if self.identity_cid { 2 } else { 1 };
        for code in bytes.chunks(code_length) {
            // A ToUnicode CMap gap (`replacement`) means text extraction
            // can't recover this code's Unicode value, not that the glyph
            // is missing: math and symbol CFF fonts routinely carry glyphs
            // with no sensible Unicode equivalent. Glyph selection below
            // uses the font's own charset/encoding first regardless, and
            // this is only reported as unresolvable if that also fails.
            let (decoded, _replacement) = self.decode(code);
            has_visible_character |= decoded.chars().any(|character| !character.is_whitespace());
            let glyph_id = if self.identity_cid {
                // Identity-H/V: the code already is the CID (PDF32000
                // 9.7.5.2). A CID-keyed CFF's own charset maps GID -> CID,
                // not GID -> name, so the name-/Unicode-based lookup below
                // has nothing to match against; font.cid_to_gid is the
                // parser's own reverse of that map, using 0xFFFF (not 0) as
                // its own sentinel for "this CID has no entry" -- GID 0 is
                // conventionally .notdef, but nothing stops a real
                // subsetter from storing an actually-used glyph's outline
                // there while leaving the charset's own placeholder name
                // for it as ".notdef" regardless; treating a resolved GID
                // of exactly 0 as "not found" then discarded that glyph
                // outright even though its charstring draws real content.
                font.cid_to_gid
                    .get(bytes_to_u32(code) as usize)
                    .copied()
                    .map(usize::from)
                    .filter(|glyph_id| *glyph_id != 0xFFFF)
            } else {
                self.glyph_names
                    .get(&code[0])
                    .and_then(|name| font.charset.iter().position(|candidate| candidate == name))
                    .or_else(|| {
                        let mut characters = decoded.chars();
                        let character = characters.next()?;
                        if characters.next().is_some() || u32::from(character) > u32::from(u16::MAX)
                        {
                            return None;
                        }
                        font.charset.iter().position(|name| {
                            stet_fonts::agl::glyph_name_to_unicode(name) == Some(character as u16)
                        })
                    })
                    .or_else(|| {
                        font.encoding
                            .get(usize::from(code[0]))
                            .copied()
                            .map(usize::from)
                            .filter(|glyph_id| *glyph_id != 0)
                    })
            };
            if let Some(glyph_id) = glyph_id {
                let charstring = font
                    .char_strings
                    .get(glyph_id)
                    .ok_or("CFF glyph index is outside CharStrings")?;
                let (local_subrs, default_width, nominal_width, font_matrix) = if font.is_cid {
                    let fd_index = font
                        .fd_select
                        .get(glyph_id)
                        .copied()
                        .map(usize::from)
                        .unwrap_or(0);
                    let fd = font
                        .fd_array
                        .get(fd_index)
                        .ok_or("CFF CID glyph has no font dictionary")?;
                    (
                        fd.local_subrs.as_slice(),
                        fd.default_width_x,
                        fd.nominal_width_x,
                        fd.font_matrix.unwrap_or(font.font_matrix),
                    )
                } else {
                    (
                        font.local_subrs.as_slice(),
                        font.default_width_x,
                        font.nominal_width_x,
                        font.font_matrix,
                    )
                };
                let outline = stet_fonts::type2_charstring::execute_type2_charstring(
                    charstring,
                    local_subrs,
                    &font.global_subrs,
                    default_width,
                    nominal_width,
                    false,
                )
                .map_err(|_| "CFF Type2 glyph outline could not be decoded")?;
                if let Some((adx, ady, base_code, accent_code)) = outline.seac {
                    // Deprecated Type 1/2 "seac" composition (Adobe TN#5177
                    // Appendix C): this glyph's own charstring is nothing
                    // but `adx ady bchar achar endchar`, composing it from
                    // two other glyphs of this same font -- named by
                    // StandardEncoding code, never by this PDF's own
                    // /Differences encoding -- placed at the glyph origin
                    // and at (adx, ady) respectively. Common in older
                    // CFF/Type 1 fonts for accented Latin letters (an
                    // accent mark glyph composed onto a base letter), and
                    // without this, such a glyph has no outline at all.
                    for (code, dx, dy) in [(base_code, 0.0, 0.0), (accent_code, adx, ady)] {
                        let Some(name) = stet_fonts::encoding::standard_encoding_name(code) else {
                            continue;
                        };
                        let Some(component_id) = font
                            .charset
                            .iter()
                            .position(|candidate| candidate.as_str() == name)
                        else {
                            continue;
                        };
                        let Some(component_charstring) = font.char_strings.get(component_id) else {
                            continue;
                        };
                        let Ok(component) = stet_fonts::type2_charstring::execute_type2_charstring(
                            component_charstring,
                            local_subrs,
                            &font.global_subrs,
                            default_width,
                            nominal_width,
                            false,
                        ) else {
                            continue;
                        };
                        let component_matrix = compose(font_matrix, [1.0, 0.0, 0.0, 1.0, dx, dy]);
                        append_stet_path(&mut path, &component.path, component_matrix, x_offset);
                    }
                } else {
                    append_stet_path(&mut path, &outline.path, font_matrix, x_offset);
                }
            } else if !decoded.chars().all(char::is_whitespace) {
                return Err("CFF character code has no glyph");
            }
            let word_spacing = if decoded == " " { word_spacing_em } else { 0.0 };
            x_offset += self
                .widths
                .get(&bytes_to_u32(code))
                .copied()
                .unwrap_or(self.default_width)
                / 1_000.0
                + character_spacing_em
                + word_spacing;
        }
        if path.is_empty() {
            if has_visible_character {
                Err("CFF text contains no visible glyph outlines")
            } else {
                Ok(String::new())
            }
        } else {
            Ok(path)
        }
    }
}

fn map_embedded_cmap(
    cmap: &skrifa::raw::tables::cmap::Cmap<'_>,
    codepoint: u32,
) -> Option<skrifa::GlyphId> {
    // Raw cmap lookups may return .notdef; keep searching before falling
    // back to the PDF character code, matching the previous parser contract.
    cmap.encoding_records()
        .iter()
        .filter_map(|record| record.subtable(cmap.offset_data()).ok())
        .filter_map(|subtable| subtable.map_codepoint(codepoint))
        .find(|glyph| *glyph != skrifa::GlyphId::NOTDEF)
}

struct SvgGlyphOutline {
    path: String,
    units_per_em: f64,
    x_offset: f64,
}

impl SvgGlyphOutline {
    fn new(units_per_em: f64) -> Self {
        Self {
            path: String::new(),
            units_per_em,
            x_offset: 0.0,
        }
    }

    fn point(&self, x: f32, y: f32) -> (f64, f64) {
        (
            self.x_offset + f64::from(x) / self.units_per_em,
            f64::from(y) / self.units_per_em,
        )
    }

    fn command(&mut self, operator: &str, points: &[(f64, f64)]) {
        if !self.path.is_empty() {
            self.path.push(' ');
        }
        self.path.push_str(operator);
        for (x, y) in points {
            self.path.push_str(&format!(" {} {}", fmt(*x), fmt(*y)));
        }
    }
}

impl skrifa::outline::OutlinePen for SvgGlyphOutline {
    fn move_to(&mut self, x: f32, y: f32) {
        let point = self.point(x, y);
        self.command("M", &[point]);
    }

    fn line_to(&mut self, x: f32, y: f32) {
        let point = self.point(x, y);
        self.command("L", &[point]);
    }

    fn quad_to(&mut self, x1: f32, y1: f32, x: f32, y: f32) {
        let control = self.point(x1, y1);
        let point = self.point(x, y);
        self.command("Q", &[control, point]);
    }

    fn curve_to(&mut self, x1: f32, y1: f32, x2: f32, y2: f32, x: f32, y: f32) {
        let first = self.point(x1, y1);
        let second = self.point(x2, y2);
        let point = self.point(x, y);
        self.command("C", &[first, second, point]);
    }

    fn close(&mut self) {
        self.command("Z", &[]);
    }
}

fn append_stet_path(
    output: &mut String,
    path: &stet_fonts::PsPath,
    matrix: [f64; 6],
    x_offset: f64,
) {
    let transform = |x: f64, y: f64| {
        (
            x_offset + matrix[0] * x + matrix[2] * y + matrix[4],
            matrix[1] * x + matrix[3] * y + matrix[5],
        )
    };
    for segment in &path.segments {
        if !output.is_empty() {
            output.push(' ');
        }
        match *segment {
            stet_fonts::PathSegment::MoveTo(x, y) => {
                let point = transform(x, y);
                output.push_str(&format!("M {} {}", fmt(point.0), fmt(point.1)));
            }
            stet_fonts::PathSegment::LineTo(x, y) => {
                let point = transform(x, y);
                output.push_str(&format!("L {} {}", fmt(point.0), fmt(point.1)));
            }
            stet_fonts::PathSegment::CurveTo {
                x1,
                y1,
                x2,
                y2,
                x3,
                y3,
            } => {
                let first = transform(x1, y1);
                let second = transform(x2, y2);
                let third = transform(x3, y3);
                output.push_str(&format!(
                    "C {} {} {} {} {} {}",
                    fmt(first.0),
                    fmt(first.1),
                    fmt(second.0),
                    fmt(second.1),
                    fmt(third.0),
                    fmt(third.1)
                ));
            }
            stet_fonts::PathSegment::ClosePath => output.push('Z'),
        }
    }
}

struct Interpreter<'a, 'page> {
    document: &'a Document,
    page: &'page mut Page,
    page_matrix: Matrix,
    page_id: ObjectId,
    fonts: HashMap<Vec<u8>, FontDecoder>,
    resources: Vec<Dictionary>,
    state: GraphicsState,
    content_base_ctm: Matrix,
    stack: Vec<SavedGraphicsState>,
    path: PathBuilder,
    pending_clip_rule: Option<String>,
    text: TextState,
    node_counter: usize,
    clip_counter: usize,
    mask_counter: usize,
    compatibility_depth: usize,
    visited_forms: HashSet<ObjectId>,
    visited_patterns: HashSet<ObjectId>,
    mesh_output_count: Rc<Cell<usize>>,
    hidden_ocgs: HashSet<ObjectId>,
    marked_content_hidden: bool,
    marked_content_stack: Vec<bool>,
    content_limit: usize,
    outline_embedded_pdf_text: bool,
}

impl Interpreter<'_, '_> {
    fn interpret(&mut self, operations: &[Operation], depth: usize) -> Result<()> {
        if depth > MAX_FORM_DEPTH {
            return Err(Error::LimitExceeded(format!(
                "PDF Form XObject recursion exceeds {MAX_FORM_DEPTH}"
            )));
        }
        for operation in operations {
            if self.node_counter >= MAX_PDF_PAGE_NODES - MAX_PAGE_MESH_TRIANGLES {
                self.page.warn(
                    "PDF page reached its bounded content-node budget; remaining content operators were omitted to reserve mesh-rendering capacity",
                );
                break;
            }
            self.operator(operation, depth)?;
        }
        Ok(())
    }

    fn operator(&mut self, operation: &Operation, depth: usize) -> Result<()> {
        let operands = &operation.operands;
        match operation.operator.as_str() {
            "BX" => self.compatibility_depth = self.compatibility_depth.saturating_add(1),
            "EX" => self.compatibility_depth = self.compatibility_depth.saturating_sub(1),
            "q" => {
                if self.stack.len() >= MAX_GRAPHICS_STACK {
                    return Err(Error::LimitExceeded(format!(
                        "PDF graphics-state stack exceeds {MAX_GRAPHICS_STACK}"
                    )));
                }
                self.stack.push(SavedGraphicsState {
                    graphics: self.state.clone(),
                    text: self.text.saved_parameters(),
                });
            }
            "Q" => {
                if let Some(saved) = self.stack.pop() {
                    self.state = saved.graphics;
                    self.text.restore_parameters(saved.text);
                } else {
                    self.page.warn("PDF Q operator has no matching q");
                }
            }
            "cm" => {
                if let Some(matrix) = matrix_operands(operands) {
                    let previous = self.state.ctm;
                    let next = compose(previous, matrix);
                    let fill = self.state.fill.clone();
                    let stroke = self.state.stroke.clone();
                    self.state.fill = self.rebase_pattern_paint(&fill, previous, next);
                    self.state.stroke = self.rebase_pattern_paint(&stroke, previous, next);
                    self.state.ctm = next;
                }
            }
            "w" => self.state.line_width = number(operands.first()).unwrap_or(1.0).max(0.0),
            "J" => {
                self.state.line_cap = match integer(operands.first()).unwrap_or(0) {
                    1 => LineCap::Round,
                    2 => LineCap::Square,
                    _ => LineCap::Butt,
                };
            }
            "j" => {
                self.state.line_join = match integer(operands.first()).unwrap_or(0) {
                    1 => LineJoin::Round,
                    2 => LineJoin::Bevel,
                    _ => LineJoin::Miter,
                };
            }
            "M" => self.state.miter_limit = number(operands.first()).unwrap_or(10.0).max(1.0),
            "d" => self.apply_dash(operands),
            "m" => self.path.command("M", &numbers(operands, 2)),
            "l" => self.path.command("L", &numbers(operands, 2)),
            "c" => self.path.command("C", &numbers(operands, 6)),
            "v" => {
                let values = numbers(operands, 4);
                if values.len() == 4
                    && let Some((current_x, current_y)) = self.path.current_point
                {
                    self.path.command(
                        "C",
                        &[
                            current_x, current_y, values[0], values[1], values[2], values[3],
                        ],
                    );
                }
            }
            "y" => {
                let values = numbers(operands, 4);
                if values.len() == 4 {
                    self.path.command(
                        "C",
                        &[
                            values[0], values[1], values[2], values[3], values[2], values[3],
                        ],
                    );
                }
            }
            "h" => self.path.command("Z", &[]),
            "re" => {
                let values = numbers(operands, 4);
                if values.len() == 4 {
                    let [x, y, width, height] = [values[0], values[1], values[2], values[3]];
                    self.path.add_rect(x, y, width, height);
                }
            }
            "W" => self.pending_clip_rule = Some("nonzero".into()),
            "W*" => self.pending_clip_rule = Some("evenodd".into()),
            "S" => self.paint_path(false, true, false, "nonzero"),
            "s" => self.paint_path(false, true, true, "nonzero"),
            "f" | "F" => self.paint_path(true, false, false, "nonzero"),
            "f*" => self.paint_path(true, false, false, "evenodd"),
            "B" => self.paint_path(true, true, false, "nonzero"),
            "B*" => self.paint_path(true, true, false, "evenodd"),
            "b" => self.paint_path(true, true, true, "nonzero"),
            "b*" => self.paint_path(true, true, true, "evenodd"),
            "n" => self.finish_clip_and_clear(),
            "g" => {
                self.state.fill_color_space = Object::Name(b"DeviceGray".to_vec());
                self.state.fill_pattern_clip = None;
                self.state.fill = gray_paint(
                    number(operands.first()).unwrap_or(0.0),
                    self.state.fill_alpha,
                )
            }
            "G" => {
                self.state.stroke_color_space = Object::Name(b"DeviceGray".to_vec());
                self.state.stroke_pattern_clip = None;
                self.state.stroke = gray_paint(
                    number(operands.first()).unwrap_or(0.0),
                    self.state.stroke_alpha,
                )
            }
            "rg" => {
                self.state.fill_color_space = Object::Name(b"DeviceRGB".to_vec());
                self.state.fill_pattern_clip = None;
                self.state.fill = rgb_paint(&numbers(operands, 3), self.state.fill_alpha);
            }
            "RG" => {
                self.state.stroke_color_space = Object::Name(b"DeviceRGB".to_vec());
                self.state.stroke_pattern_clip = None;
                self.state.stroke = rgb_paint(&numbers(operands, 3), self.state.stroke_alpha);
            }
            "k" => {
                self.state.fill_color_space = Object::Name(b"DeviceCMYK".to_vec());
                self.state.fill_pattern_clip = None;
                self.state.fill = cmyk_paint(&numbers(operands, 4), self.state.fill_alpha);
            }
            "K" => {
                self.state.stroke_color_space = Object::Name(b"DeviceCMYK".to_vec());
                self.state.stroke_pattern_clip = None;
                self.state.stroke = cmyk_paint(&numbers(operands, 4), self.state.stroke_alpha);
            }
            "cs" => {
                if let Some(name) = name(operands.first()) {
                    self.state.fill_color_space = self.resolve_color_space_name(name);
                    self.state.fill_pattern_clip = None;
                }
            }
            "CS" => {
                if let Some(name) = name(operands.first()) {
                    self.state.stroke_color_space = self.resolve_color_space_name(name);
                    self.state.stroke_pattern_clip = None;
                }
            }
            "sc" | "scn" => self.set_current_color(false, operands),
            "SC" | "SCN" => self.set_current_color(true, operands),
            "BT" => {
                self.text.text_matrix = IDENTITY;
                self.text.line_matrix = IDENTITY;
                self.text.pending_clips.clear();
            }
            "Tf" => {
                self.text.font_name = name(operands.first()).unwrap_or_default().to_vec();
                self.text.font_size = number(operands.get(1)).unwrap_or(12.0).abs();
            }
            "Tm" => {
                if let Some(matrix) = matrix_operands(operands) {
                    self.text.text_matrix = matrix;
                    self.text.line_matrix = matrix;
                }
            }
            "Td" => self.move_text(
                number(operands.first()).unwrap_or(0.0),
                number(operands.get(1)).unwrap_or(0.0),
            ),
            "TD" => {
                let y = number(operands.get(1)).unwrap_or(0.0);
                self.text.leading = -y;
                self.move_text(number(operands.first()).unwrap_or(0.0), y);
            }
            "T*" => self.move_text(0.0, -self.text.leading),
            "Tc" => self.text.character_spacing = number(operands.first()).unwrap_or(0.0),
            "Tw" => self.text.word_spacing = number(operands.first()).unwrap_or(0.0),
            "Tz" => self.text.horizontal_scale = number(operands.first()).unwrap_or(100.0) / 100.0,
            "TL" => self.text.leading = number(operands.first()).unwrap_or(0.0),
            "Ts" => self.text.rise = number(operands.first()).unwrap_or(0.0),
            "Tr" => self.text.rendering_mode = integer(operands.first()).unwrap_or(0),
            "Tj" => {
                if let Some(bytes) = string_bytes(operands.first()) {
                    self.show_text(bytes);
                }
            }
            "TJ" => self.show_text_array(operands.first()),
            "'" => {
                self.move_text(0.0, -self.text.leading);
                if let Some(bytes) = string_bytes(operands.first()) {
                    self.show_text(bytes);
                }
            }
            "\"" => {
                self.text.word_spacing = number(operands.first()).unwrap_or(0.0);
                self.text.character_spacing = number(operands.get(1)).unwrap_or(0.0);
                self.move_text(0.0, -self.text.leading);
                if let Some(bytes) = string_bytes(operands.get(2)) {
                    self.show_text(bytes);
                }
            }
            "Do" => {
                if let Some(name) = name(operands.first()) {
                    self.draw_xobject(name, depth)?;
                }
            }
            "gs" => {
                if let Some(name) = name(operands.first()) {
                    self.apply_ext_gstate(name)?;
                }
            }
            "sh" => {
                if let Some(name) = name(operands.first()) {
                    self.draw_shading(name)?;
                }
            }
            "BI" => {
                if let Some(Object::Stream(stream)) = operands.first() {
                    let inline_image = normalize_inline_image(stream.clone());
                    self.draw_image(&inline_image, b"inline")?;
                } else {
                    self.page.warn(
                        "PDF filtered inline image was skipped by the syntax decoder and needs native filter recovery",
                    );
                }
            }
            "ID" | "EI" => {}
            "ET" => self.apply_pending_text_clips(),
            "T_s" | "T_w" | "T_L" | "T_c" => {}
            "BDC" => {
                let tag = name(operands.first()).unwrap_or_default();
                let hidden_here = if tag == b"OC" {
                    match operands.get(1) {
                        Some(Object::Name(property_name)) => self
                            .lookup_named_resource_with_id(b"Properties", property_name)
                            .is_some_and(|(object_id, object)| {
                                !self.is_oc_visible(object_id, &object)
                            }),
                        Some(dictionary_operand @ Object::Dictionary(_)) => {
                            !self.is_oc_visible(None, dictionary_operand)
                        }
                        _ => false,
                    }
                } else {
                    false
                };
                let now_hidden = self.marked_content_hidden || hidden_here;
                self.marked_content_stack.push(now_hidden);
                self.marked_content_hidden = now_hidden;
            }
            "BMC" => {
                self.marked_content_stack.push(self.marked_content_hidden);
            }
            "EMC" => {
                self.marked_content_stack.pop();
                self.marked_content_hidden =
                    self.marked_content_stack.last().copied().unwrap_or(false);
            }
            unsupported
                if self.compatibility_depth == 0
                    && !matches!(unsupported, "ri" | "i" | "d0" | "d1" | "MP" | "DP") =>
            {
                self.page
                    .warn(format!("PDF operator {unsupported} is not yet implemented"));
            }
            _ => {}
        }
        Ok(())
    }

    fn apply_dash(&mut self, operands: &[Object]) {
        self.state.dash_array = operands
            .first()
            .and_then(|object| object.as_array().ok())
            .map(|values| {
                values
                    .iter()
                    .filter_map(|value| number(Some(value)))
                    .collect()
            })
            .unwrap_or_default();
        self.state.dash_offset = number(operands.get(1)).unwrap_or(0.0);
    }

    fn resolve_color_space_name(&self, name: &[u8]) -> Object {
        match name {
            b"DeviceGray" | b"G" | b"DeviceRGB" | b"RGB" | b"DeviceCMYK" | b"CMYK" | b"Pattern" => {
                Object::Name(name.to_vec())
            }
            _ => self
                .lookup_named_resource(b"ColorSpace", name)
                .unwrap_or_else(|| Object::Name(name.to_vec())),
        }
    }

    fn resolve_color_space_object(&self, object: &Object) -> Object {
        let resolved = self
            .document
            .dereference(object)
            .ok()
            .map(|(_, value)| value)
            .unwrap_or(object);
        if let Object::Name(name) = resolved {
            self.resolve_color_space_name(name)
        } else {
            resolved.clone()
        }
    }

    fn set_current_color(&mut self, stroke: bool, operands: &[Object]) {
        let color_space = if stroke {
            self.state.stroke_color_space.clone()
        } else {
            self.state.fill_color_space.clone()
        };
        if pdf_color_space_is_pattern(self.document, &color_space) {
            let Some(pattern_name) = operands.iter().rev().find_map(|value| value.as_name().ok())
            else {
                self.page
                    .warn("PDF Pattern color selection has no pattern name");
                return;
            };
            let opacity = if stroke {
                self.state.stroke_alpha
            } else {
                self.state.fill_alpha
            };
            let Some((paint, pattern_clip)) =
                self.pattern_paint(pattern_name, &color_space, operands, opacity)
            else {
                return;
            };
            if stroke {
                self.state.stroke = paint;
                self.state.stroke_pattern_clip = pattern_clip;
            } else {
                self.state.fill = paint;
                self.state.fill_pattern_clip = pattern_clip;
            }
            return;
        }
        let components = numbers(operands, usize::MAX);
        let opacity = if stroke {
            self.state.stroke_alpha
        } else {
            self.state.fill_alpha
        };
        let paint = Paint::Solid {
            color: components_to_color(self.document, Some(&color_space), &components),
            opacity,
        };
        if stroke {
            self.state.stroke = paint;
            self.state.stroke_pattern_clip = None;
        } else {
            self.state.fill = paint;
            self.state.fill_pattern_clip = None;
        }
    }

    fn rebase_pattern_paint(&mut self, paint: &Paint, previous: Matrix, next: Matrix) -> Paint {
        let Paint::PatternRef { id, opacity } = paint else {
            return paint.clone();
        };
        let Some(inverse) = inverse_matrix(next) else {
            return paint.clone();
        };
        let Some(mut definition) = self
            .page
            .patterns
            .iter()
            .find(|pattern| pattern.id == *id)
            .cloned()
        else {
            return paint.clone();
        };
        definition.transform = compose(inverse, compose(previous, definition.transform));
        definition.id = pattern_variant_id(id, definition.transform);
        let variant_id = definition.id.clone();
        if !self
            .page
            .patterns
            .iter()
            .any(|pattern| pattern.id == variant_id)
        {
            self.page.patterns.push(definition);
        }
        Paint::PatternRef {
            id: variant_id,
            opacity: *opacity,
        }
    }

    fn pattern_paint(
        &mut self,
        pattern_name: &[u8],
        pattern_color_space: &Object,
        operands: &[Object],
        opacity: f64,
    ) -> Option<(Paint, Option<PatternClip>)> {
        let Some(pattern) = self.lookup_named_resource(b"Pattern", pattern_name) else {
            self.page.warn(format!(
                "PDF pattern {} was not found",
                String::from_utf8_lossy(pattern_name)
            ));
            return None;
        };
        let pattern_dictionary = match &pattern {
            Object::Dictionary(dictionary) => dictionary,
            Object::Stream(stream) => &stream.dict,
            _ => {
                self.page.warn("PDF Pattern resource is not a dictionary");
                return None;
            }
        };
        let pattern_type = pattern_dictionary
            .get(b"PatternType")
            .and_then(Object::as_i64)
            .unwrap_or(0);
        if pattern_type == 1 {
            return self.tiling_pattern_paint(pattern_name, pattern_color_space, operands, opacity);
        }
        if pattern_type != 2 {
            self.page.warn(format!(
                "PDF pattern {} has unsupported PatternType {pattern_type}",
                String::from_utf8_lossy(pattern_name)
            ));
            return None;
        }
        let shading_object = pattern_dictionary.get(b"Shading").ok()?;
        let (_, shading_object) = self.document.dereference(shading_object).ok()?;
        let shading_dictionary = match shading_object {
            Object::Dictionary(dictionary) => dictionary,
            Object::Stream(stream) => &stream.dict,
            _ => {
                self.page
                    .warn("PDF shading pattern has no shading dictionary");
                return None;
            }
        };
        let shading_type = shading_dictionary
            .get(b"ShadingType")
            .and_then(Object::as_i64)
            .unwrap_or(0);
        if shading_type == 1 {
            return self.function_shading_pattern_paint(
                pattern_name,
                pattern_dictionary,
                shading_dictionary,
                opacity,
            );
        }
        if matches!(shading_type, 4..=7) {
            return self.mesh_shading_pattern_paint(
                pattern_name,
                pattern_dictionary,
                shading_object,
                shading_dictionary,
                shading_type,
                opacity,
            );
        }
        if !matches!(shading_type, 2 | 3) {
            self.page.warn(format!(
                "PDF shading PatternType 2 uses unsupported shading type {shading_type}"
            ));
            return None;
        }
        let coordinates = shading_dictionary
            .get(b"Coords")
            .and_then(Object::as_array)
            .ok()
            .map(|values| numbers(values, 6))
            .unwrap_or_default();
        let required = if shading_type == 2 { 4 } else { 6 };
        if coordinates.len() != required {
            self.page
                .warn("PDF shading PatternType 2 has invalid /Coords");
            return None;
        }
        let function = shading_dictionary.get(b"Function").ok()?;
        let domain = shading_dictionary
            .get(b"Domain")
            .and_then(Object::as_array)
            .ok()
            .map(|values| numbers(values, 2))
            .filter(|values| values.len() == 2)
            .unwrap_or_else(|| vec![0.0, 1.0]);
        let color_space = shading_dictionary.get(b"ColorSpace").ok();
        let extend = shading_dictionary
            .get(b"Extend")
            .and_then(Object::as_array)
            .ok()
            .map(|values| {
                [
                    values
                        .first()
                        .and_then(|value| value.as_bool().ok())
                        .unwrap_or(false),
                    values
                        .get(1)
                        .and_then(|value| value.as_bool().ok())
                        .unwrap_or(false),
                ]
            })
            .unwrap_or([false, false]);
        let opacity = opacity.clamp(0.0, 1.0);
        let background_components = shading_dictionary
            .get(b"Background")
            .and_then(Object::as_array)
            .ok()
            .map(|values| numbers(values, usize::MAX));
        let background_rgb = background_components
            .as_ref()
            .and_then(|components| components_to_rgb(self.document, color_space, components, 0));
        let background = background_components
            .as_ref()
            .map(|values| components_to_color(self.document, color_space, values));
        let layered_opacity = if background_rgb.is_some() {
            opacity * (2.0 - opacity)
        } else {
            opacity
        };
        let mut stops = Vec::with_capacity(35);
        for index in 0..=32 {
            let offset = f64::from(index) / 32.0;
            let input = domain[0] + (domain[1] - domain[0]) * offset;
            let Some(components) = evaluate_pdf_function(self.document, function, input, 0) else {
                self.page
                    .warn("PDF shading pattern uses an unsupported function");
                return None;
            };
            let color = if let Some(background_rgb) = background_rgb {
                let source = components_to_rgb(self.document, color_space, &components, 0)
                    .unwrap_or_else(|| default_rgb_components(&components));
                let denominator = (2.0 - opacity).max(1e-12);
                let layered = std::array::from_fn(|channel| {
                    (source[channel] + (1.0 - opacity) * background_rgb[channel]) / denominator
                });
                let [red, green, blue] = rgb_to_bytes(layered);
                format!("#{red:02X}{green:02X}{blue:02X}")
            } else {
                components_to_color(self.document, color_space, &components)
            };
            stops.push(GradientStop {
                offset,
                color,
                opacity: layered_opacity,
            });
        }
        apply_gradient_extension_with_background(
            &mut stops,
            extend,
            background.as_deref(),
            opacity,
        );
        let pattern_matrix = pattern_dictionary
            .get(b"Matrix")
            .and_then(Object::as_array)
            .ok()
            .and_then(|values| matrix_operands(values))
            .unwrap_or(IDENTITY);
        let pattern_matrix = inverse_matrix(self.state.ctm)
            .map(|inverse| compose(inverse, compose(self.content_base_ctm, pattern_matrix)))
            .unwrap_or(pattern_matrix);
        let pattern_clip = shading_dictionary
            .get(b"BBox")
            .and_then(Object::as_array)
            .ok()
            .map(|values| numbers(values, 4))
            .filter(|values| values.len() == 4)
            .map(|bbox| PatternClip {
                bbox: [bbox[0], bbox[1], bbox[2], bbox[3]],
                matrix: pattern_matrix,
            });
        if shading_type == 2 {
            let (x1, y1, x2, y2) = transformed_axial_axis(
                pattern_matrix,
                coordinates[0],
                coordinates[1],
                coordinates[2],
                coordinates[3],
            )?;
            return Some((
                Paint::LinearGradient(Box::new(LinearGradient {
                    x1,
                    y1,
                    x2,
                    y2,
                    stops,
                })),
                pattern_clip,
            ));
        }
        let mut first_radius = coordinates[2].max(0.0);
        let mut second_radius = coordinates[5].max(0.0);
        let mut first_x = coordinates[0];
        let mut first_y = coordinates[1];
        let mut second_x = coordinates[3];
        let mut second_y = coordinates[4];
        let center_distance = (second_x - first_x).hypot(second_y - first_y);
        if center_distance + first_radius.min(second_radius)
            > first_radius.max(second_radius) + 1e-9
        {
            self.page
                .warn("PDF noncontained radial shading pattern requires field tessellation");
            return None;
        }
        if first_radius > second_radius {
            std::mem::swap(&mut first_radius, &mut second_radius);
            std::mem::swap(&mut first_x, &mut second_x);
            std::mem::swap(&mut first_y, &mut second_y);
            for stop in &mut stops {
                stop.offset = 1.0 - stop.offset;
            }
            stops.reverse();
        }
        Some((
            Paint::RadialGradient(Box::new(RadialGradient {
                fx: first_x,
                fy: first_y,
                fr: first_radius,
                cx: second_x,
                cy: second_y,
                radius: second_radius.max(1e-9),
                transform: pattern_matrix,
                stops,
            })),
            pattern_clip,
        ))
    }

    /// Paints a PDF shading pattern (`PatternType 2`) whose `ShadingType` is
    /// 1 (function-based) -- a case with no SVG gradient equivalent, unlike
    /// the axial/radial types above. The tessellated cells (same
    /// tessellation as the `sh` operator uses) are captured into a
    /// [`TilingPatternDefinition`] sized to the shading's own `/Domain`,
    /// which becomes an SVG `<pattern>` any path can reference as a fill.
    fn function_shading_pattern_paint(
        &mut self,
        pattern_name: &[u8],
        pattern_dictionary: &Dictionary,
        shading_dictionary: &Dictionary,
        opacity: f64,
    ) -> Option<(Paint, Option<PatternClip>)> {
        let function = shading_dictionary.get(b"Function").ok()?;
        let domain = shading_dictionary
            .get(b"Domain")
            .and_then(Object::as_array)
            .ok()
            .map(|values| numbers(values, 4))
            .filter(|values| values.len() == 4)
            .unwrap_or_else(|| vec![0.0, 1.0, 0.0, 1.0]);
        let color_space = shading_dictionary.get(b"ColorSpace").ok();
        let pattern_matrix = pattern_dictionary
            .get(b"Matrix")
            .and_then(Object::as_array)
            .ok()
            .and_then(|values| matrix_operands(values))
            .unwrap_or(IDENTITY);
        let pattern_matrix = inverse_matrix(self.state.ctm)
            .map(|inverse| compose(inverse, compose(self.content_base_ctm, pattern_matrix)))
            .unwrap_or(pattern_matrix);
        let transform_key = pattern_matrix
            .iter()
            .map(|value| format!("{:x}", value.to_bits()))
            .collect::<Vec<_>>()
            .join("-");
        let id = format!(
            "pdf-shading-pattern-{}-{transform_key}",
            pattern_name
                .iter()
                .map(|byte| format!("{byte:02x}"))
                .collect::<String>()
        );
        let opacity = opacity.clamp(0.0, 1.0);
        // A tessellated pattern's tile only ever covers the shading's own
        // domain; unlike a real PDF shading pattern, an SVG <pattern> tiles
        // to cover whatever it fills, so without this clip a fill path
        // larger than the domain would show repeated copies of it.
        let pattern_clip = Some(PatternClip {
            bbox: [domain[0], domain[2], domain[1], domain[3]],
            matrix: pattern_matrix,
        });
        if self.page.patterns.iter().any(|pattern| pattern.id == id) {
            return Some((Paint::PatternRef { id, opacity }, pattern_clip));
        }
        let Some((nodes, truncated)) = build_function_shading_cell_nodes(
            self.document,
            function,
            &domain,
            IDENTITY,
            color_space,
            self.state.fill_alpha,
            &self.state.blend_mode,
            self.state.mask_id.as_deref().unwrap_or_default(),
            self.state.alpha_is_shape,
            None,
            self.page.number,
            "pdf-function-pattern-cell",
            &String::from_utf8_lossy(pattern_name),
        ) else {
            self.page.warn(format!(
                "PDF shading pattern {} uses an unsupported function",
                String::from_utf8_lossy(pattern_name)
            ));
            return None;
        };
        if truncated {
            self.page.warn(format!(
                "PDF shading pattern {} is too fine-grained to render exactly; showing a lower-resolution approximation",
                String::from_utf8_lossy(pattern_name)
            ));
        }
        let width = (domain[1] - domain[0]).abs().max(1e-6);
        let height = (domain[3] - domain[2]).abs().max(1e-6);
        self.page.patterns.push(TilingPatternDefinition {
            id: id.clone(),
            x: domain[0],
            y: domain[2],
            width: width + pattern_tile_margin(width),
            height: height + pattern_tile_margin(height),
            transform: pattern_matrix,
            nodes,
        });
        Some((Paint::PatternRef { id, opacity }, pattern_clip))
    }

    /// Paints a PDF shading pattern (`PatternType 2`) whose `ShadingType` is
    /// 4-7 (a free-form, lattice-form, Coons-patch or tensor-patch mesh) --
    /// another case with no SVG gradient equivalent. The mesh's own
    /// triangles (the same tessellation the `sh` operator uses) are
    /// captured into a [`TilingPatternDefinition`] sized to their actual
    /// vertex bounds, becoming an SVG `<pattern>` any path can reference.
    fn mesh_shading_pattern_paint(
        &mut self,
        pattern_name: &[u8],
        pattern_dictionary: &Dictionary,
        shading_object: &Object,
        shading_dictionary: &Dictionary,
        shading_type: i64,
        opacity: f64,
    ) -> Option<(Paint, Option<PatternClip>)> {
        let pattern_matrix = pattern_dictionary
            .get(b"Matrix")
            .and_then(Object::as_array)
            .ok()
            .and_then(|values| matrix_operands(values))
            .unwrap_or(IDENTITY);
        let pattern_matrix = inverse_matrix(self.state.ctm)
            .map(|inverse| compose(inverse, compose(self.content_base_ctm, pattern_matrix)))
            .unwrap_or(pattern_matrix);
        let transform_key = pattern_matrix
            .iter()
            .map(|value| format!("{:x}", value.to_bits()))
            .collect::<Vec<_>>()
            .join("-");
        let id = format!(
            "pdf-shading-pattern-{}-{transform_key}",
            pattern_name
                .iter()
                .map(|byte| format!("{byte:02x}"))
                .collect::<String>()
        );
        let opacity = opacity.clamp(0.0, 1.0);
        // Unlike the other pattern kinds, a mesh pattern is not cached by
        // id and re-skipped on a repeat fill: its bounding box (needed for
        // the clip below) only falls out of parsing the mesh data, so a
        // second reference just re-tessellates rather than tracking bounds
        // on the side for what is, in practice, a rare pattern to reuse.
        let parsed = parse_mesh_shading_triangles(
            self.document,
            shading_object,
            shading_dictionary,
            shading_type,
            self.content_limit,
            self.mesh_output_count.get(),
            pattern_name,
            self.page,
        );
        let (triangles, subdivisions, color_space) = match parsed {
            Ok(Some(parsed)) => parsed,
            Ok(None) => return None,
            Err(error) => {
                self.page.warn(format!(
                    "PDF shading pattern {} was skipped: {error}",
                    String::from_utf8_lossy(pattern_name)
                ));
                return None;
            }
        };
        let mut min_x = f64::INFINITY;
        let mut max_x = f64::NEG_INFINITY;
        let mut min_y = f64::INFINITY;
        let mut max_y = f64::NEG_INFINITY;
        for triangle in &triangles {
            for vertex in &triangle.0 {
                min_x = min_x.min(vertex.x);
                max_x = max_x.max(vertex.x);
                min_y = min_y.min(vertex.y);
                max_y = max_y.max(vertex.y);
            }
        }
        if !min_x.is_finite() || !max_x.is_finite() || !min_y.is_finite() || !max_y.is_finite() {
            return None;
        }
        let nodes = build_mesh_triangle_nodes(
            self.document,
            &triangles,
            subdivisions,
            color_space.as_ref(),
            IDENTITY,
            self.state.fill_alpha,
            &self.state.blend_mode,
            self.state.mask_id.as_deref().unwrap_or_default(),
            self.state.alpha_is_shape,
            None,
            self.page.number,
            "pdf-mesh-pattern-cell",
            &String::from_utf8_lossy(pattern_name),
            &self.mesh_output_count,
        );
        if nodes.is_empty() {
            return None;
        }
        // A tessellated pattern's tile only ever covers the mesh's own
        // vertex bounds; unlike a real PDF shading pattern, an SVG
        // <pattern> tiles to cover whatever it fills, so without this clip
        // a fill path larger than those bounds would show repeated copies.
        let pattern_clip = Some(PatternClip {
            bbox: [min_x, min_y, max_x, max_y],
            matrix: pattern_matrix,
        });
        if !self.page.patterns.iter().any(|pattern| pattern.id == id) {
            let width = (max_x - min_x).max(1e-6);
            let height = (max_y - min_y).max(1e-6);
            self.page.patterns.push(TilingPatternDefinition {
                id: id.clone(),
                x: min_x,
                y: min_y,
                width: width + pattern_tile_margin(width),
                height: height + pattern_tile_margin(height),
                transform: pattern_matrix,
                nodes,
            });
        }
        Some((Paint::PatternRef { id, opacity }, pattern_clip))
    }
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
