ryusui-hiro/document-svg/src/document/bib.rs

//! Bounded BibTeX `.bib` bibliography preview.
//!
//! Parses entries and nested/quoted field values as text. BibTeX macros,
//! preambles, citation styles, crossrefs, and TeX commands are never executed.

use std::path::Path;

use crate::convert::{ConvertOptions, PageConsumer, read_limited_file};
use crate::document::html::{HtmlBlock, render_blocks_to_pages};
use crate::error::{Error, Result};

const MAX_BIB_BYTES: u64 = 64 * 1024 * 1024;
const MAX_BIB_LINES: usize = 1_000_000;
const MAX_BIB_LINE_BYTES: usize = 1024 * 1024;
const MAX_BIB_ENTRIES: usize = 100_000;
const MAX_BIB_RECORDS: usize = 100_000;
const MAX_BIB_FIELDS_PER_ENTRY: usize = 128;
const MAX_BIB_KEY_BYTES: usize = 1024;
const MAX_BIB_FIELD_NAME_BYTES: usize = 128;
const MAX_BIB_FIELD_VALUE_BYTES: usize = 2 * 1024 * 1024;
const MAX_BIB_ENTRY_BYTES: usize = 4 * 1024 * 1024;
const MAX_BIB_NESTING: usize = 64;
const MAX_BIB_RENDERED_TEXT_BYTES: usize = 32 * 1024 * 1024;

#[derive(Default)]
struct BibParser<'a> {
    text: &'a str,
    index: usize,
    entry_count: usize,
    records_processed: usize,
    rendered_bytes: usize,
    warnings: Vec<String>,
    blocks: Vec<HtmlBlock>,
}

pub(crate) fn convert(
    path: &Path,
    options: &ConvertOptions,
    sink: &mut dyn PageConsumer,
) -> Result<Vec<String>> {
    let bytes = read_limited_file(
        path,
        options.max_input_bytes.min(MAX_BIB_BYTES),
        "BibTeX input",
    )?;
    let text = String::from_utf8(bytes).map_err(|error| {
        Error::InvalidInput(format!("BibTeX input is not valid UTF-8: {error}"))
    })?;
    let (blocks, warnings) = parse_bibtex_blocks_with_warnings(&text)?;
    let mut sink = BibPageSink {
        inner: sink,
        warnings: &warnings,
    };
    render_blocks_to_pages(&blocks, &mut sink, options)?;
    Ok(warnings)
}

struct BibPageSink<'a> {
    inner: &'a mut dyn PageConsumer,
    warnings: &'a [String],
}

impl PageConsumer for BibPageSink<'_> {
    fn consume(&mut self, mut page: crate::ir::Page) -> Result<()> {
        page.source_format = "bib".into();
        if page.title.is_empty() {
            page.title = "BibTeX bibliography".into();
        }
        for warning in self.warnings {
            page.warn(warning.clone());
        }
        self.inner.consume(page)
    }
}

pub fn parse_bibtex_blocks(text: &str) -> Result<Vec<HtmlBlock>> {
    parse_bibtex_blocks_with_warnings(text).map(|(blocks, _)| blocks)
}

pub(crate) fn looks_like_bibtex_prefix(prefix: &[u8]) -> bool {
    let text = String::from_utf8_lossy(prefix);
    text.lines().take(100).any(|raw_line| {
        let line = raw_line.trim_start();
        let Some(rest) = line.strip_prefix('@') else {
            return false;
        };
        let type_end = rest
            .find(|character: char| !(character.is_ascii_alphanumeric() || character == '_'))
            .unwrap_or(rest.len());
        if type_end == 0 {
            return false;
        }
        let after_type = rest[type_end..].trim_start();
        let Some(open) = after_type
            .chars()
            .next()
            .filter(|character| matches!(character, '{' | '('))
        else {
            return false;
        };
        let body = after_type.get(open.len_utf8()..).unwrap_or_default();
        let closing = if open == '{' { '}' } else { ')' };
        let key = body
            .split_once(',')
            .map(|(key, _)| key.trim())
            .unwrap_or_default();
        !key.is_empty() && !key.starts_with(closing)
    })
}

fn parse_bibtex_blocks_with_warnings(text: &str) -> Result<(Vec<HtmlBlock>, Vec<String>)> {
    validate_bibtex(text)?;
    let mut parser = BibParser {
        text,
        ..BibParser::default()
    };
    parser.blocks.push(HtmlBlock::Heading {
        level: 1,
        text: "BibTeX bibliography".into(),
    });
    while parser.skip_space_and_comments() {
        if parser.peek_char() != Some('@') {
            parser.bump_char();
            continue;
        }
        parser.parse_record()?;
    }
    if parser.entry_count == 0 {
        push_bib_warning(
            &mut parser.warnings,
            "BibTeX input contains no supported entries",
        );
    }
    Ok((parser.blocks, parser.warnings))
}

fn validate_bibtex(text: &str) -> Result<()> {
    if text.len() as u64 > MAX_BIB_BYTES {
        return Err(Error::LimitExceeded(format!(
            "BibTeX input exceeds {MAX_BIB_BYTES} bytes"
        )));
    }
    let mut line_count = 0usize;
    for line in text.lines() {
        line_count += 1;
        if line_count > MAX_BIB_LINES {
            return Err(Error::LimitExceeded(format!(
                "BibTeX input exceeds {MAX_BIB_LINES} lines"
            )));
        }
        if line.len() > MAX_BIB_LINE_BYTES {
            return Err(Error::LimitExceeded(format!(
                "BibTeX line exceeds {MAX_BIB_LINE_BYTES} bytes"
            )));
        }
    }
    Ok(())
}
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
