ryusui-hiro/document-svg/src/document/bpmn.rs

//! Bounded BPMN 2.0 diagram previews using the model and Diagram Interchange data.

use std::collections::{HashMap, HashSet};
use std::path::Path;

use crate::convert::{ConvertOptions, PageConsumer, read_limited_file};
use crate::error::{Error, Result};
use crate::geospatial::xml_tree::{XmlElement, XmlLimits, parse_xml_tree};
use crate::ir::{
    IDENTITY, LineCap, LineJoin, Node, Page, Paint, SourceMeta, Stroke, TextAnchor, TextRun,
};

const BPMN_MODEL_NS: &str = "http://www.omg.org/spec/BPMN/20100524/MODEL";
const BPMN_DI_NS: &str = "http://www.omg.org/spec/BPMN/20100524/DI";
const DI_NS: &str = "http://www.omg.org/spec/DD/20100524/DI";
const DC_NS: &str = "http://www.omg.org/spec/DD/20100524/DC";

const MAX_BPMN_BYTES: u64 = 32 * 1024 * 1024;
const MAX_BPMN_EVENTS: usize = 500_000;
const MAX_BPMN_ELEMENTS: usize = 200_000;
const MAX_BPMN_DEPTH: usize = 80;
const MAX_BPMN_TEXT_BYTES: usize = 16 * 1024 * 1024;
const MAX_BPMN_DIAGRAMS: usize = 100;
const MAX_RENDERED_NODES: usize = 200_000;
const MAX_COORDINATE: f64 = 10_000_000.0;

const PAGE_WIDTH: f64 = 595.0;
const PAGE_HEIGHT: f64 = 842.0;
const PAGE_MARGIN: f64 = 38.0;

#[derive(Clone)]
struct ModelElement {
    id: String,
    name: String,
    kind: String,
}

#[derive(Clone, Copy)]
struct Rect {
    x: f64,
    y: f64,
    width: f64,
    height: f64,
}

#[derive(Clone)]
struct Shape {
    model_id: String,
    rect: Rect,
}

#[derive(Clone)]
struct Waypoint {
    x: f64,
    y: f64,
}

#[derive(Clone)]
struct Edge {
    model_id: String,
    points: Vec<Waypoint>,
}

type DiagramGeometry = (String, Vec<Shape>, Vec<Edge>);
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
